oldgerman/ODGIRON/Hardware/Datasheets/Amplifier/3223.INA333.png

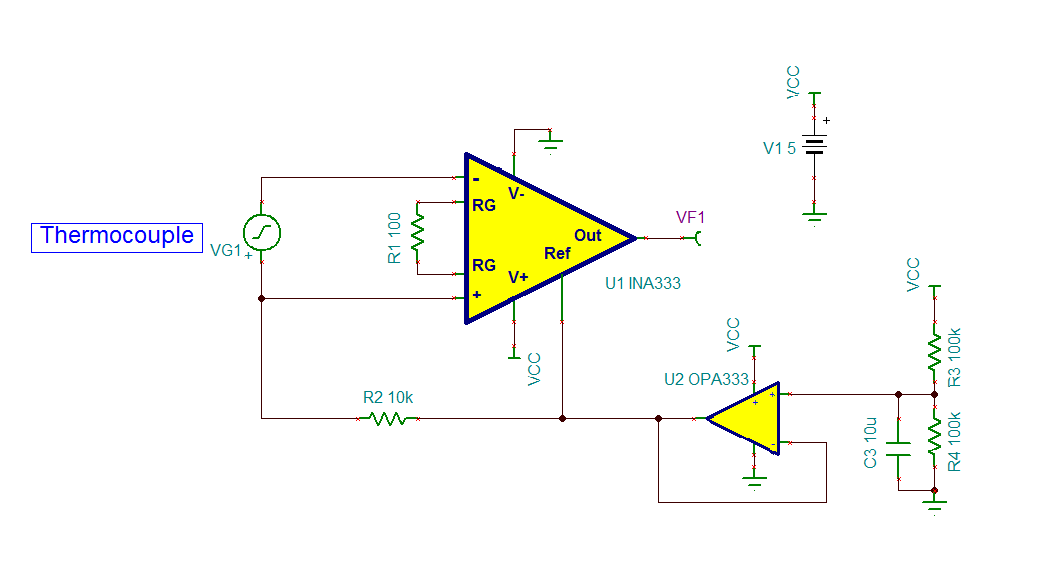
Hardware/Datasheets/Amplifier/3223.INA333.png
