oldgerman/ODGIRON/Hardware/Datasheets/Amplifier/INA333/1882.Untitled.png

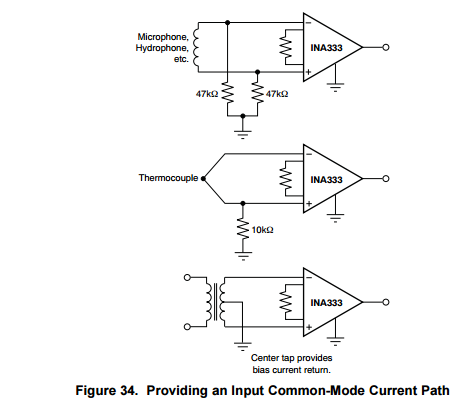
Hardware/Datasheets/Amplifier/INA333/1882.Untitled.png
