oldgerman/ODGIRON/Hardware/Datasheets/DCDC/image/MP2456_EVM_V1.jpg

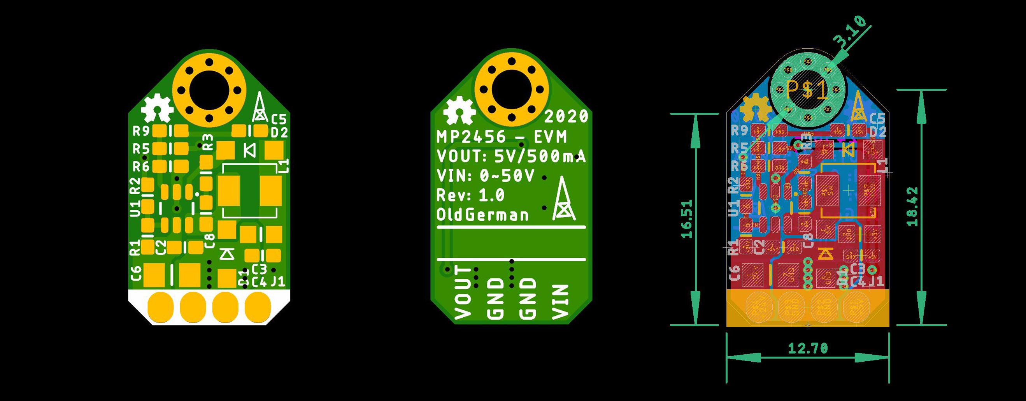
Hardware/Datasheets/DCDC/image/MP2456_EVM_V1.jpg
