oldgerman/ODGIRON/Hardware/Datasheets/DCDC/image/MP2456_EVM_V1_Module.JPG

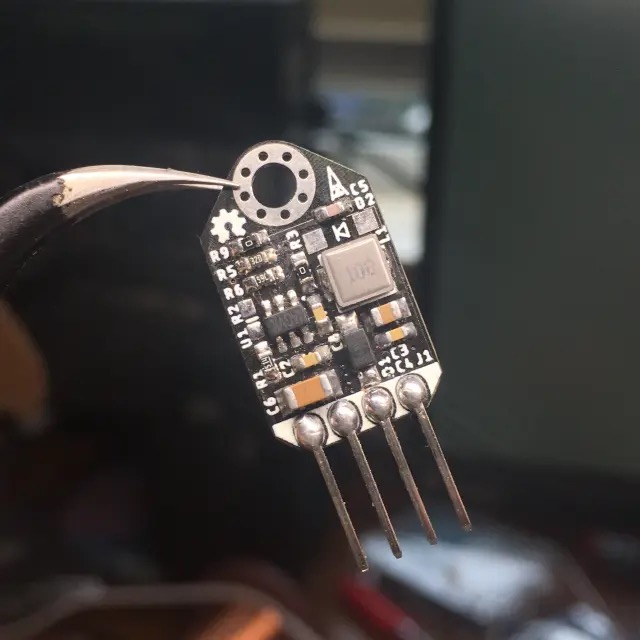
Hardware/Datasheets/DCDC/image/MP2456_EVM_V1_Module.JPG
