oldgerman/ODGIRON/Hardware/Datasheets/FUSB302/FUSB302BGEVB_-_Board/FUSB302BGEVB_-_Board.png

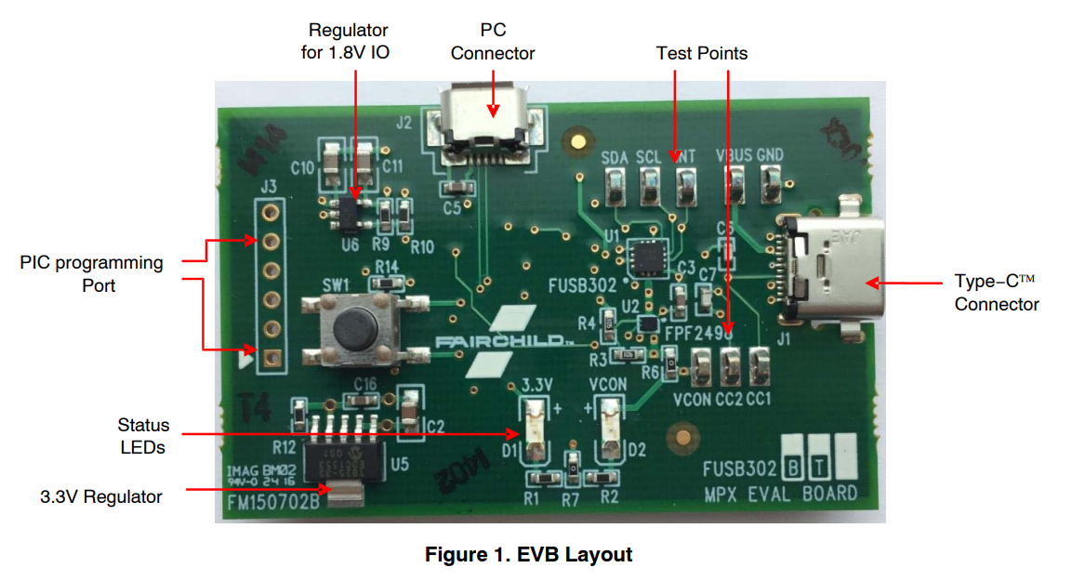
Hardware/Datasheets/FUSB302/FUSB302BGEVB_-_Board/FUSB302BGEVB_-_Board.png
