oldgerman/ODGIRON/Hardware/Datasheets/FUSB302/PD_BUDDY_SINK/pd_buddy_sink.jpg

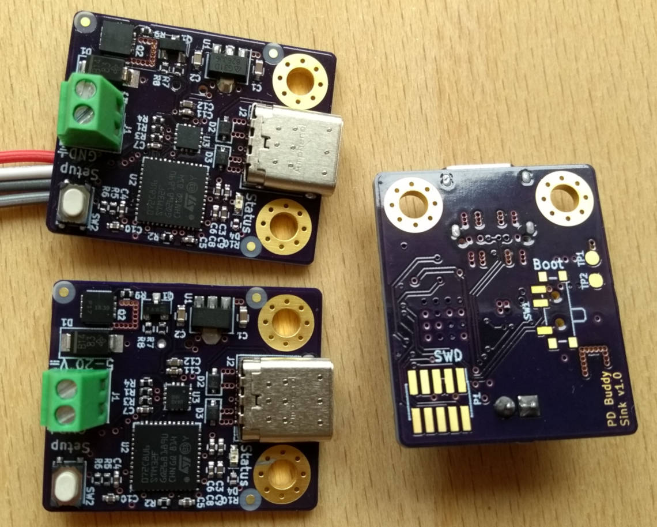
Hardware/Datasheets/FUSB302/PD_BUDDY_SINK/pd_buddy_sink.jpg
