oldgerman/ODGIRON/Hardware/Datasheets/FUSB302/USB-C Explorer/2018-03-14T04_09_01.173Z-Bot_cropped.jpg

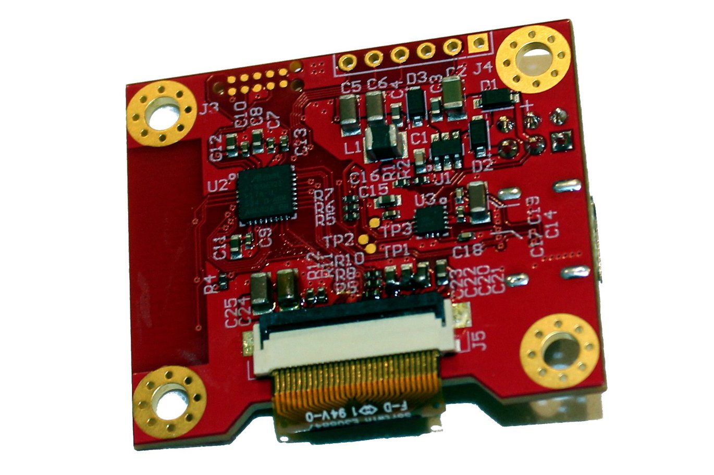
Hardware/Datasheets/FUSB302/USB-C Explorer/2018-03-14T04_09_01.173Z-Bot_cropped.jpg
