oldgerman/ODGIRON/Hardware/Datasheets/FUSB302/USB-PD-Breakout/2019-07-22T05_44_04.861Z-USB-C_PD_Breakout_Bot.jpg

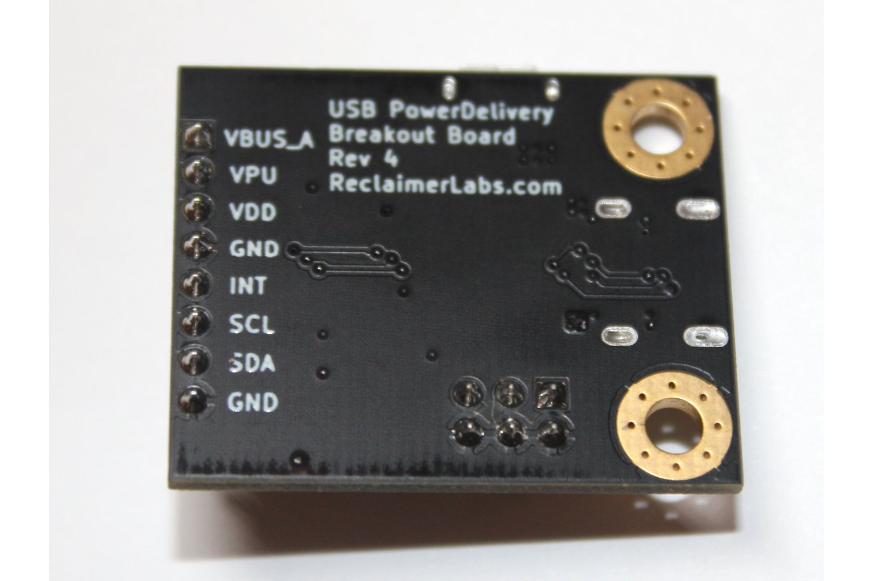
Hardware/Datasheets/FUSB302/USB-PD-Breakout/2019-07-22T05_44_04.861Z-USB-C_PD_Breakout_Bot.jpg
