oldgerman/ODGIRON/Hardware/Datasheets/FUSB302/USB-PD-Breakout/USB PowerDeilivery Breakout.jpg

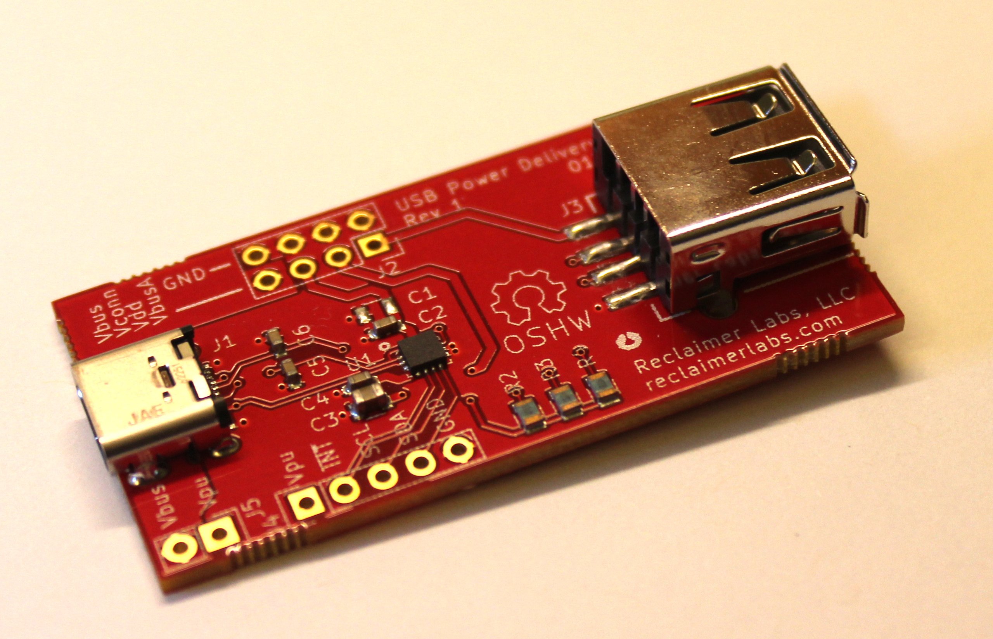
Hardware/Datasheets/FUSB302/USB-PD-Breakout/USB PowerDeilivery Breakout.jpg
