oldgerman/ODGIRON/Hardware/Datasheets/FUSB302/USB-PD-Breakout/USB PowerDeilivery Breakout.png

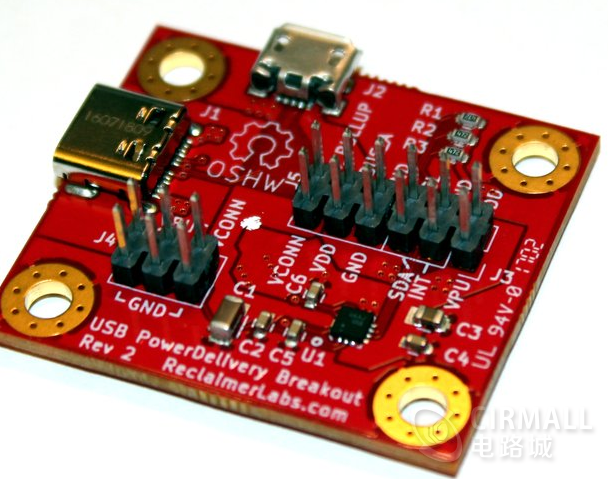
Hardware/Datasheets/FUSB302/USB-PD-Breakout/USB PowerDeilivery Breakout.png
