oldgerman/ODGIRON/Hardware/Datasheets/FUSB302/ZY12PDN/FUSB+STM_Schematic.png

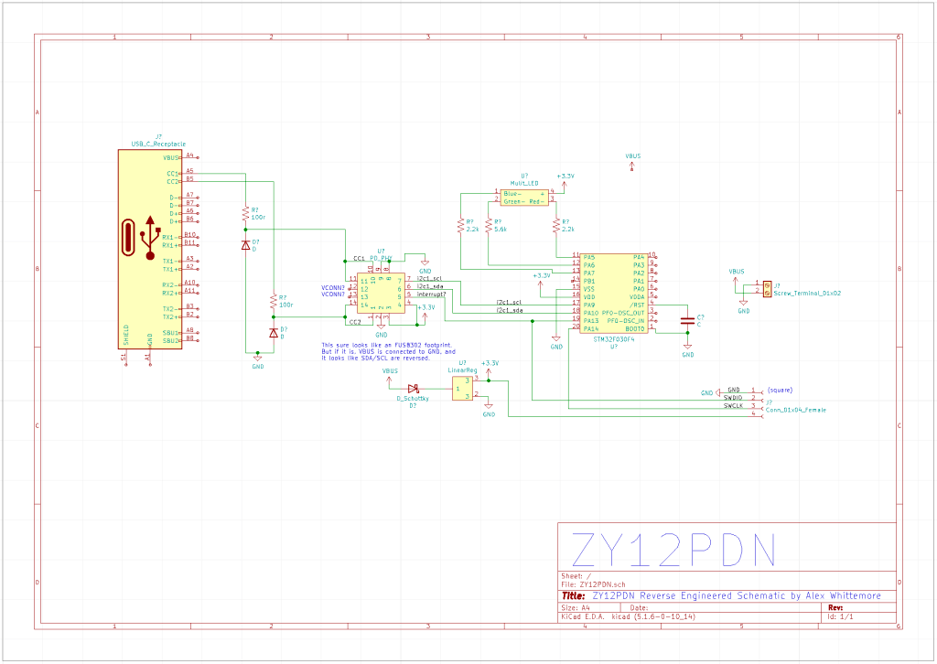
Hardware/Datasheets/FUSB302/ZY12PDN/FUSB+STM_Schematic.png
