oldgerman/ODGIRON/Hardware/Datasheets/FUSB302/产品应用/FUSB302在紫米10号移动电源中进行了应用，详情参考充电头网带来的ZMI 10号USB PD移动电源拆解.png

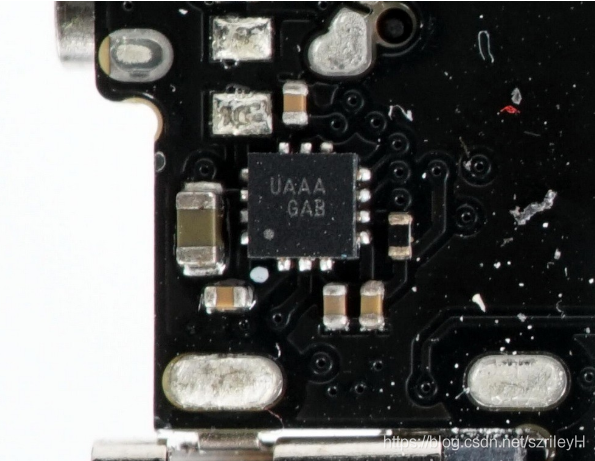
Hardware/Datasheets/FUSB302/产品应用/FUSB302在紫米10号移动电源中进行了应用，详情参考充电头网带来的ZMI 10号USB PD移动电源拆解.png
