oldgerman/ODGIRON/Hardware/Datasheets/MEMS/LIS2DH12/SEN0224-detail-001_564x376.jpg

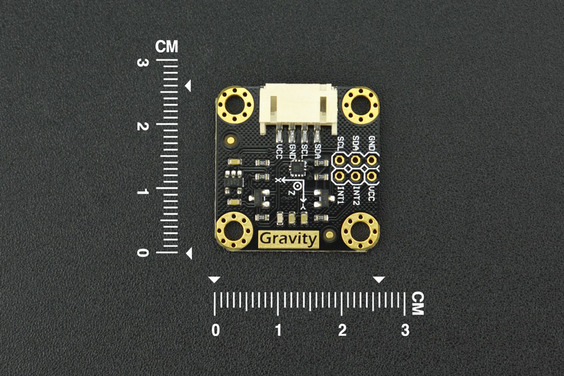
Hardware/Datasheets/MEMS/LIS2DH12/SEN0224-detail-001_564x376.jpg
