oldgerman/ODGIRON/Hardware/Datasheets/MEMS/LIS2DH12/SEN0224.jpg

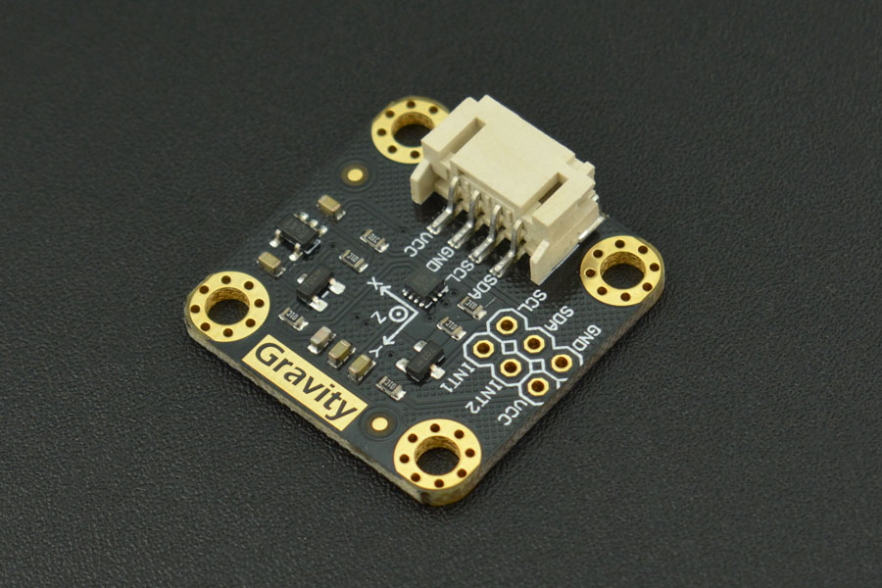
Hardware/Datasheets/MEMS/LIS2DH12/SEN0224.jpg
