oldgerman/ODGIRON/Hardware/Datasheets/MEMS/LIS3DH/Adafruit-LIS3DH-Breakout-PCB-master/3.3V电源从ic下面走没问题.png

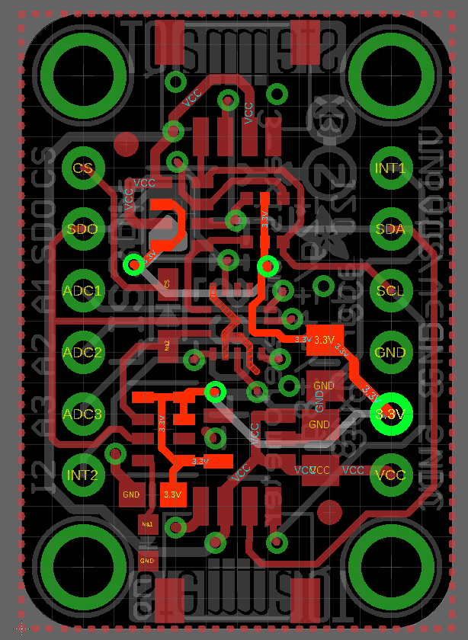
Hardware/Datasheets/MEMS/LIS3DH/Adafruit-LIS3DH-Breakout-PCB-master/3.3V电源从ic下面走没问题.png
