oldgerman/ODGIRON/Hardware/Datasheets/MEMS/LIS3DH/Adafruit-LIS3DH-Breakout-PCB-master/QWIC版本.jpg

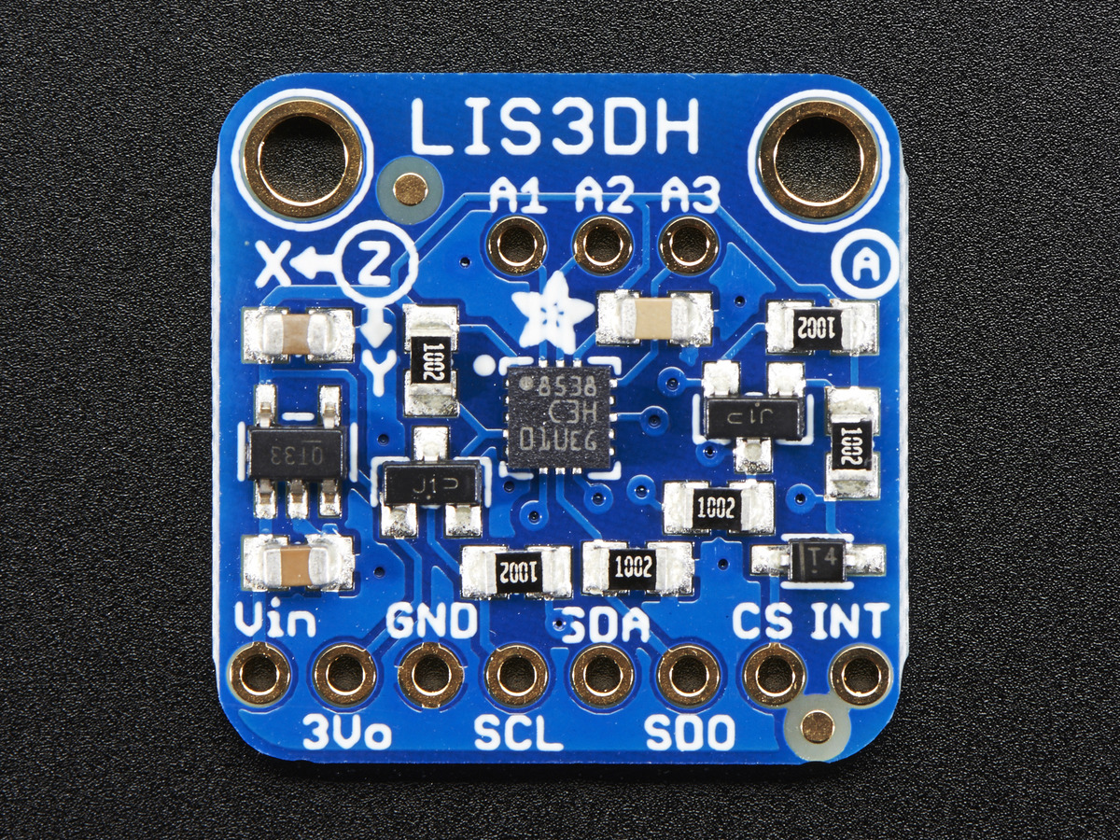
Hardware/Datasheets/MEMS/LIS3DH/Adafruit-LIS3DH-Breakout-PCB-master/QWIC版本.jpg
