oldgerman/ODGIRON/Hardware/Datasheets/MEMS/MPU9250/15335_9DoF_IMU_EagleFiles/20201105164445.png

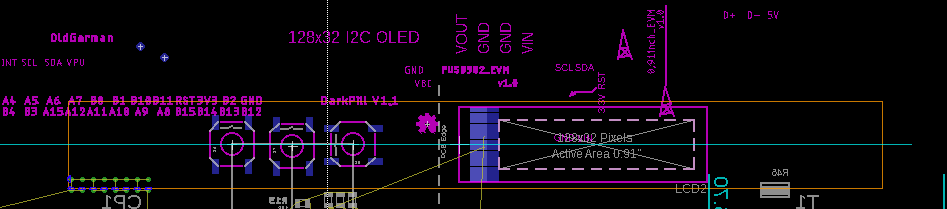
Hardware/Datasheets/MEMS/MPU9250/15335_9DoF_IMU_EagleFiles/20201105164445.png
