oldgerman/ODGIRON/Hardware/Datasheets/MEMS/MPU9250/15335_9DoF_IMU_EagleFiles/20201105170118.png

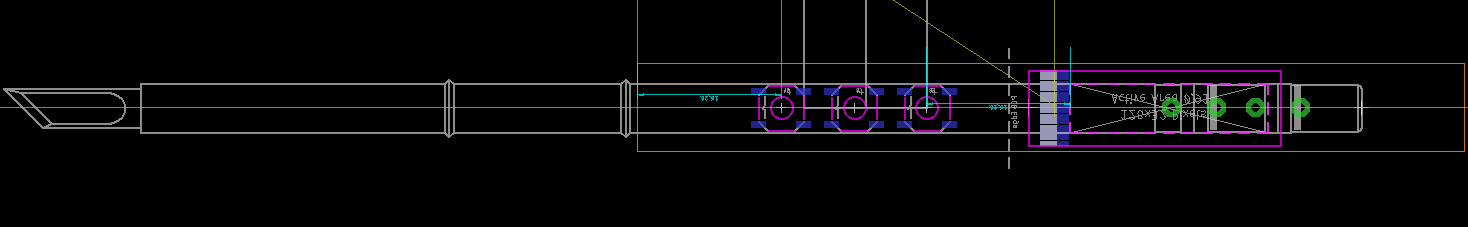
Hardware/Datasheets/MEMS/MPU9250/15335_9DoF_IMU_EagleFiles/20201105170118.png
