oldgerman/ODGIRON/Hardware/Datasheets/MOSFET/MOSFET共漏极、共栅极、共源极接法.jpg

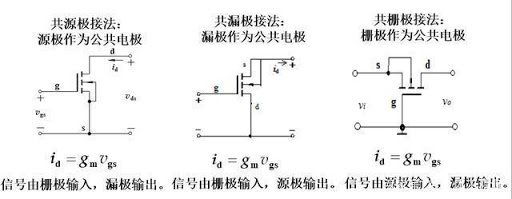
Hardware/Datasheets/MOSFET/MOSFET共漏极、共栅极、共源极接法.jpg
