oldgerman/ODGIRON/Hardware/Datasheets/MOSFET/schematicpwm.png

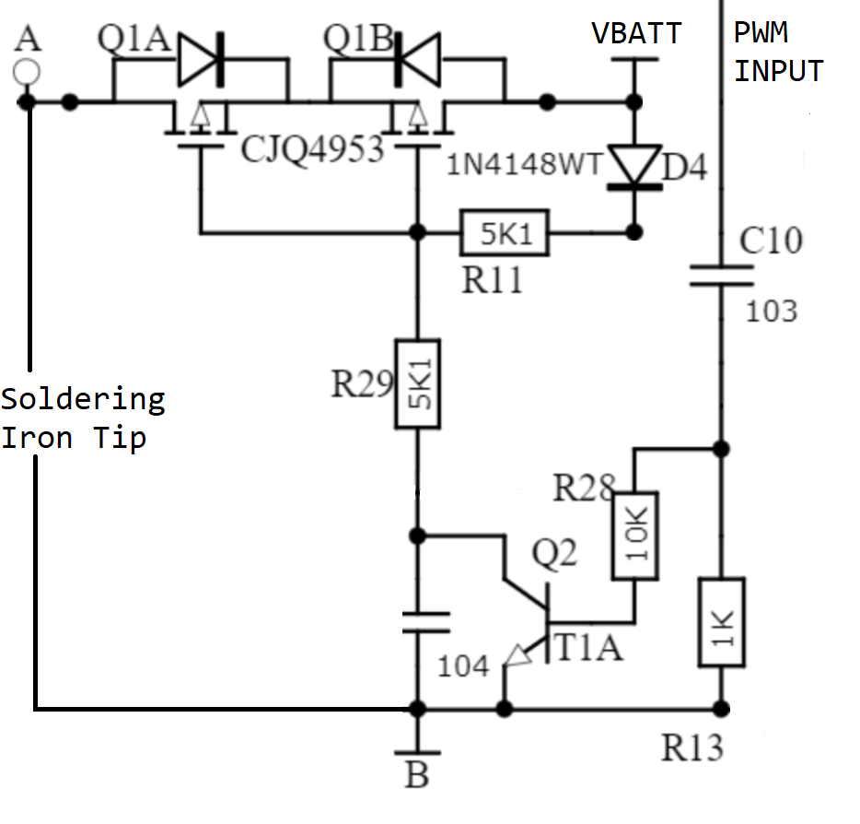
Hardware/Datasheets/MOSFET/schematicpwm.png
