oldgerman/ODGIRON/Hardware/Datasheets/MOSFET/Sic4-4_graf01.gif

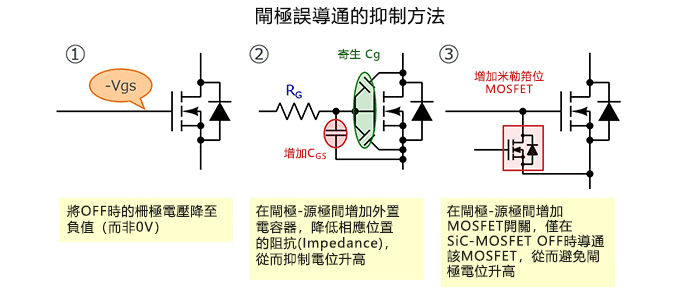
Hardware/Datasheets/MOSFET/Sic4-4_graf01.gif
