oldgerman/ODGIRON/Hardware/Datasheets/STUSB4500/15801-SparkFun_Power_Delivery_Board_-_USB-C__Qwiic_-02.jpg

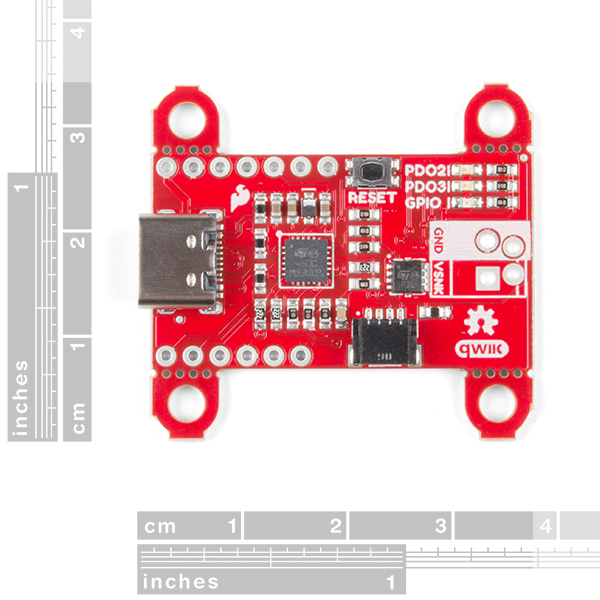
Hardware/Datasheets/STUSB4500/15801-SparkFun_Power_Delivery_Board_-_USB-C__Qwiic_-02.jpg
