oldgerman/ODGIRON/Hardware/Datasheets/STUSB4500/15801-SparkFun_Power_Delivery_Board_-_USB-C__Qwiic_-03.jpg

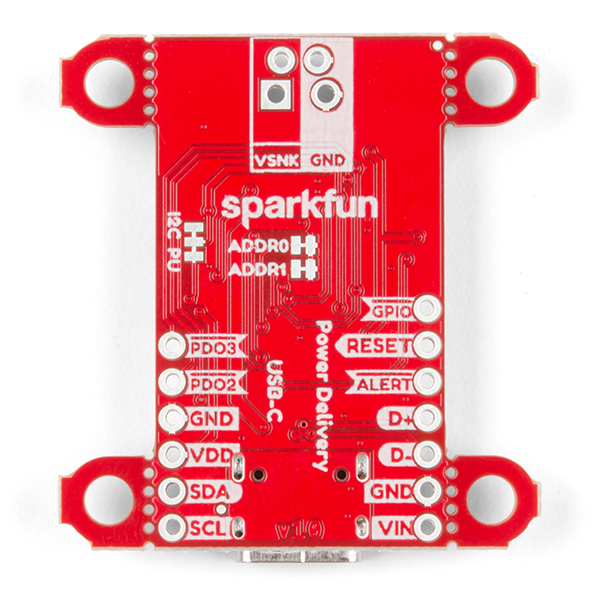
Hardware/Datasheets/STUSB4500/15801-SparkFun_Power_Delivery_Board_-_USB-C__Qwiic_-03.jpg
