oldgerman/ODGIRON/Hardware/Datasheets/T12烙铁头结构/973c747dd97206d3.jpg

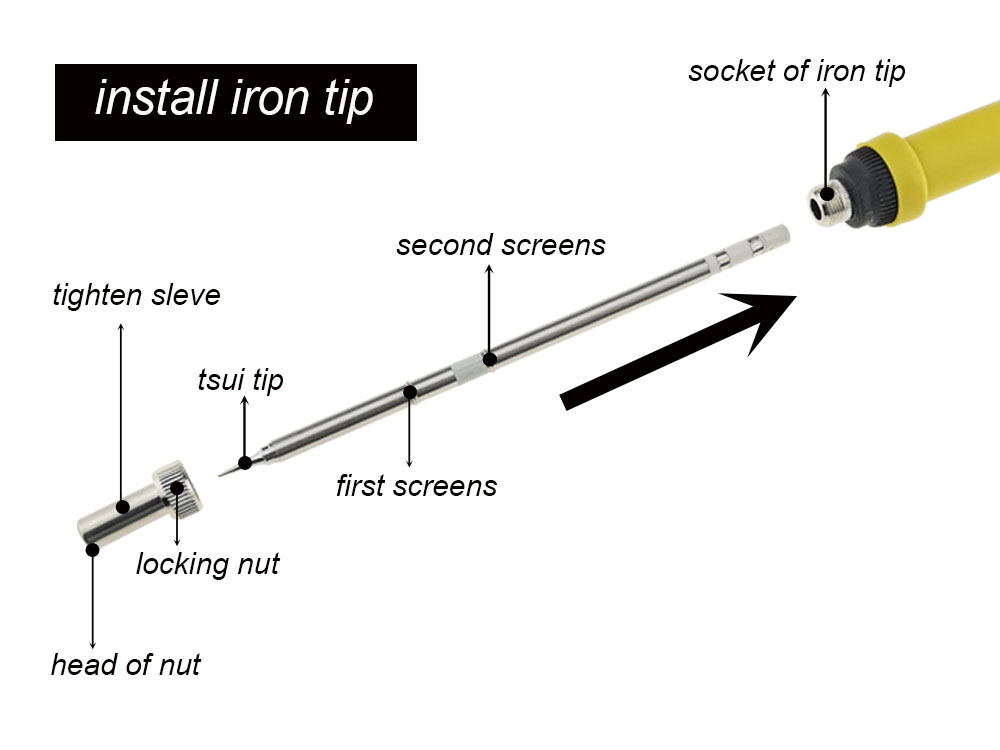
Hardware/Datasheets/T12烙铁头结构/973c747dd97206d3.jpg
