oldgerman/ODGIRON/Hardware/Datasheets/T12烙铁头结构/HTB1_OT5SpXXXXbtXXXXq6xXFXXXs.webp

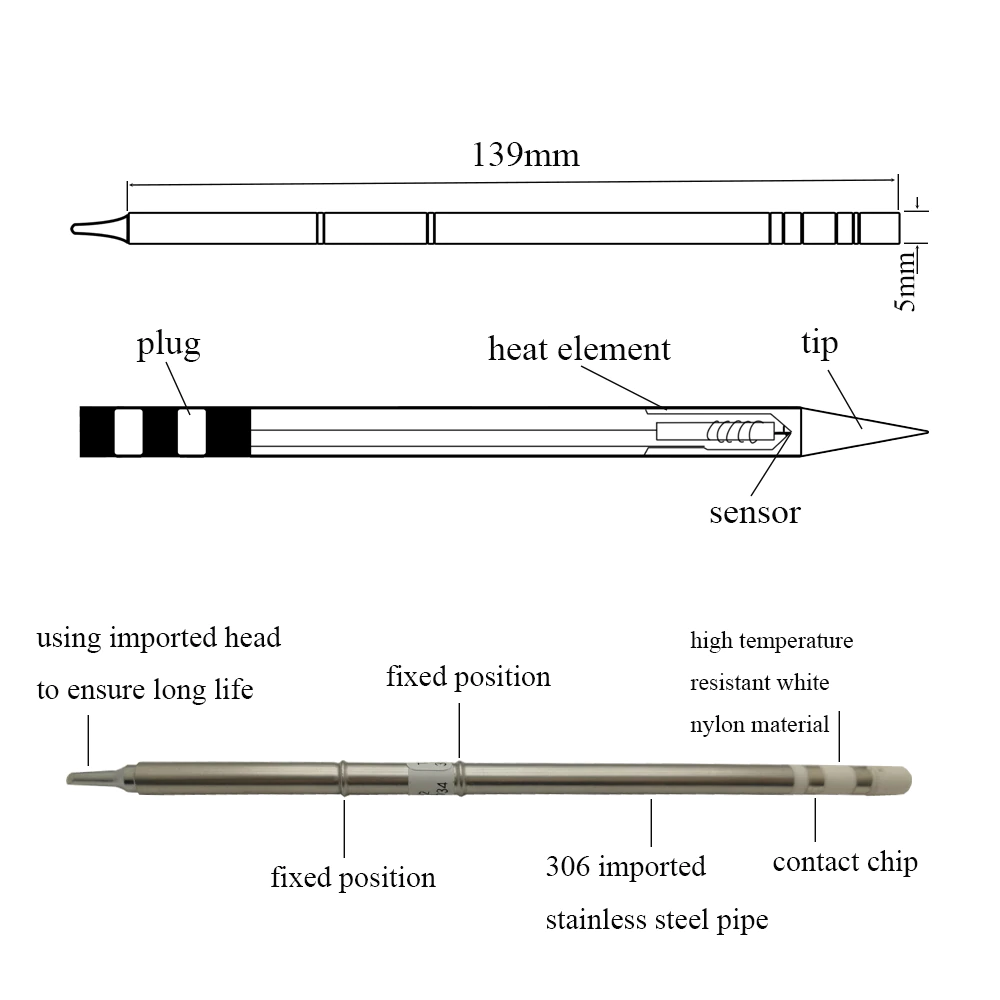
Hardware/Datasheets/T12烙铁头结构/HTB1_OT5SpXXXXbtXXXXq6xXFXXXs.webp
