oldgerman/ODGIRON/Hardware/Datasheets/T12烙铁头结构/HTB1r25GEf5TBuNjSspmq6yDRVXaR.jpg

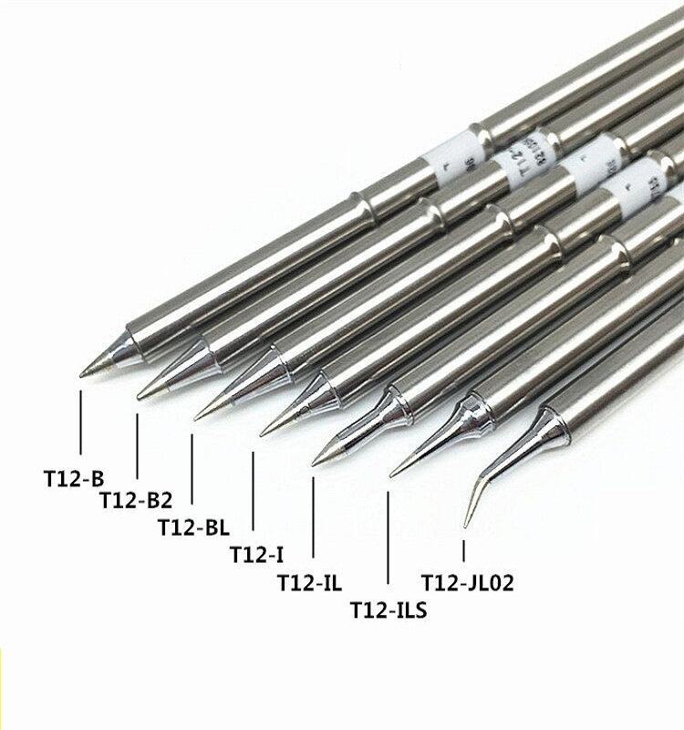
Hardware/Datasheets/T12烙铁头结构/HTB1r25GEf5TBuNjSspmq6yDRVXaR.jpg
