oldgerman/ODGIRON/Hardware/Datasheets/T12烙铁头结构/image-16055.jpg

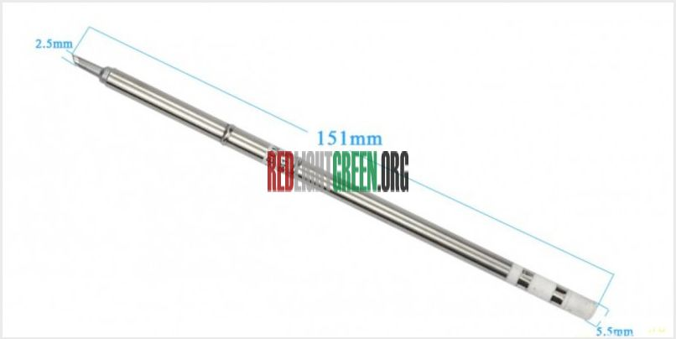
Hardware/Datasheets/T12烙铁头结构/image-16055.jpg
