oldgerman/ODGIRON/Hardware/Datasheets/T12烙铁头结构/s-l1600.jpg

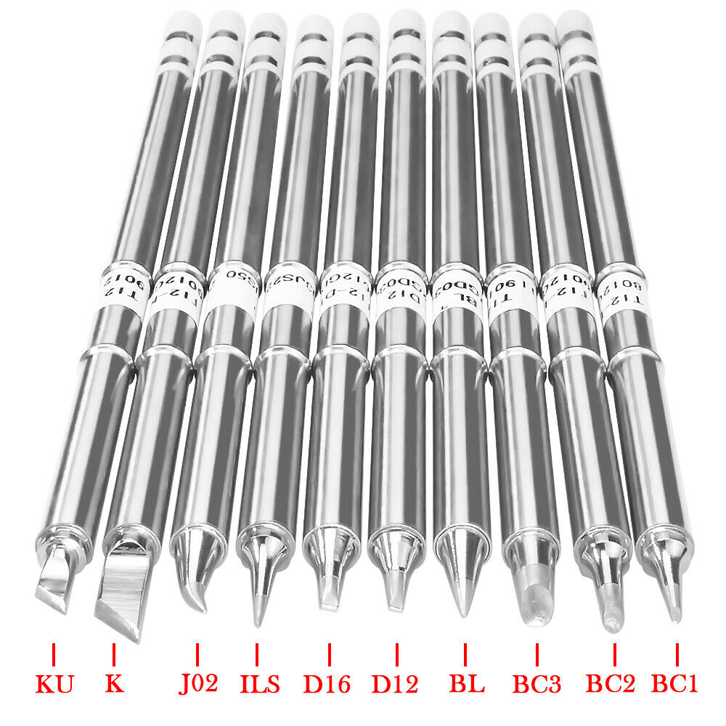
Hardware/Datasheets/T12烙铁头结构/s-l1600.jpg
