oldgerman/ODGIRON/Hardware/Datasheets/T12烙铁头结构/yhst-139912697762728_2641_11230514.jpg

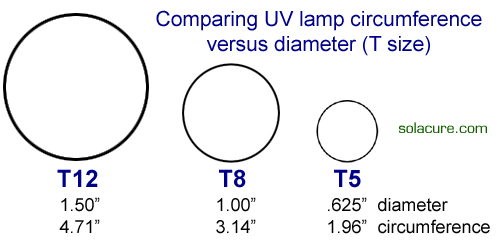
Hardware/Datasheets/T12烙铁头结构/yhst-139912697762728_2641_11230514.jpg
