oldgerman/ODGIRON/Hardware/Datasheets/TPD8S300/tpd8s300evm_tpd8s300evm-board-image-top.jpg

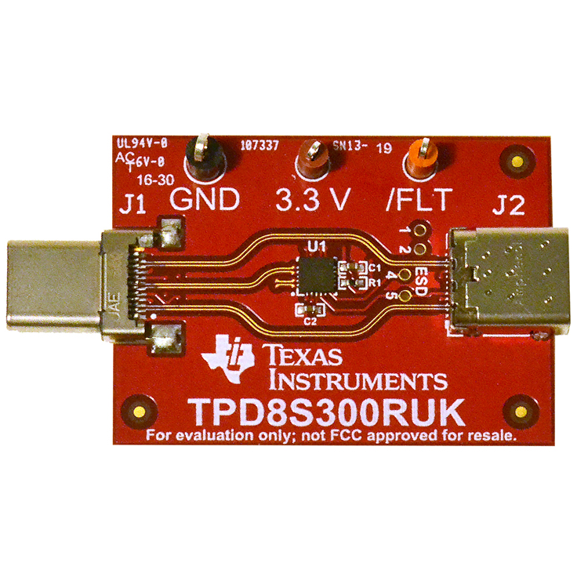
Hardware/Datasheets/TPD8S300/tpd8s300evm_tpd8s300evm-board-image-top.jpg
