oldgerman/ODGIRON/Hardware/Datasheets/TPD8S300/小米Mi Pro 15“ 使用了.jpg

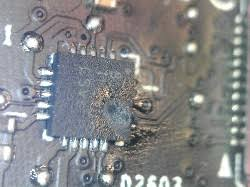
Hardware/Datasheets/TPD8S300/小米Mi Pro 15“ 使用了.jpg
