oldgerman/ODGIRON/Hardware/Datasheets/TPS65981EVM/TIM截图20201128180212.png

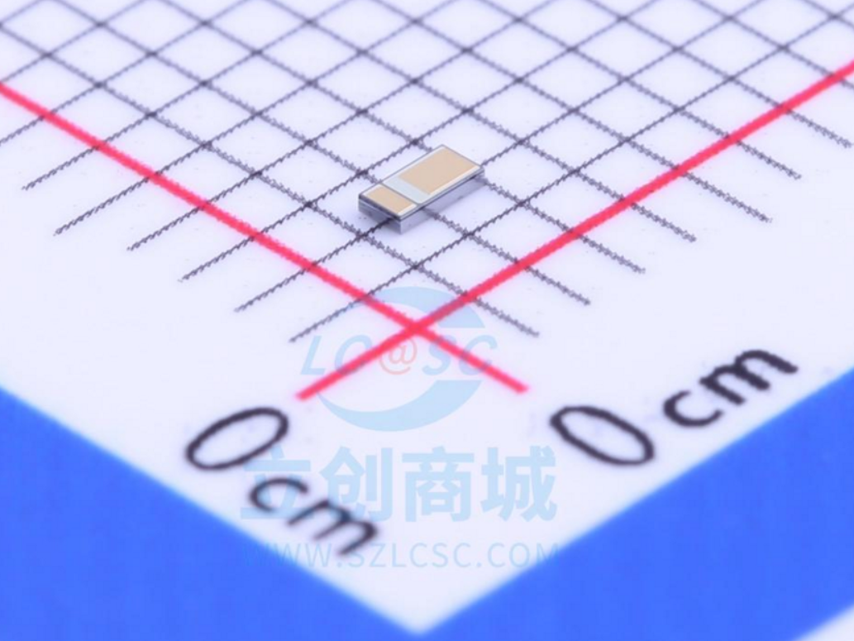
Hardware/Datasheets/TPS65981EVM/TIM截图20201128180212.png
