oldgerman/ODGIRON/Hardware/Datasheets/TVS/ST - ESDA产品线命名规范.png

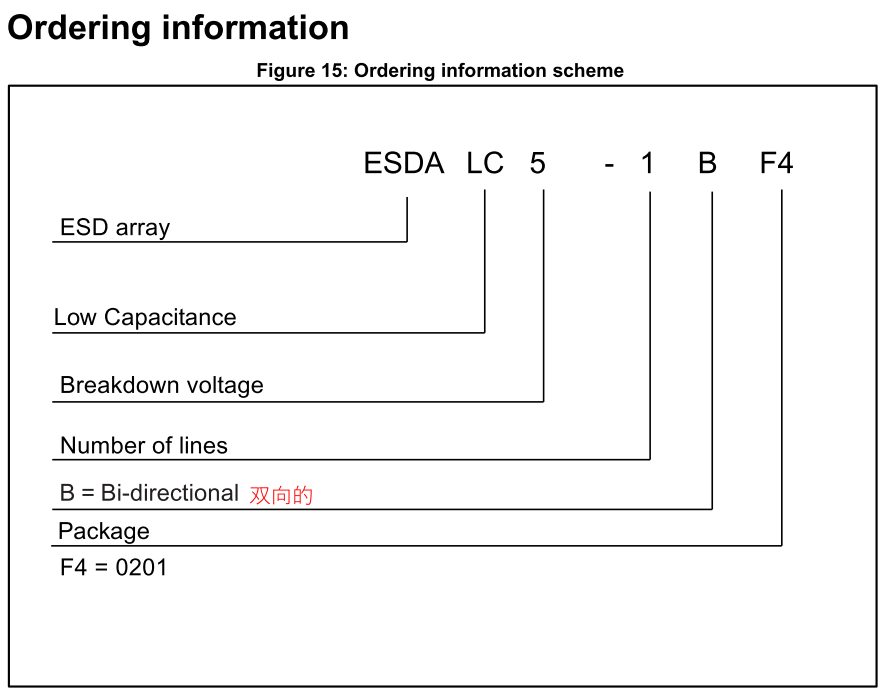
Hardware/Datasheets/TVS/ST - ESDA产品线命名规范.png
