oldgerman/ODGIRON/Hardware/Datasheets/保险丝夹/fuse-clip-dimensions-5x20mm.jpg

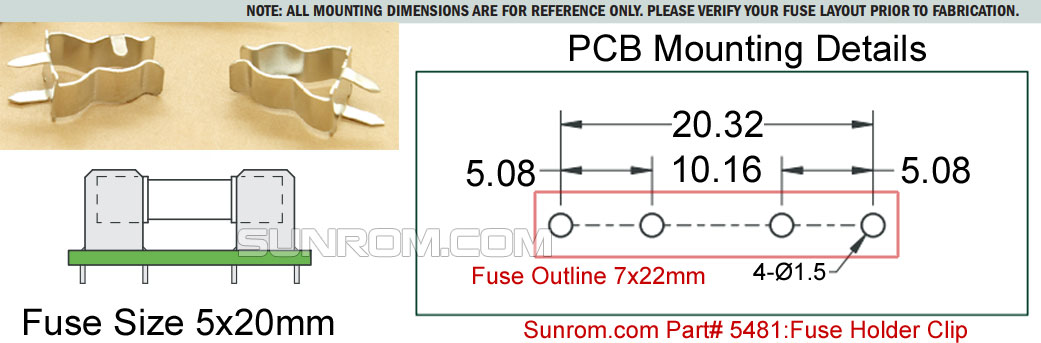
Hardware/Datasheets/保险丝夹/fuse-clip-dimensions-5x20mm.jpg
