oldgerman/ODGIRON/Hardware/Datasheets/电流采样/INA1xx/LC INA18X方案验证版/sch.png

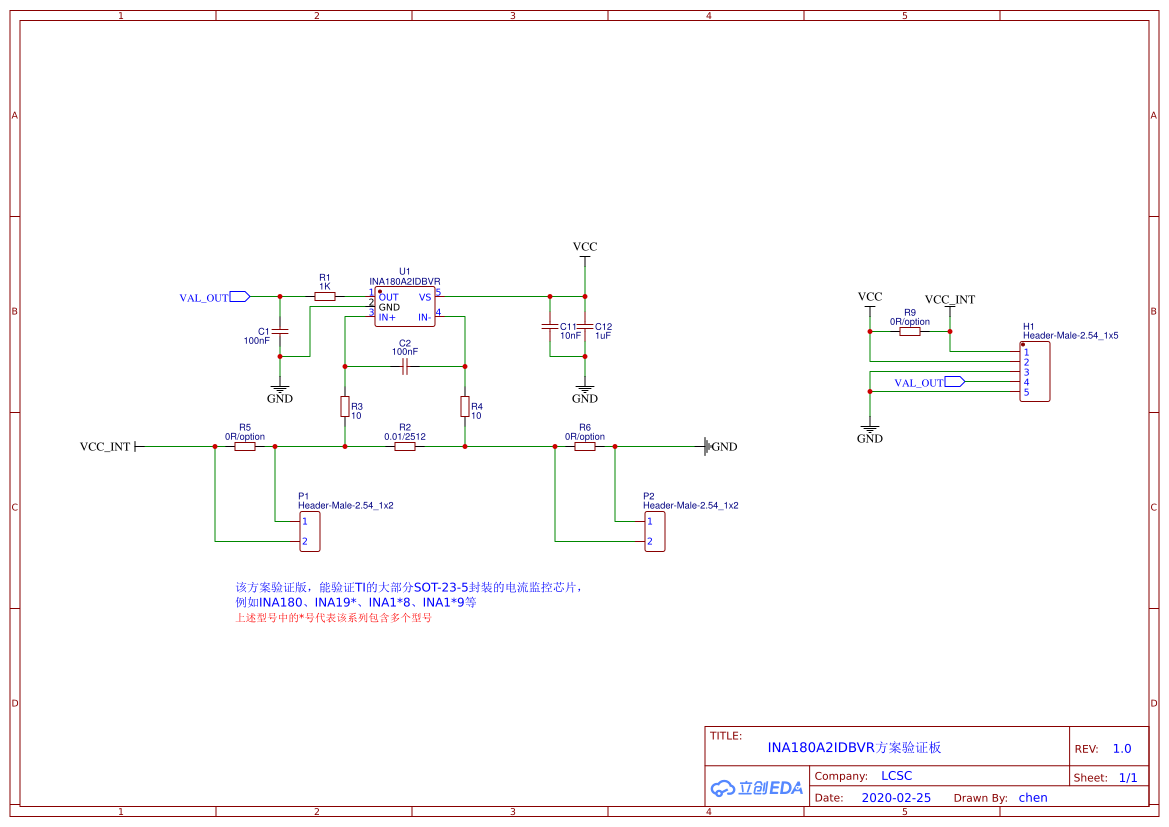
Hardware/Datasheets/电流采样/INA1xx/LC INA18X方案验证版/sch.png
