oldgerman/ODGIRON/Hardware/Datasheets/电流采样/INA2xx/INA219 -GreatScott!/15176-Zio_Current_and_Voltage_Sensor_-_INA219__Qwiic_-04.jpg

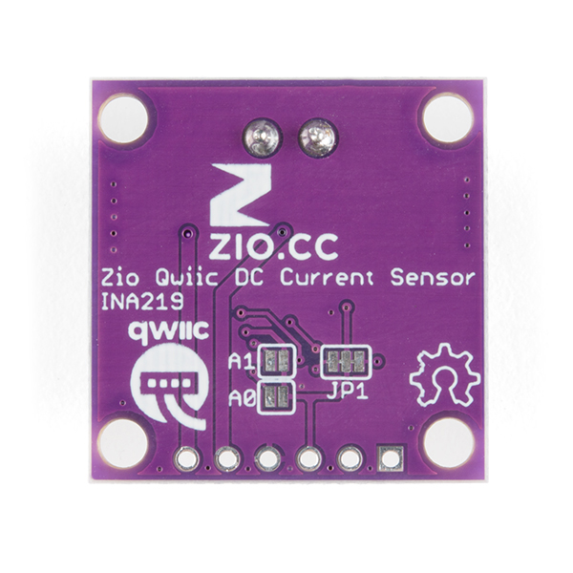
Hardware/Datasheets/电流采样/INA2xx/INA219 -GreatScott!/15176-Zio_Current_and_Voltage_Sensor_-_INA219__Qwiic_-04.jpg
