oldgerman/ODGIRON/Hardware/Datasheets/电流采样/INA2xx/INA219 -GreatScott!/20201031151808.png

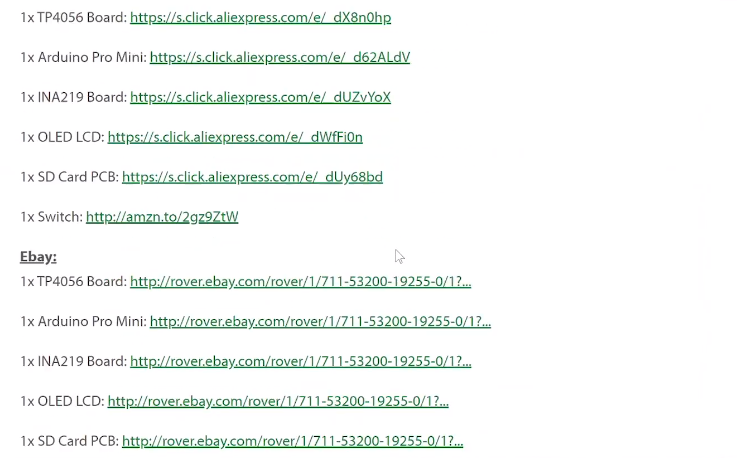
Hardware/Datasheets/电流采样/INA2xx/INA219 -GreatScott!/20201031151808.png
