oldgerman/ODGIRON/Hardware/Datasheets/电流采样/INA2xx/INA226 - I2C/7802.sch.png

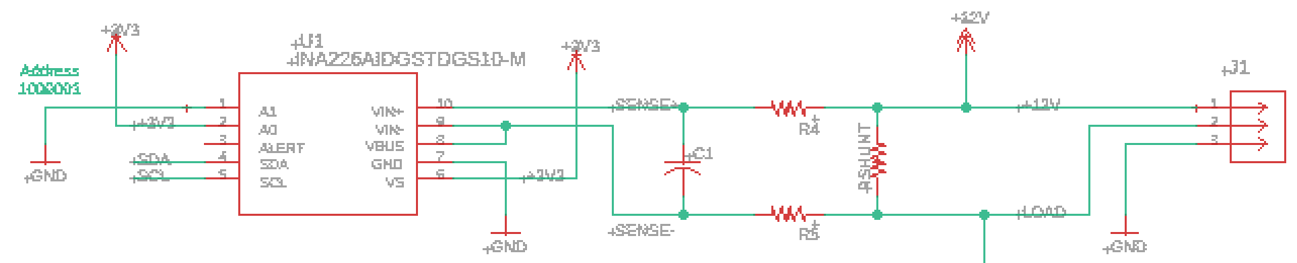
Hardware/Datasheets/电流采样/INA2xx/INA226 - I2C/7802.sch.png
