oldgerman/ODGIRON/Hardware/Datasheets/电流采样/INA2xx/INA226 - I2C/ARDUINO - INA226.jpg

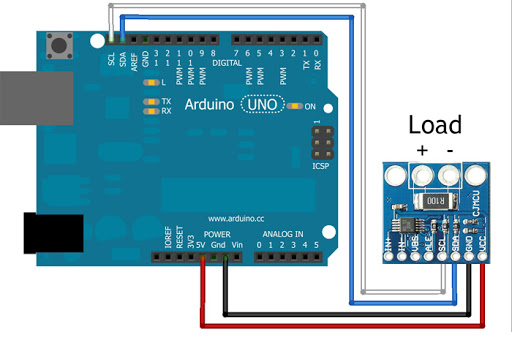
Hardware/Datasheets/电流采样/INA2xx/INA226 - I2C/ARDUINO - INA226.jpg
