oldgerman/ODGIRON/Hardware/Datasheets/电流采样/INA2xx/INA226 - I2C/IAN226A.png-1230x0.png

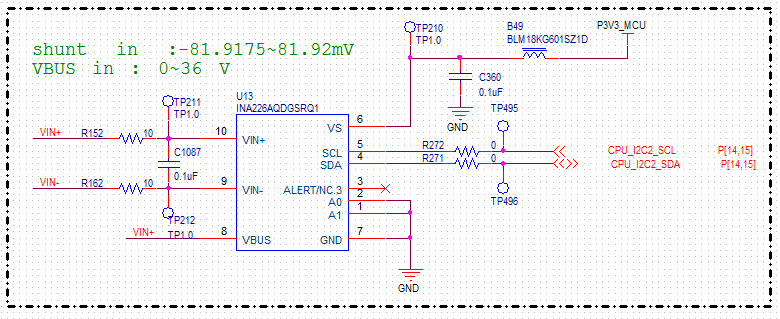
Hardware/Datasheets/电流采样/INA2xx/INA226 - I2C/IAN226A.png-1230x0.png
