oldgerman/ODGIRON/Hardware/Datasheets/电流采样/INA2xx/INA226 - I2C/INA226 - MOLDULE.jpg

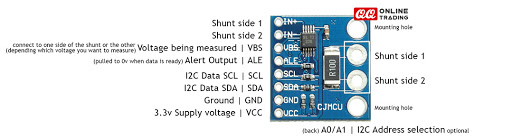
Hardware/Datasheets/电流采样/INA2xx/INA226 - I2C/INA226 - MOLDULE.jpg
