oldgerman/ODGIRON/Hardware/Datasheets/电流采样/INA2xx/INA260/4226_kit_ORIG_2019_04.jpg

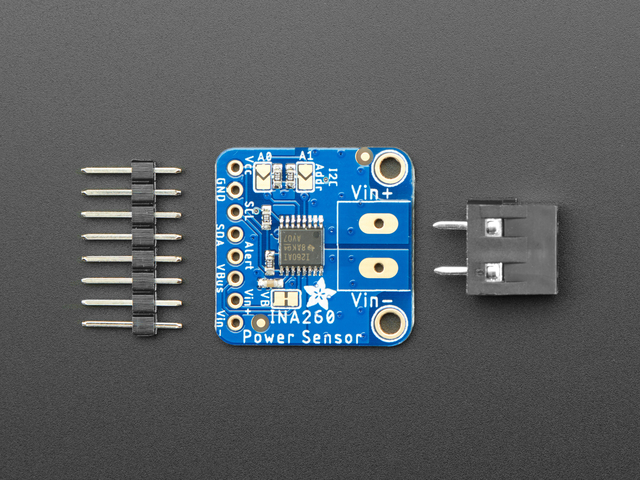
Hardware/Datasheets/电流采样/INA2xx/INA260/4226_kit_ORIG_2019_04.jpg
