oldgerman/ODGIRON/Hardware/Datasheets/电流采样/si8540.png

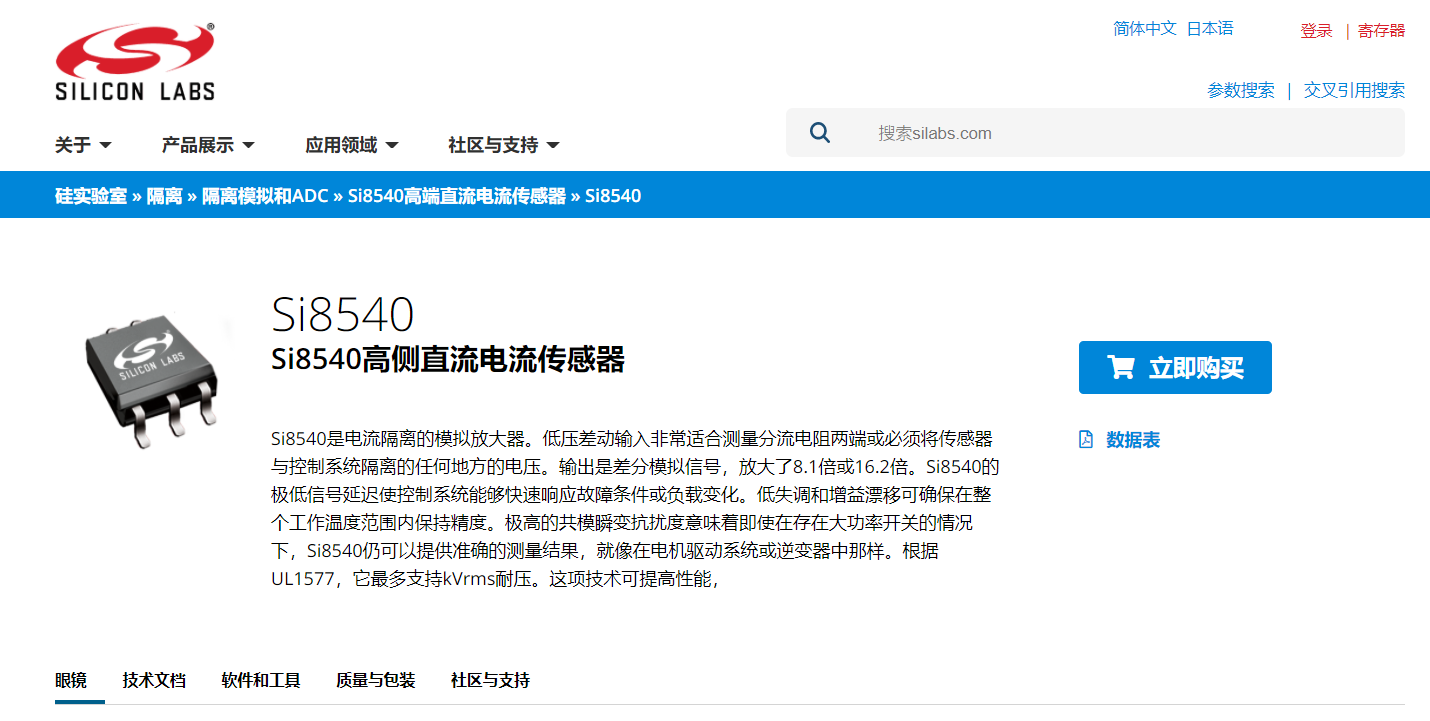
Hardware/Datasheets/电流采样/si8540.png
