oldgerman/ODGIRON/Hardware/Datasheets/霍尔传感器/Si7210/1509443882996060021th.jpg

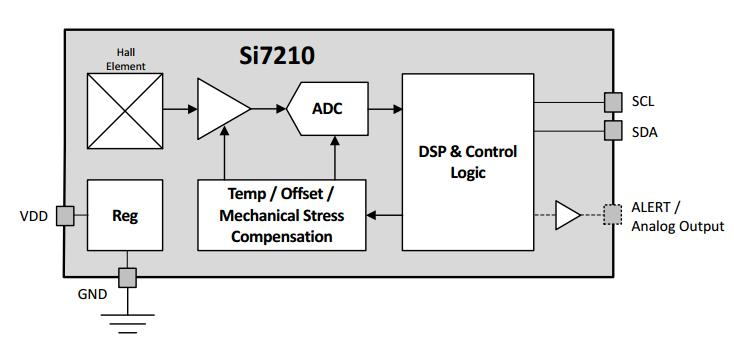
Hardware/Datasheets/霍尔传感器/Si7210/1509443882996060021th.jpg
