oldgerman/ODGIRON/Hardware/Datasheets/霍尔传感器/Si7210/maxresdefault.jpg

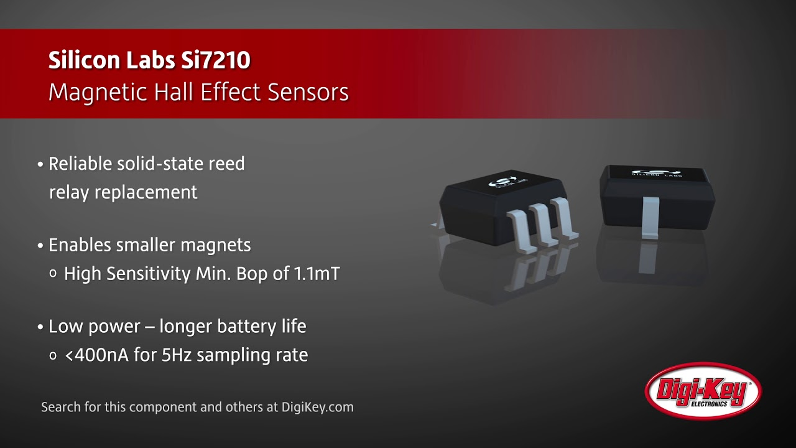
Hardware/Datasheets/霍尔传感器/Si7210/maxresdefault.jpg
