oldgerman/ODGIRON/Hardware/PCB_Project/HAKKO_191-212/fg101_p-1000x1000.jpg

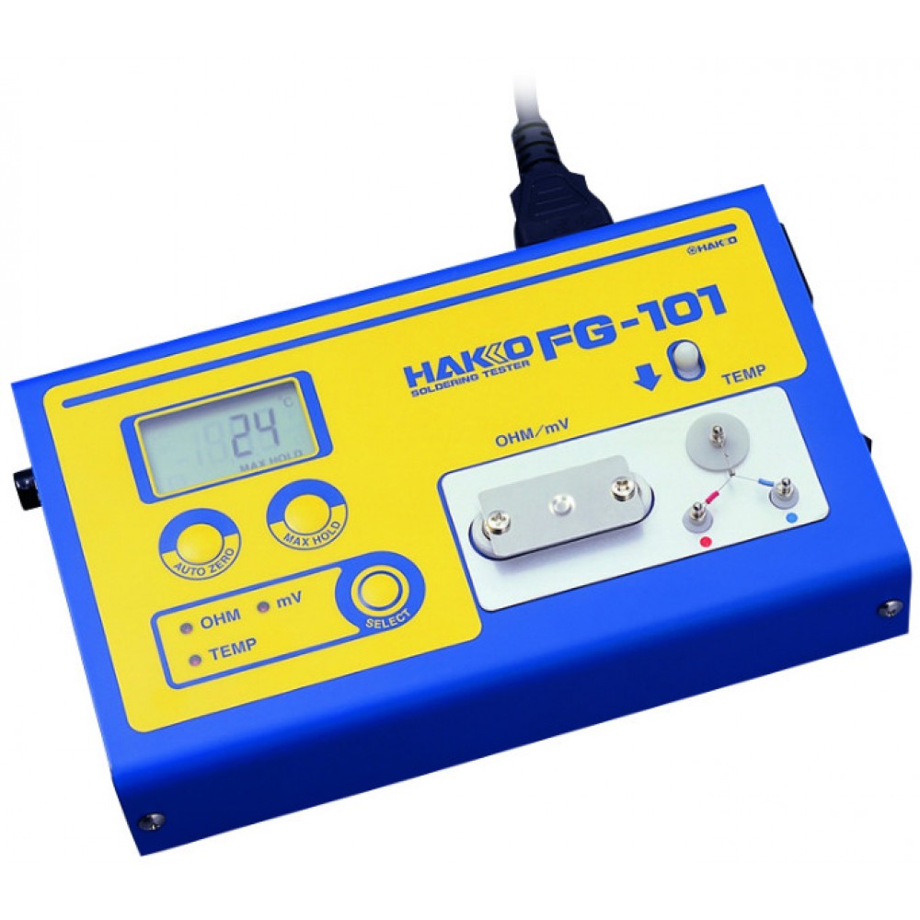
Hardware/PCB_Project/HAKKO_191-212/fg101_p-1000x1000.jpg
