oldgerman/ODGIRON/Hardware/PCB_Project/HAKKO_191-212/image-1436169323486.jpg

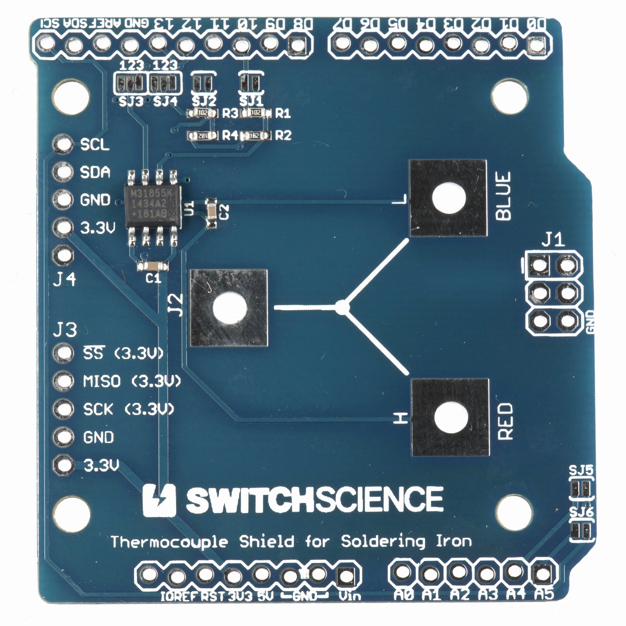
Hardware/PCB_Project/HAKKO_191-212/image-1436169323486.jpg
