oldgerman/ODGIRON/Hardware/PCB_Project/HAKKO_191-212/image-1436169334115.jpg

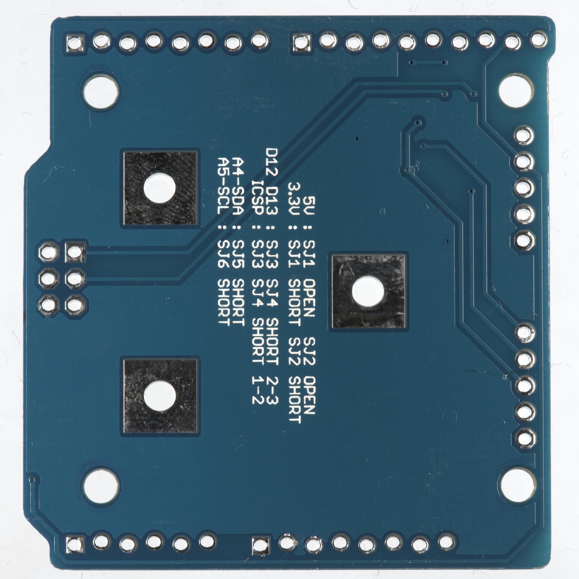
Hardware/PCB_Project/HAKKO_191-212/image-1436169334115.jpg
