oldgerman/ODGIRON/Hardware/PCB_Project/HAKKO_191-212/image-1436170054130.jpg

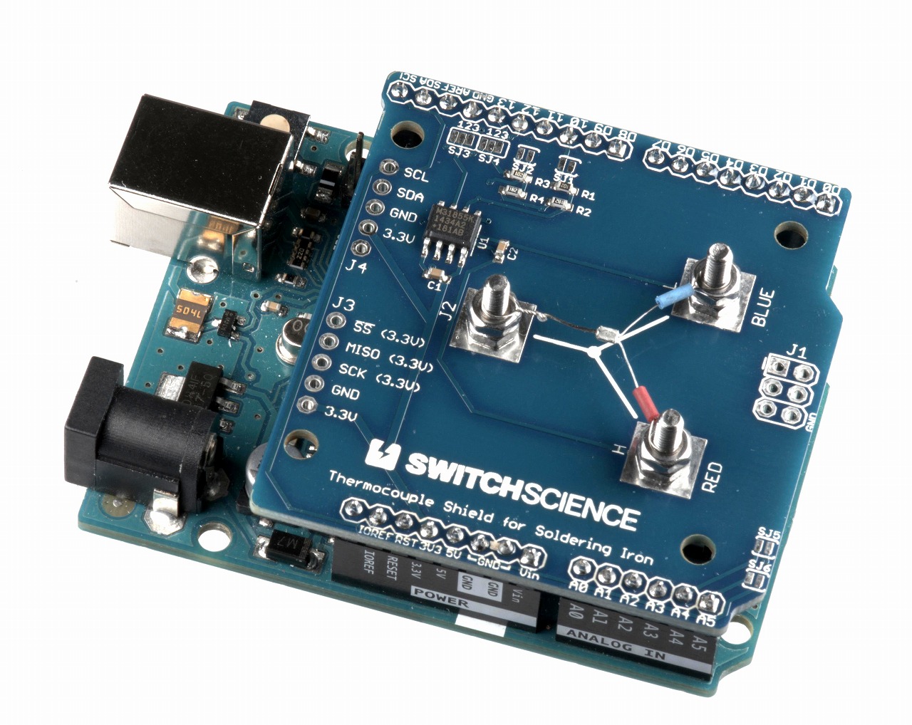
Hardware/PCB_Project/HAKKO_191-212/image-1436170054130.jpg
