oldgerman/ODGIRON/Hardware/PCB_Project/HAKKO_191-212/Thermocouple_shield4.jpg

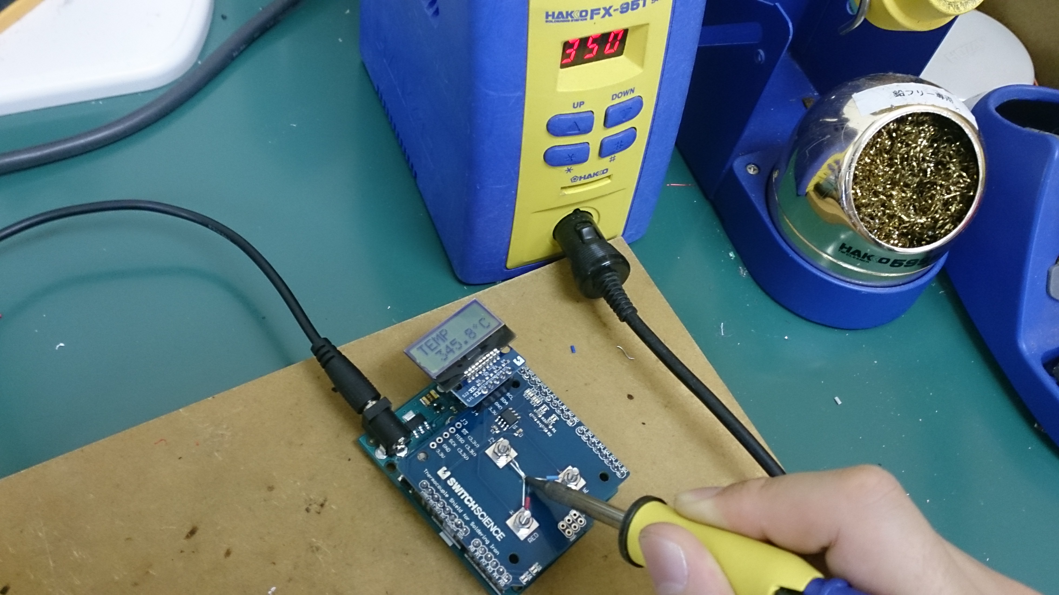
Hardware/PCB_Project/HAKKO_191-212/Thermocouple_shield4.jpg
