oldgerman/ODGIRON/Hardware/PCB_Project/ODGIRON-v1.0-F4x1-0412/Images/brd_F4x1 - 副本.png

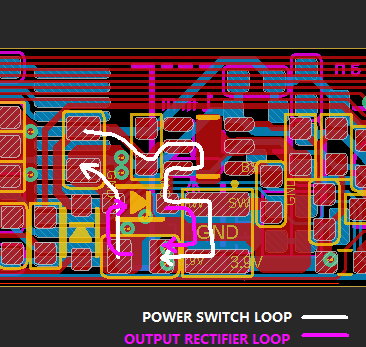
Hardware/PCB_Project/ODGIRON-v1.0-F4x1-0412/Images/brd_F4x1 - 副本.png
