oldgerman/ODGIRON/Hardware/PCB_Project/ODGIRON-v1.0-F4x1-0412/Images/jlcXN4Y78J1ODUDtop-4480x3200.png

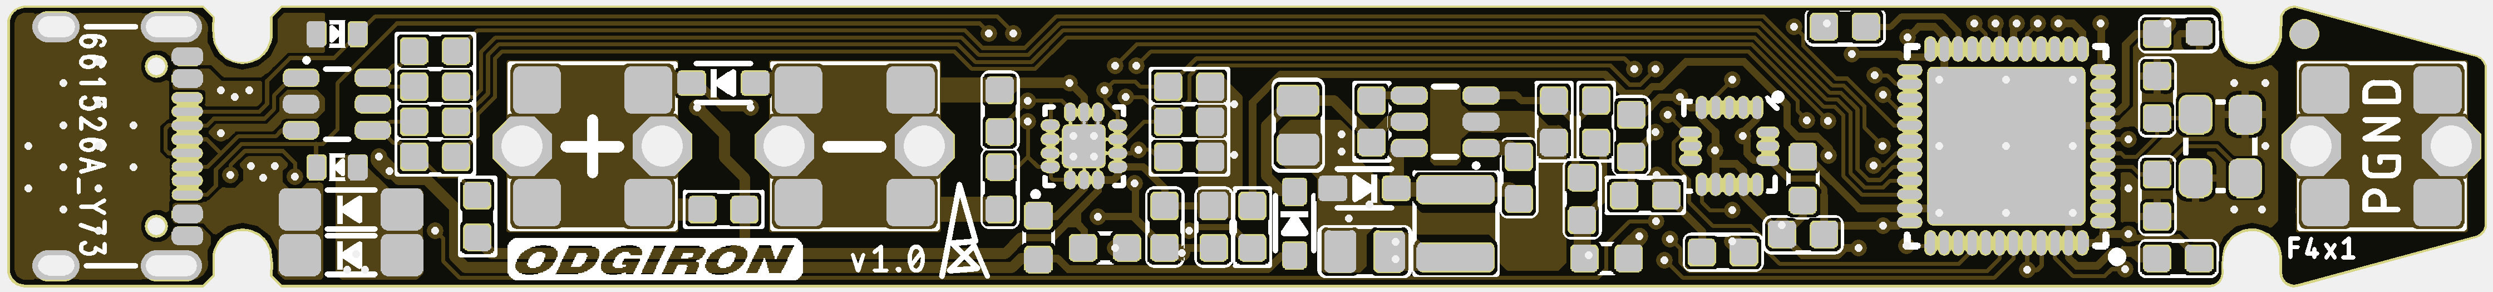
Hardware/PCB_Project/ODGIRON-v1.0-F4x1-0412/Images/jlcXN4Y78J1ODUDtop-4480x3200.png
