oldgerman/ODGIRON/Hardware/PCB_Project/ODGIRON-v1.0-F4x1-0412/Images/ODGIRON_F4x1_v1.0_Kicad_3D-view.png

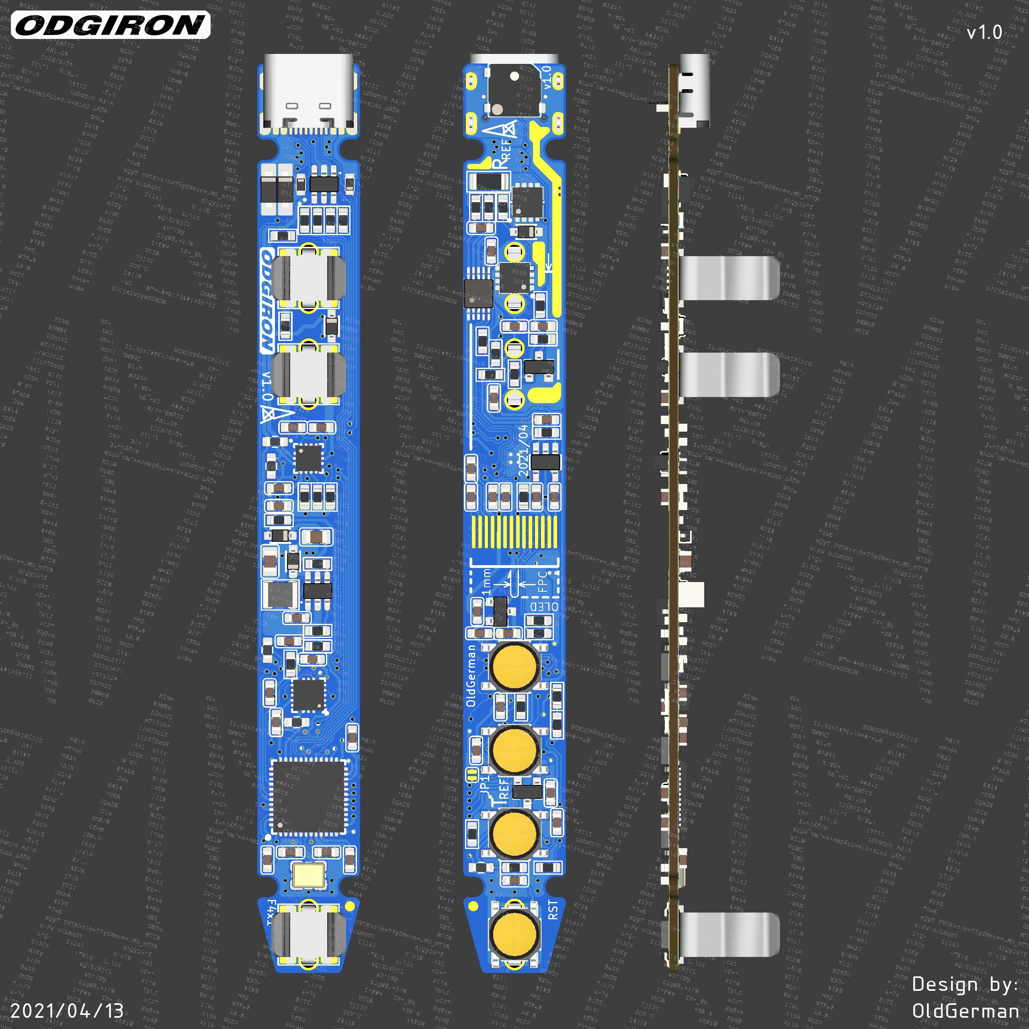
Hardware/PCB_Project/ODGIRON-v1.0-F4x1-0412/Images/ODGIRON_F4x1_v1.0_Kicad_3D-view.png
