oldgerman/ODGIRON/Hardware/SW_Project/20210327_IMG/sw外壳设计(0).png

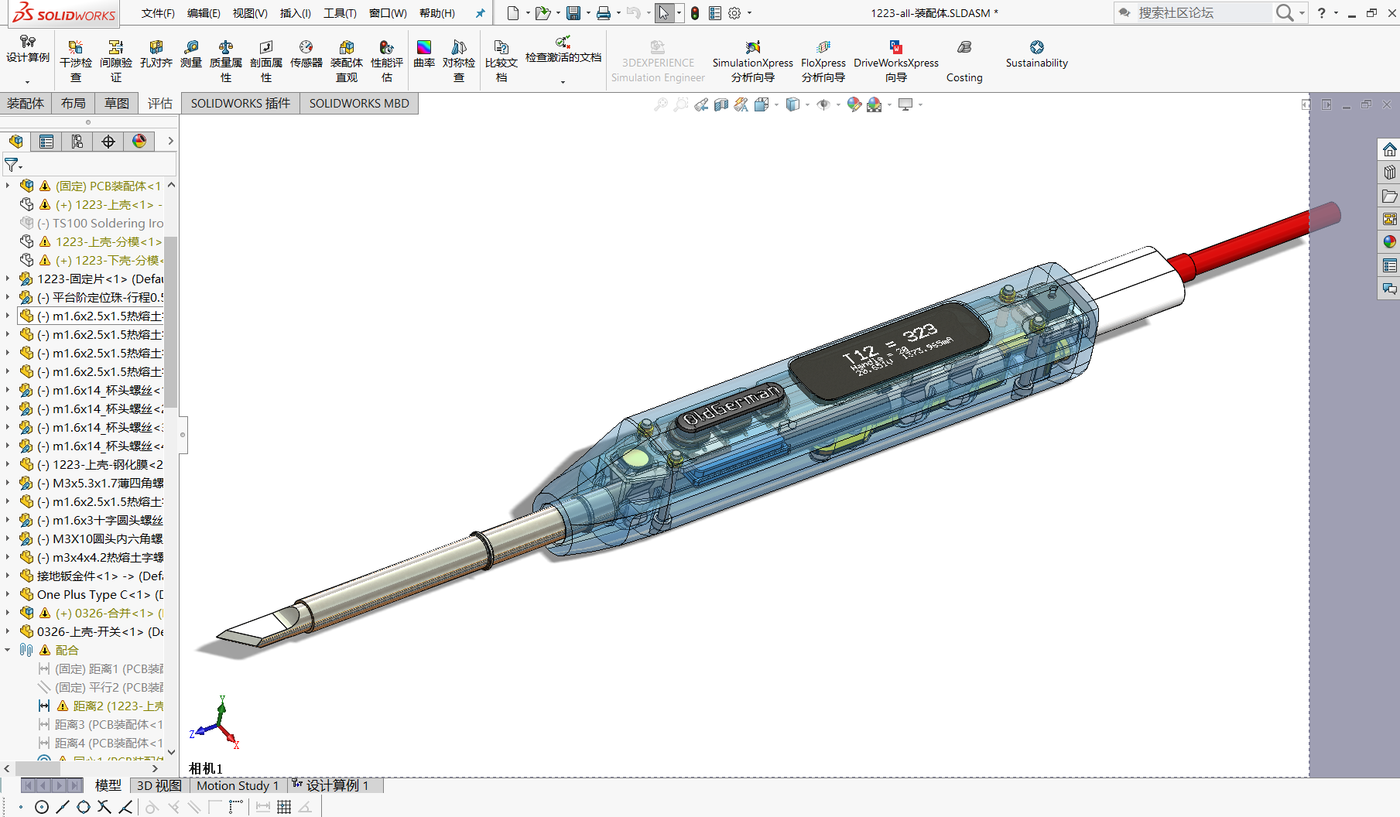
Hardware/SW_Project/20210327_IMG/sw外壳设计(0).png
