oldgerman/ODGIRON/Hardware/SW_Project/20210327_IMG/sw外壳设计(1).png

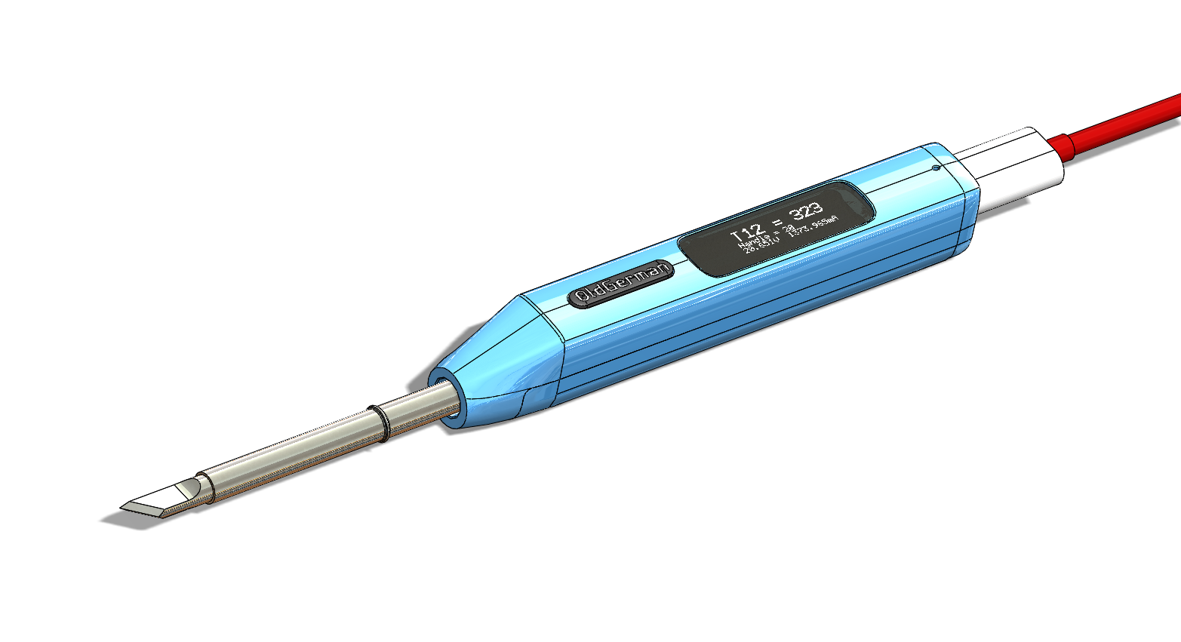
Hardware/SW_Project/20210327_IMG/sw外壳设计(1).png
