oldgerman/ODGIRON/Hardware/SW_Project/20210327_IMG/外壳打印件.png

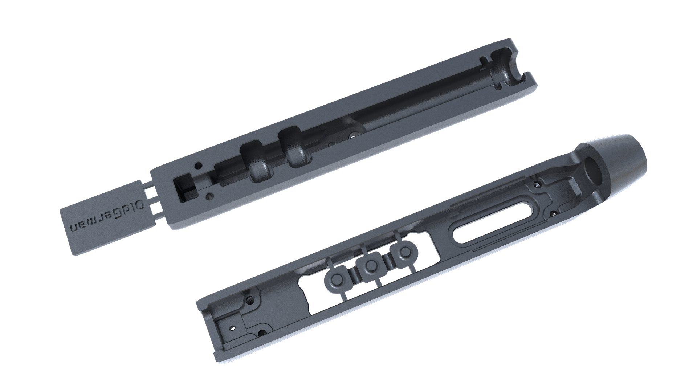
Hardware/SW_Project/20210327_IMG/外壳打印件.png
