oldgerman/ODGIRON/Hardware/SW_Project/20210510_IMG/20210510173526.png

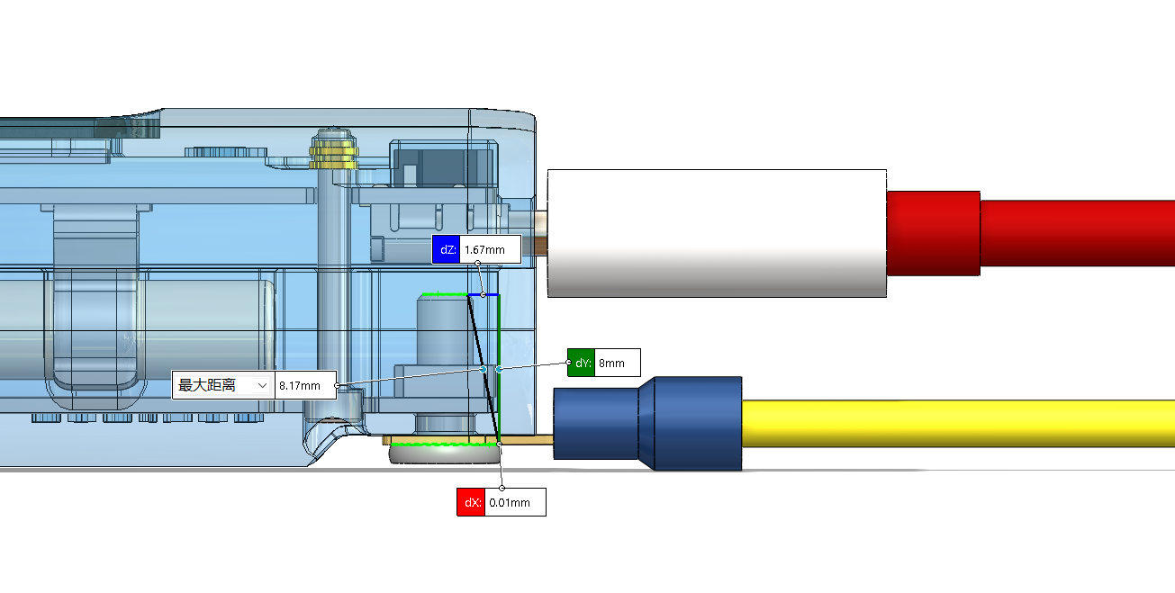
Hardware/SW_Project/20210510_IMG/20210510173526.png
