oldgerman/ODGIRON/Hardware/SW_Project/20210510_SW/3.2mm开口冷压端子.PNG

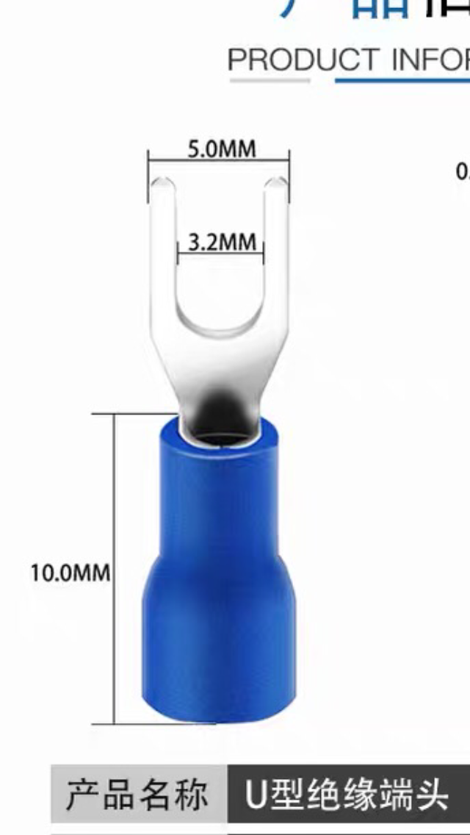
Hardware/SW_Project/20210510_SW/3.2mm开口冷压端子.PNG
