oldgerman/ODGIRON/Hardware/SW_Project/20210510_SW/F4-top.png

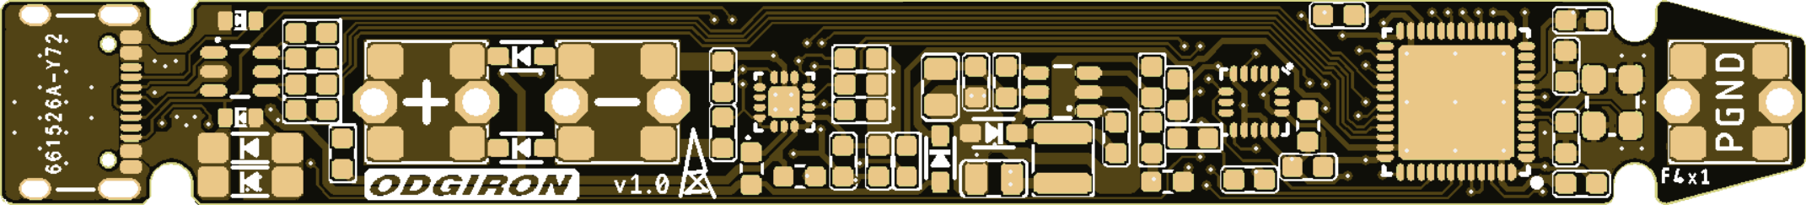
Hardware/SW_Project/20210510_SW/F4-top.png
