oldgerman/ODGIRON/Hardware/SW_Project/20210510_SW/IMG_5926(20210208-232111).JPG

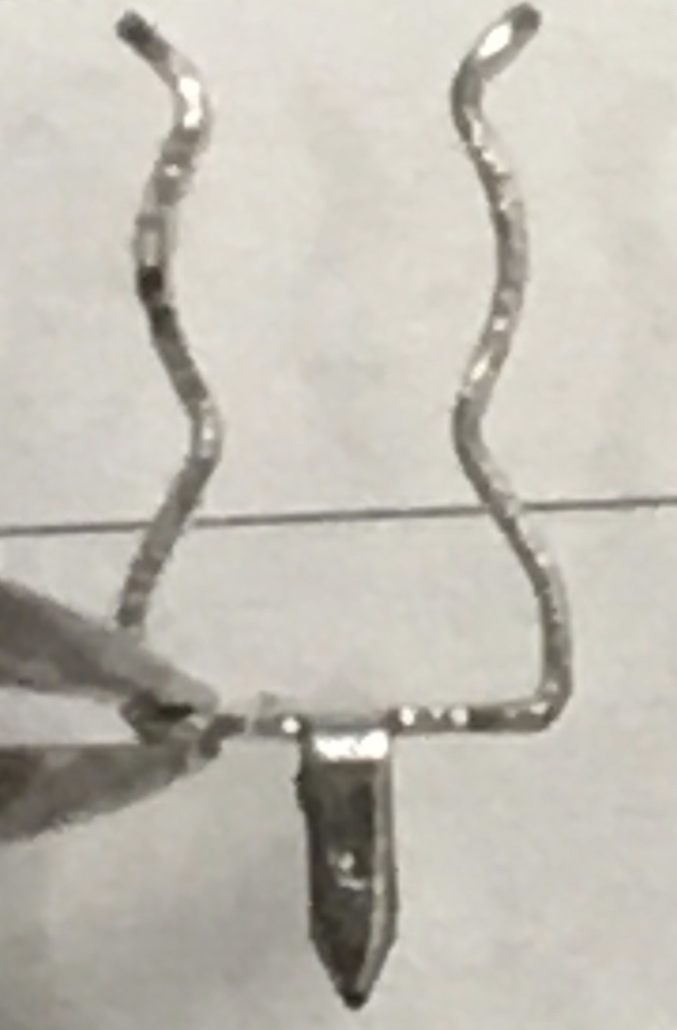
Hardware/SW_Project/20210510_SW/IMG_5926(20210208-232111).JPG
