oldgerman/ODGIRON/Hardware/SW_Project/20210510_SW/L$TA{2FFNK~[YP3U5{AH(GR.png

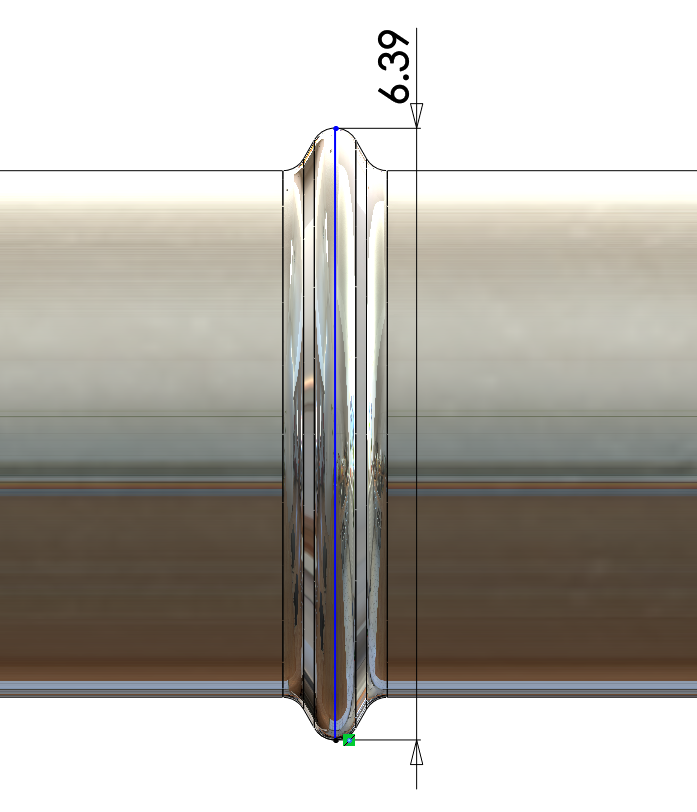
Hardware/SW_Project/20210510_SW/L$TA{2FFNK~[YP3U5{AH(GR.png
