oldgerman/ODGIRON/Hardware/SW_Project/20210510_SW/sot23-package-1.snapshot.6/SOT23.jpg

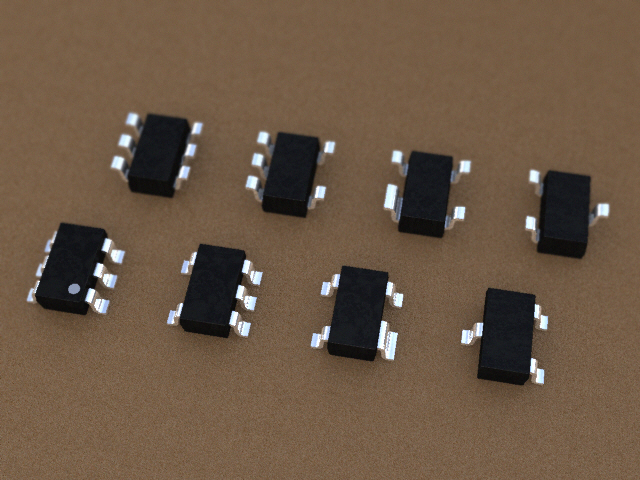
Hardware/SW_Project/20210510_SW/sot23-package-1.snapshot.6/SOT23.jpg
