oldgerman/ODGIRON/Hardware/SW_Project/20210510_SW/t12-connector/t12-connector.png

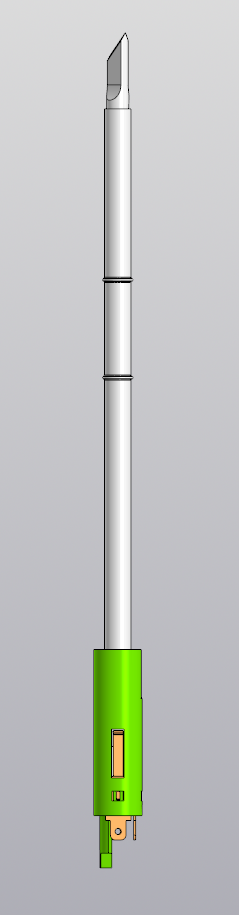
Hardware/SW_Project/20210510_SW/t12-connector/t12-connector.png
