oldgerman/ODGIRON/Hardware/SW_Project/20210510_SW/T12手柄/metcal_render.JPG

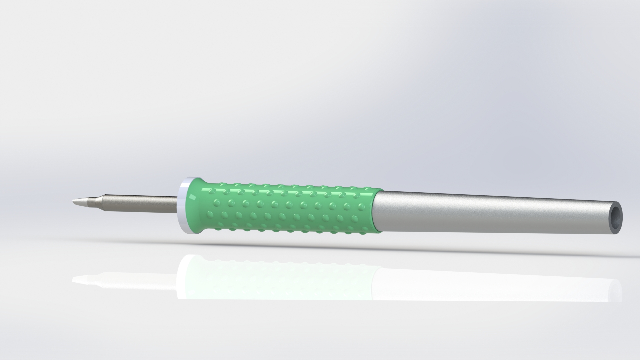
Hardware/SW_Project/20210510_SW/T12手柄/metcal_render.JPG
