oldgerman/ODGIRON/Hardware/SW_Project/20210510_SW/TS100 In Stand.jpg

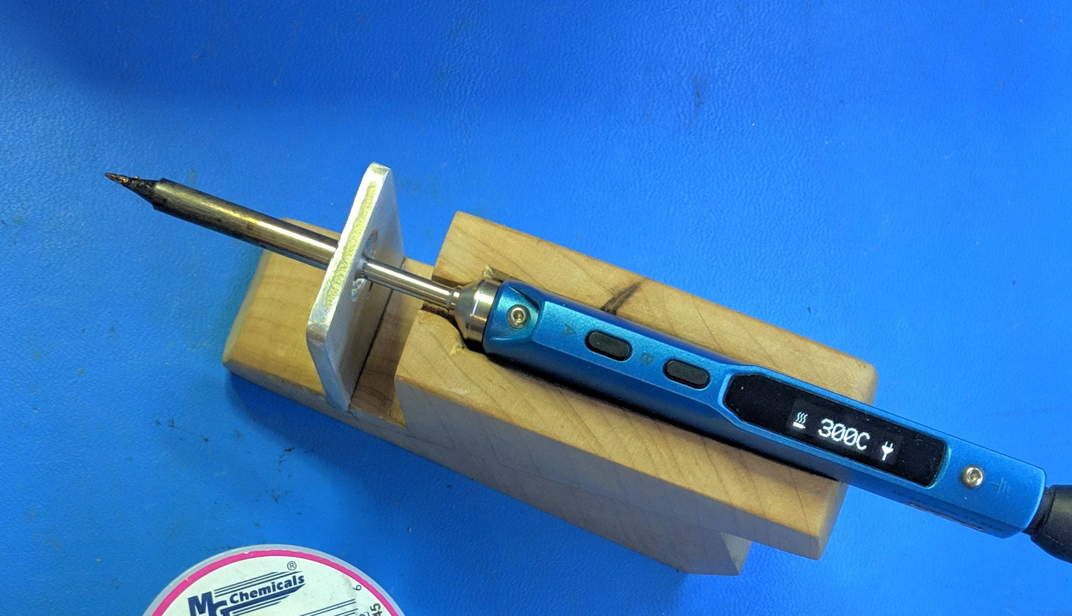
Hardware/SW_Project/20210510_SW/TS100 In Stand.jpg
