oldgerman/ODGIRON/Hardware/SW_Project/20210510_SW/小爱音响top.jpg

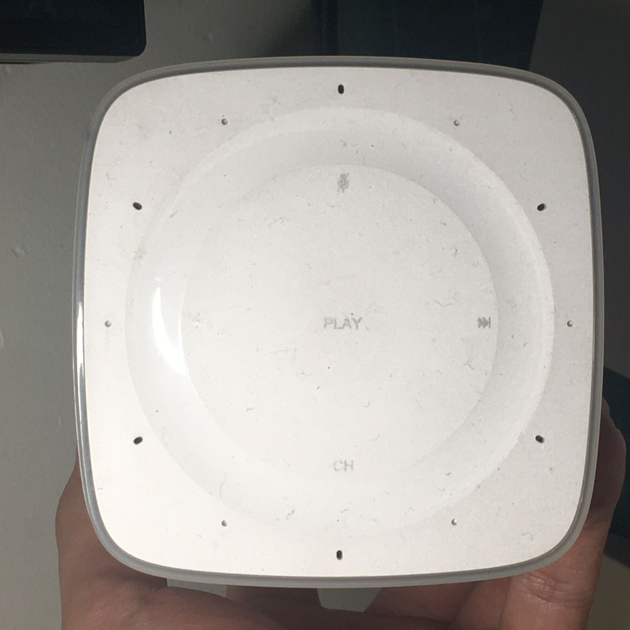
Hardware/SW_Project/20210510_SW/小爱音响top.jpg
