oldgerman/ODGIRON/Hardware/SW_Project/20210510_SW/接地钣金件/接地钣金件.PNG

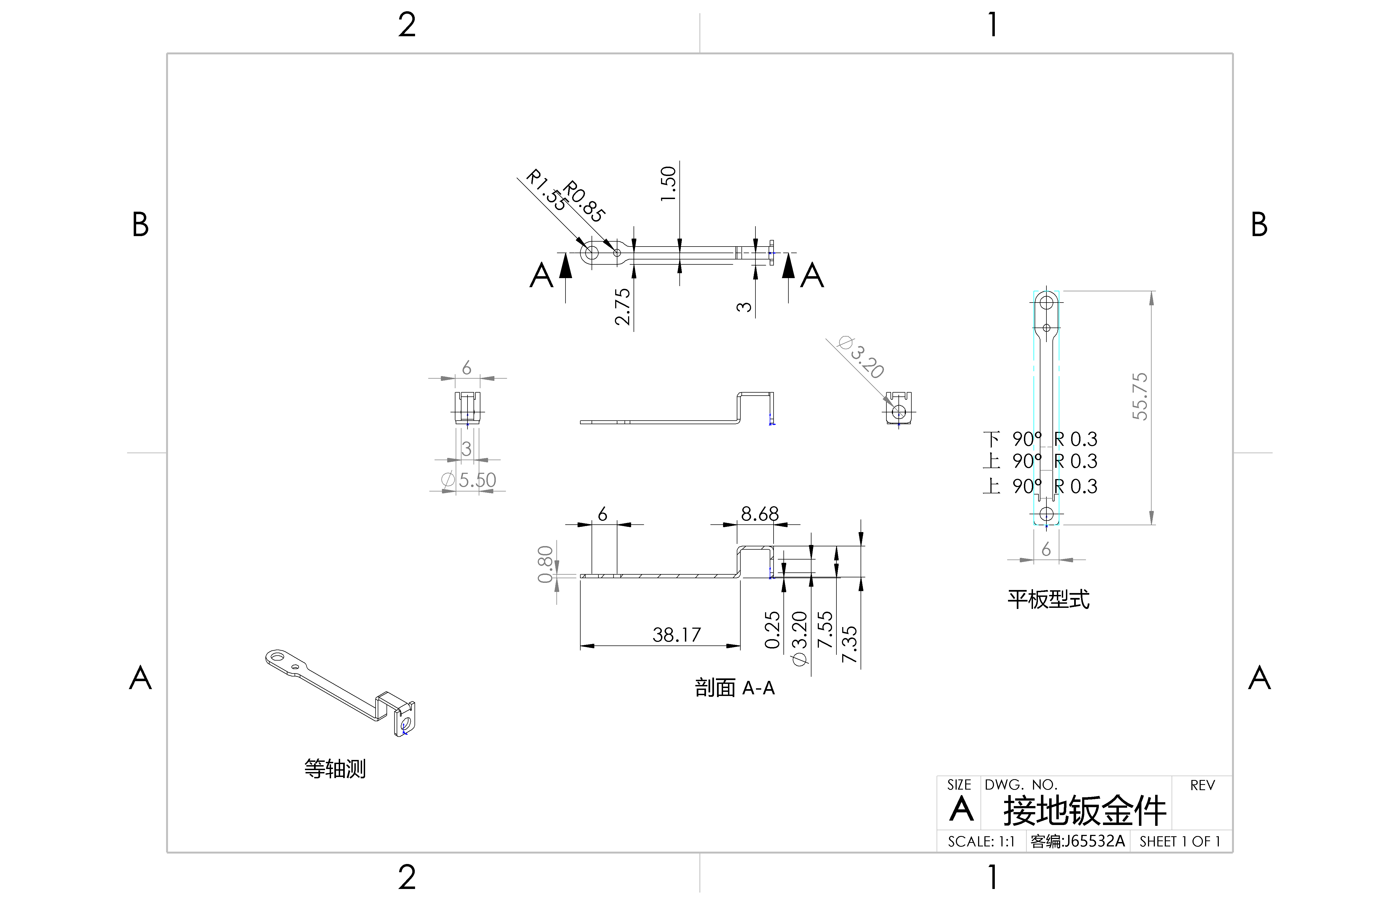
Hardware/SW_Project/20210510_SW/接地钣金件/接地钣金件.PNG
