oldgerman/ODGIRON/Hardware/SW_Project/20210603_oled面板打印/0326-OLED面板.PNG

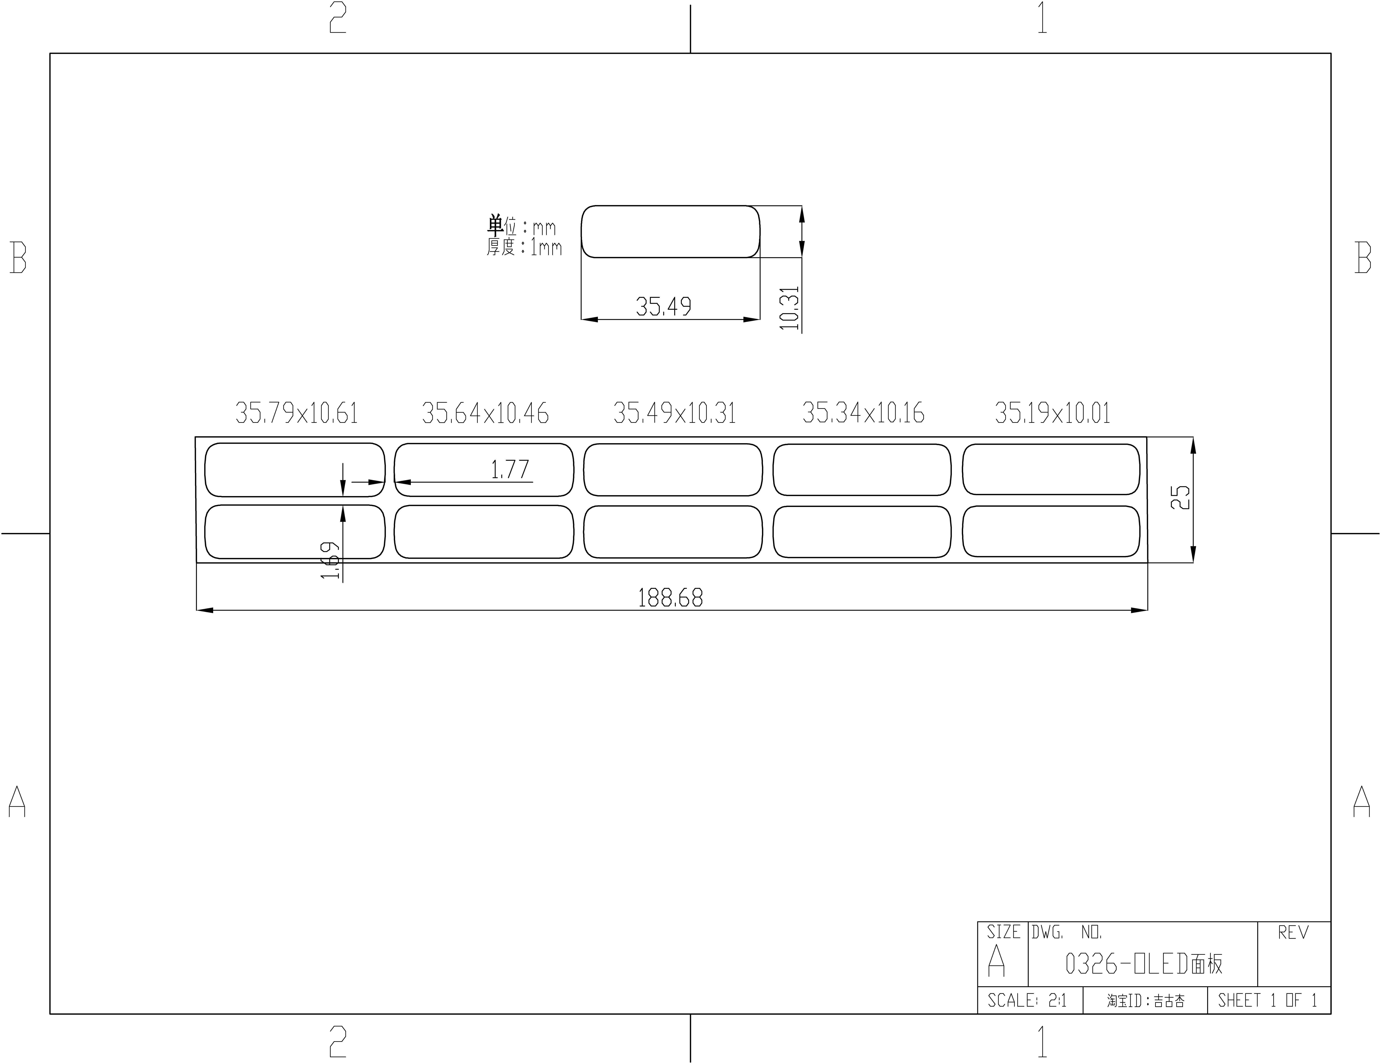
Hardware/SW_Project/20210603_oled面板打印/0326-OLED面板.PNG
