oldgerman/ODGIRON/Hardware/SW_Project/20210603_oled面板打印/20210521113149.png

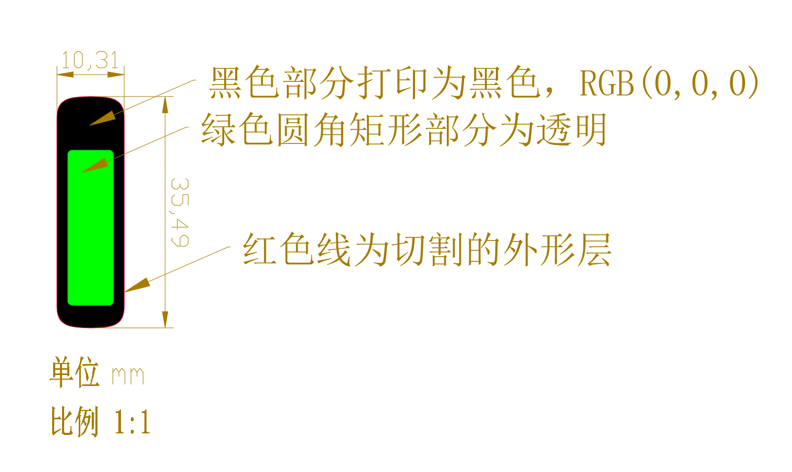
Hardware/SW_Project/20210603_oled面板打印/20210521113149.png
