oldgerman/ODGIRON/Hardware/SW_Project/20210603_oled面板打印/【预览图】0.87寸oled亚克力面板2021-0603_格式CAD2004.png

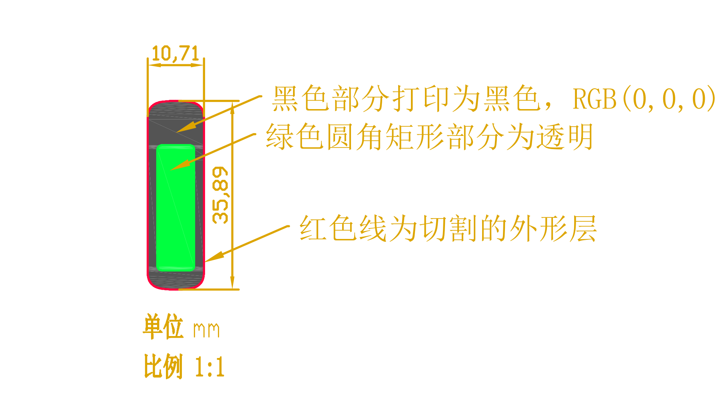
Hardware/SW_Project/20210603_oled面板打印/【预览图】0.87寸oled亚克力面板2021-0603_格式CAD2004.png
