oldgerman/ODGIRON/Hardware/SW_Project/JLC面板打印样品/0CF67CB2B0880813CF196EE4810138E0_439.png

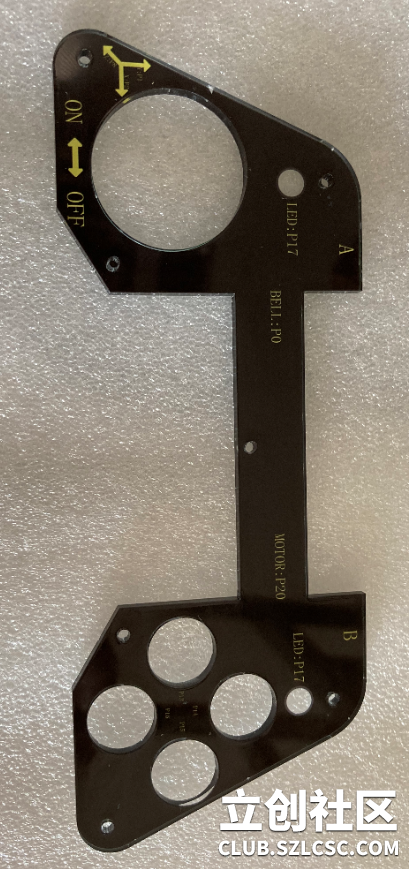
Hardware/SW_Project/JLC面板打印样品/0CF67CB2B0880813CF196EE4810138E0_439.png
