oldgerman/ODGIRON/Hardware/SW_Project/JLC面板打印样品/3F98FA868D77F6DFA7CE6694525DE23E_55.png

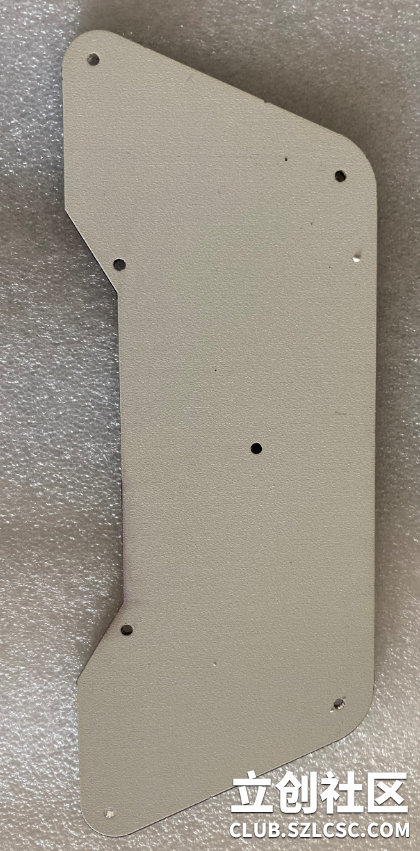
Hardware/SW_Project/JLC面板打印样品/3F98FA868D77F6DFA7CE6694525DE23E_55.png
