oldgerman/ODGIRON/Hardware/SW_Project/JLC面板打印样品/168FD855894216F193541699CF3ECB9F_777.jpg

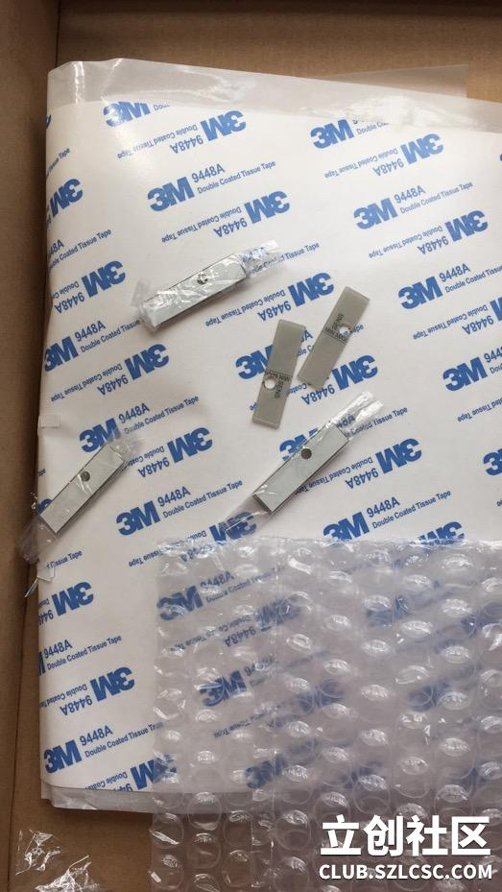
Hardware/SW_Project/JLC面板打印样品/168FD855894216F193541699CF3ECB9F_777.jpg
