oldgerman/ODGIRON/Hardware/SW_Project/JLC面板打印样品/235A65F7C46AE1030DCF818AE15A242C_990.png

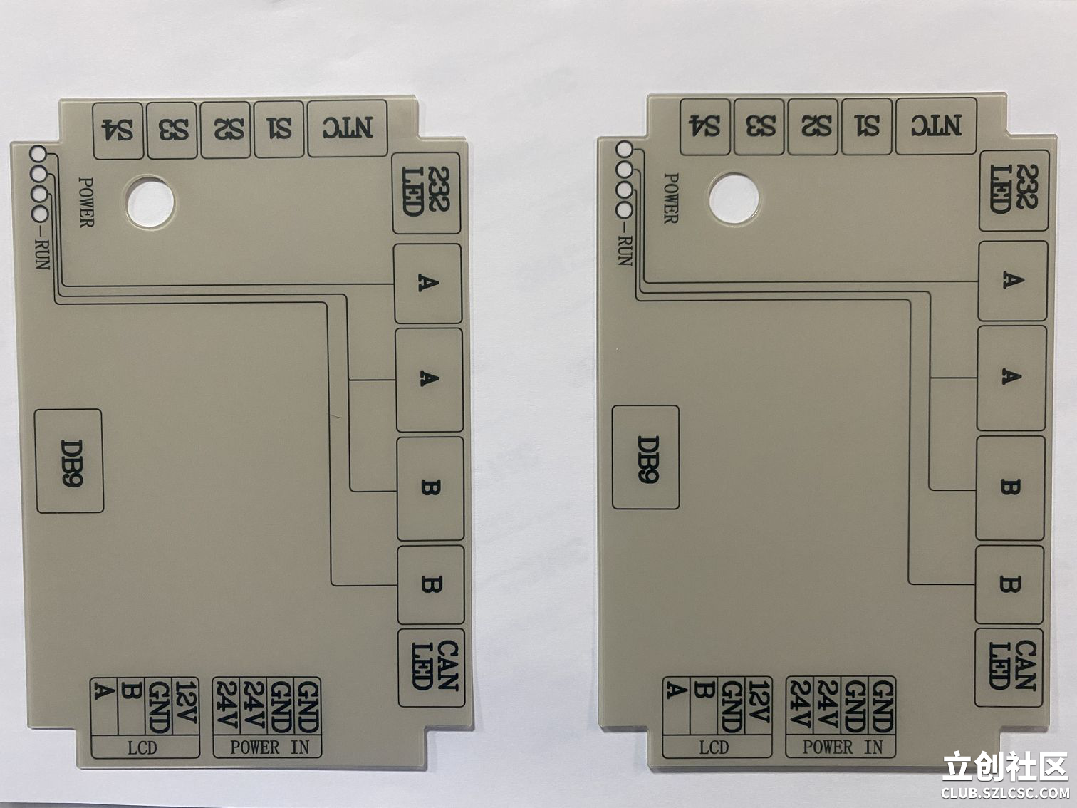
Hardware/SW_Project/JLC面板打印样品/235A65F7C46AE1030DCF818AE15A242C_990.png
