oldgerman/ODGIRON/Hardware/SW_Project/JLC面板打印样品/247D484E4DA9F03EC45206B24424A909_0.jpg

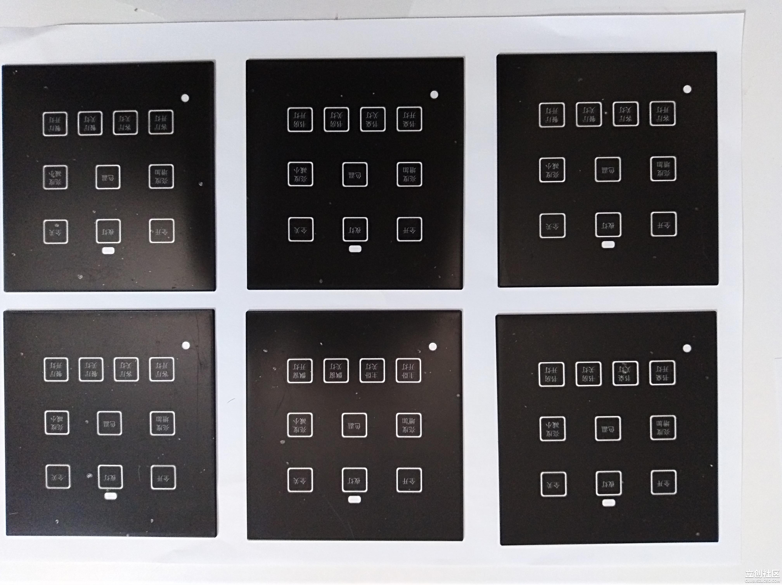
Hardware/SW_Project/JLC面板打印样品/247D484E4DA9F03EC45206B24424A909_0.jpg
