oldgerman/ODGIRON/Hardware/SW_Project/JLC面板打印样品/9695D6186E49CB986F8A8DDC42FB5708_333.png

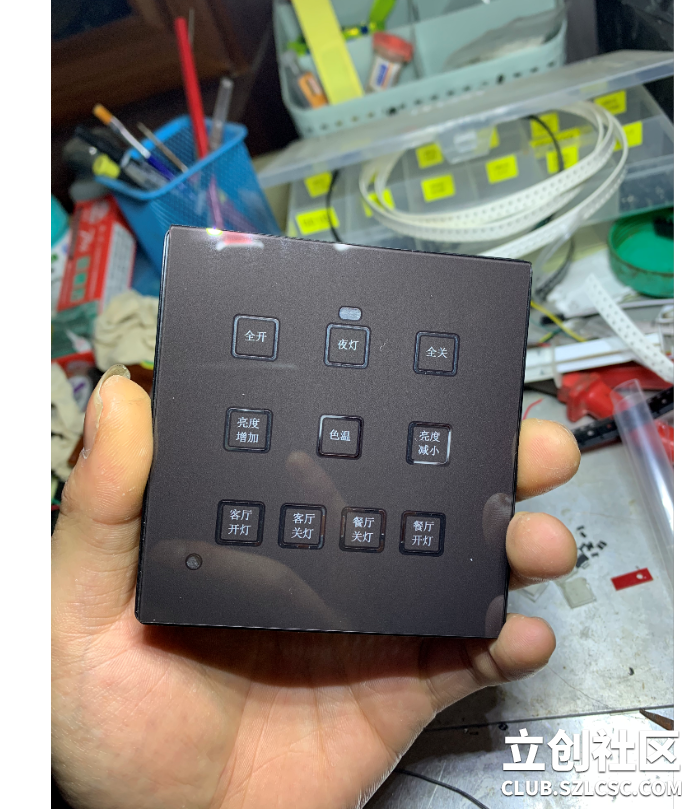
Hardware/SW_Project/JLC面板打印样品/9695D6186E49CB986F8A8DDC42FB5708_333.png
