oldgerman/ODGIRON/Hardware/SW_Project/JLC面板打印样品/A3BD4BA9C899F3394FC9232F50FECFB0_225.png

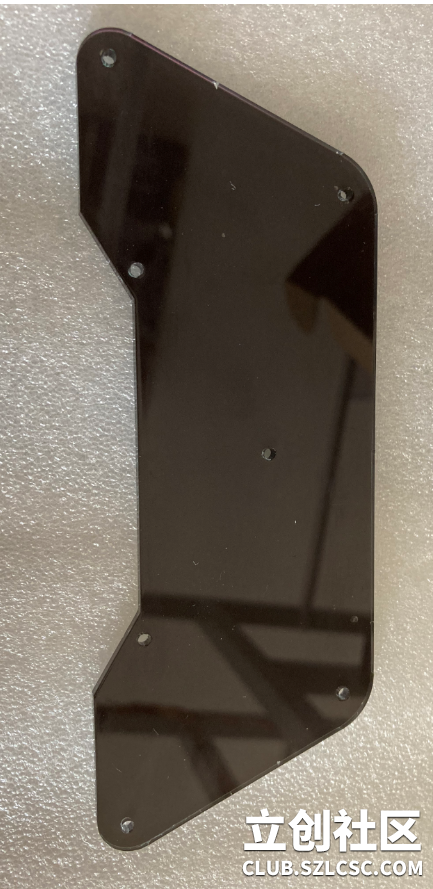
Hardware/SW_Project/JLC面板打印样品/A3BD4BA9C899F3394FC9232F50FECFB0_225.png
