oldgerman/ODGIRON/Hardware/SW_Project/JLC面板打印样品/A5B3642EE6DEADA2561679C9FECCD40E_594.jpg

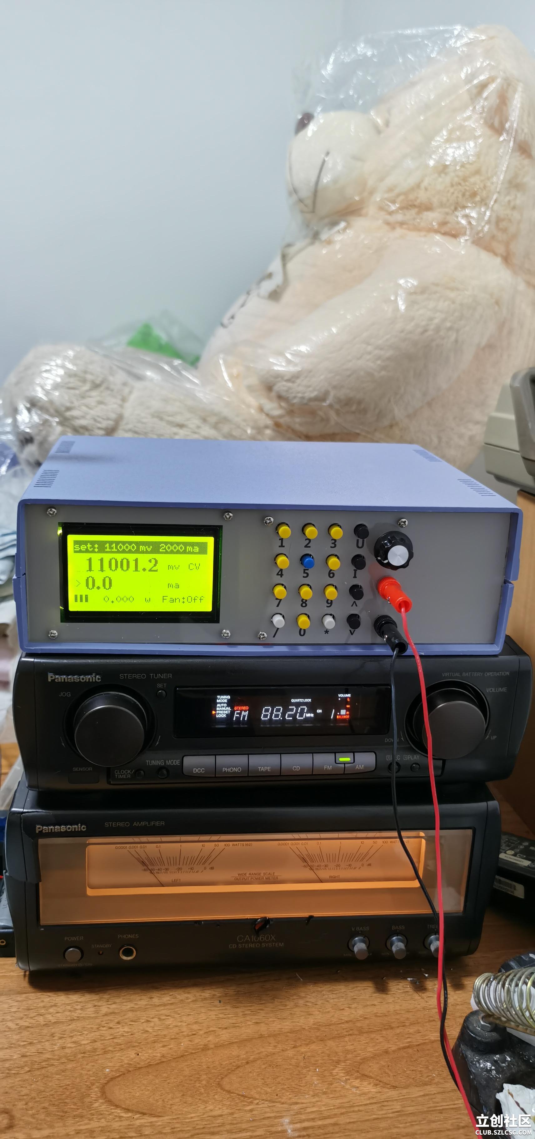
Hardware/SW_Project/JLC面板打印样品/A5B3642EE6DEADA2561679C9FECCD40E_594.jpg
