oldgerman/ODGIRON/Hardware/SW_Project/JLC面板打印样品/C7DE3F59FCAE0368EEB47A3F05C171BD_916.png

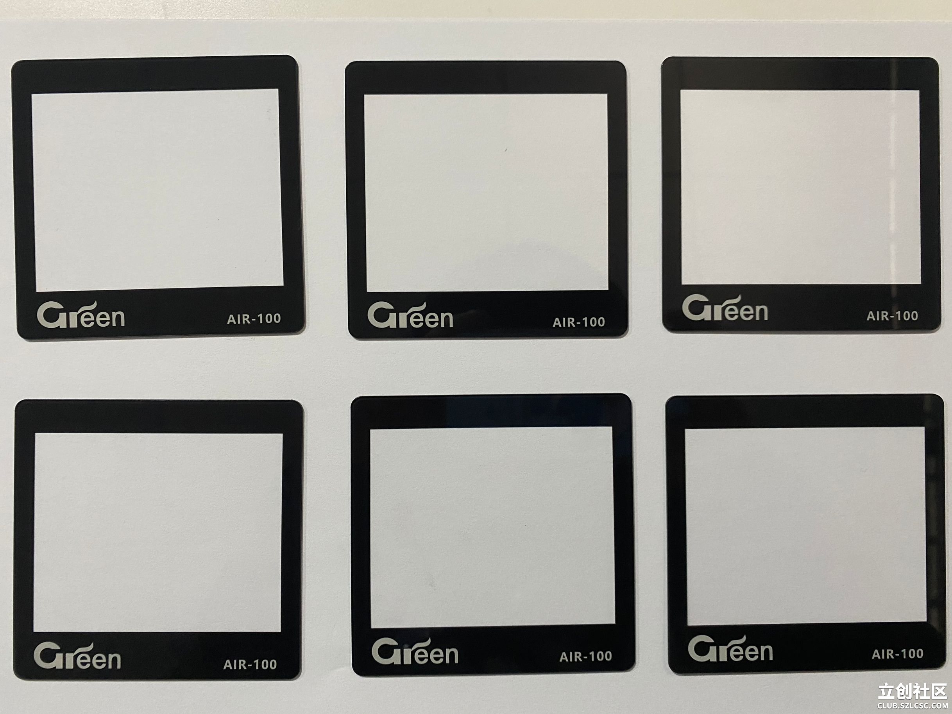
Hardware/SW_Project/JLC面板打印样品/C7DE3F59FCAE0368EEB47A3F05C171BD_916.png
