oldgerman/ODGIRON/Hardware/SW_Project/JLC面板打印样品/D07A963E9A68BCEAD238D7175B28AD41_499.png

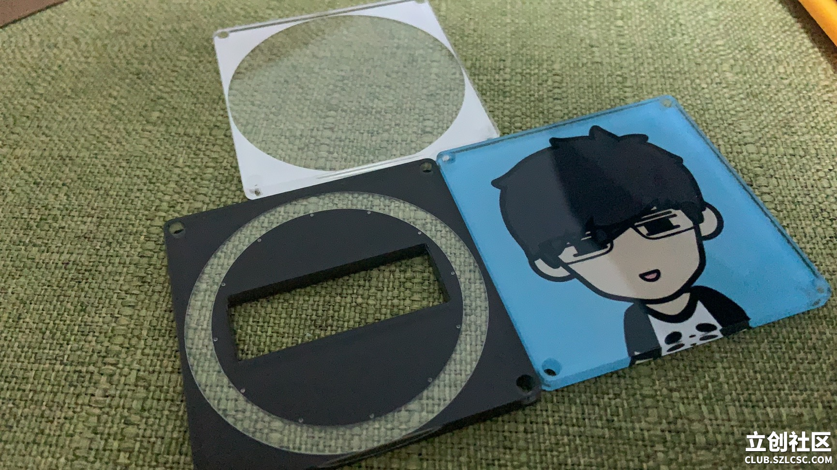
Hardware/SW_Project/JLC面板打印样品/D07A963E9A68BCEAD238D7175B28AD41_499.png
