oldgerman/ODGIRON/Hardware/SW_Project/JLC面板打印样品/E719BC51D8C3DA71B5D32801E339F150_613.png

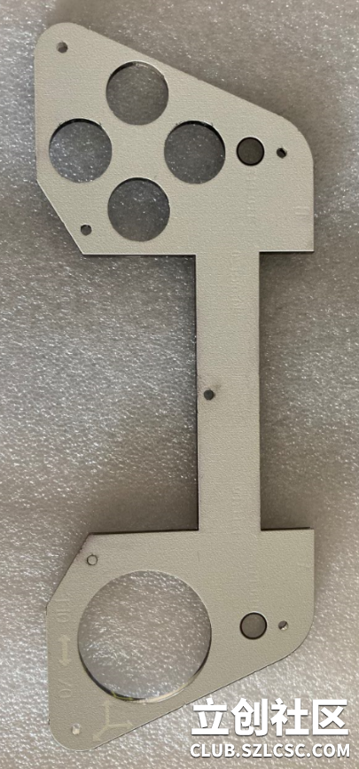
Hardware/SW_Project/JLC面板打印样品/E719BC51D8C3DA71B5D32801E339F150_613.png
