oldgerman/ODGIRON/Hardware/SW_Project/JLC面板打印样品/F439C5AFD0F09663F26402EC76357660_935.jpg

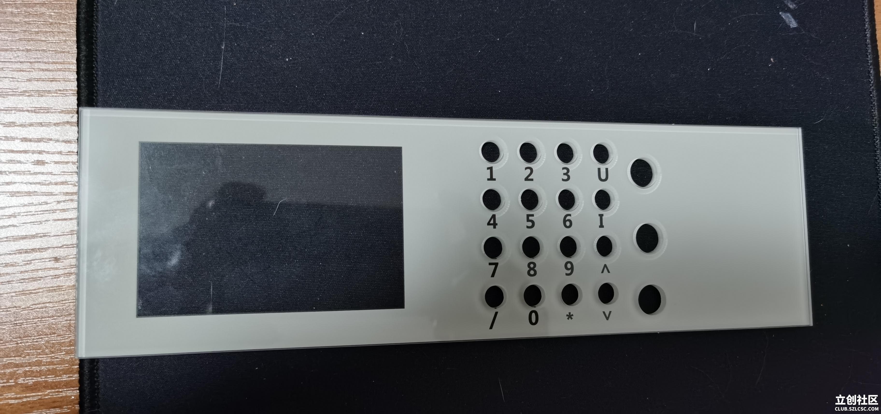
Hardware/SW_Project/JLC面板打印样品/F439C5AFD0F09663F26402EC76357660_935.jpg
