oldgerman/ODGIRON/Images/ODGIRON（2）.jpg

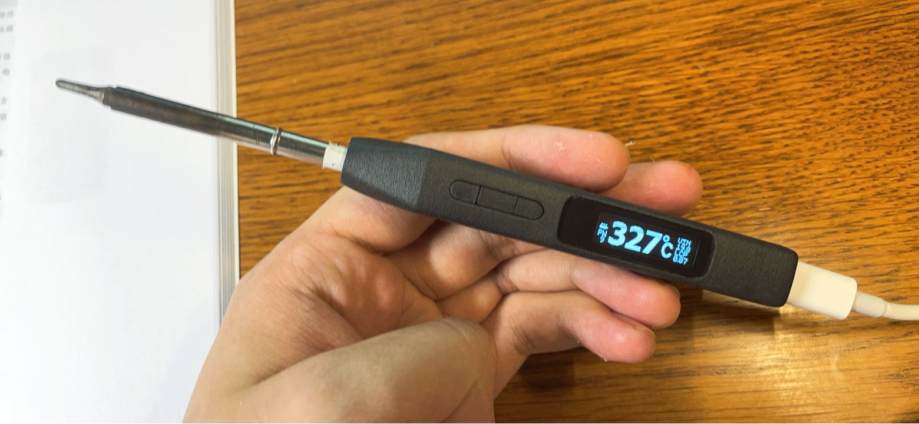
Images/ODGIRON（2）.jpg
