oldgerman/ODGIRON/UID/20210323033143.jpg

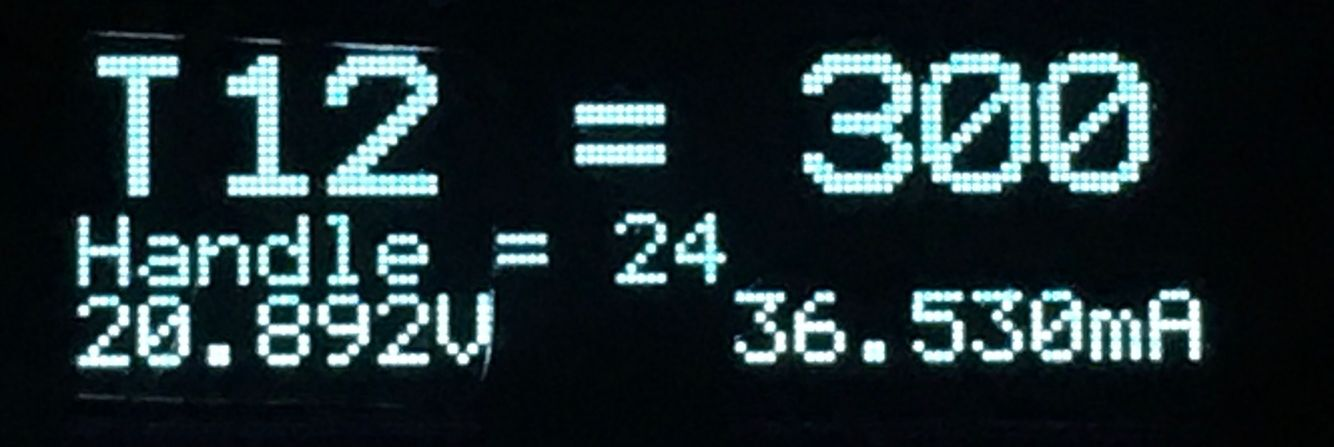
UID/20210323033143.jpg
