oldgerman/ODGIRON/UID/20210323033954.jpg

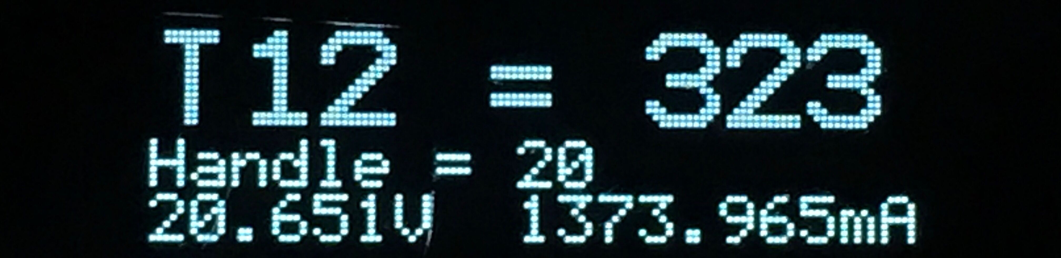
UID/20210323033954.jpg
