oldgerman/ODGIRON/UID/mini-Symbols-bmp/摄氏度符号16x32像素取模.png

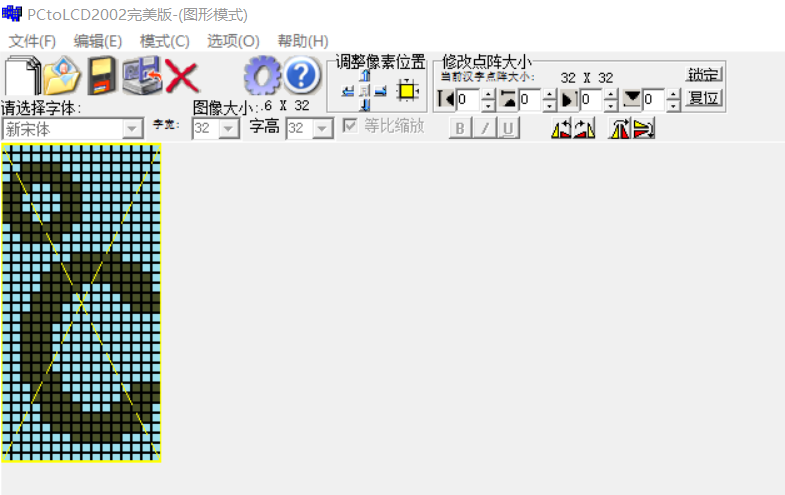
UID/mini-Symbols-bmp/摄氏度符号16x32像素取模.png
