oldgerman/ODGIRON/UID/reference/fan/62616722.jpg

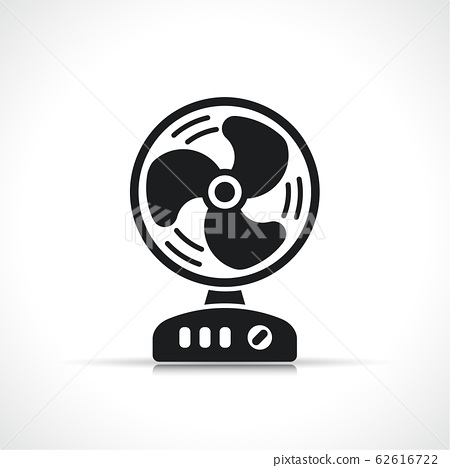
UID/reference/fan/62616722.jpg
