oldgerman/ODGIRON/UID/reference/fan/下载.png

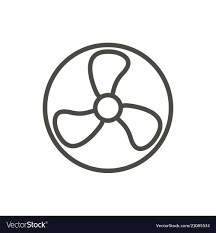
UID/reference/fan/下载.png
