oldgerman/ODGIRON/UID/reference/Gyro/1cc96fd63349962d7443296de82d2286.jpg

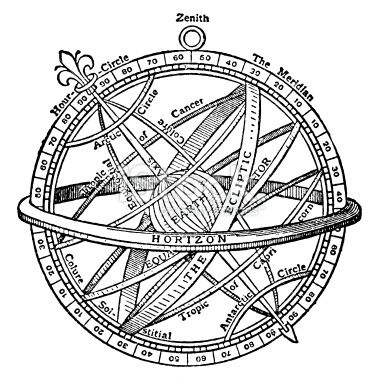
UID/reference/Gyro/1cc96fd63349962d7443296de82d2286.jpg
