oldgerman/ODGIRON/UID/reference/Gyro/aami15-85-512.webp

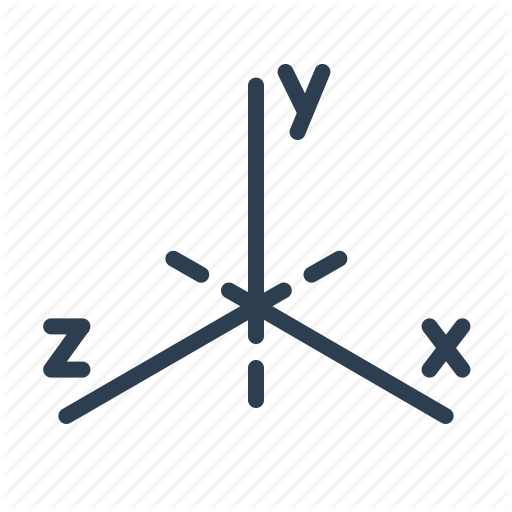
UID/reference/Gyro/aami15-85-512.webp
