oldgerman/ODGIRON/UID/reference/Gyro/accelerometer-gyroscope-compass-gps-light-260nw-710776951.webp

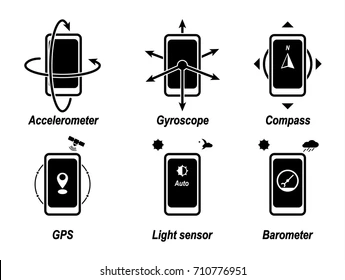
UID/reference/Gyro/accelerometer-gyroscope-compass-gps-light-260nw-710776951.webp
