oldgerman/ODGIRON/UID/reference/Gyro/Accelerometer.jpg

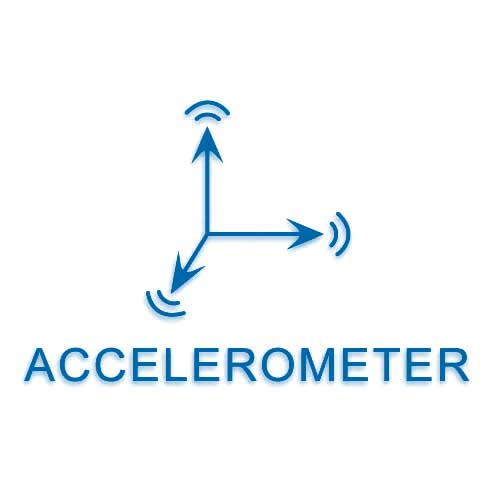
UID/reference/Gyro/Accelerometer.jpg
