oldgerman/ODGIRON/UID/reference/Gyro/directions-512.png

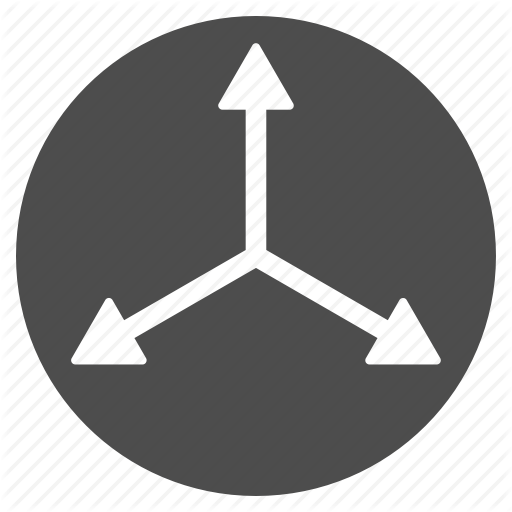
UID/reference/Gyro/directions-512.png
