oldgerman/ODGIRON/UID/reference/Gyro/emberify_sensors_in_phone.jpg

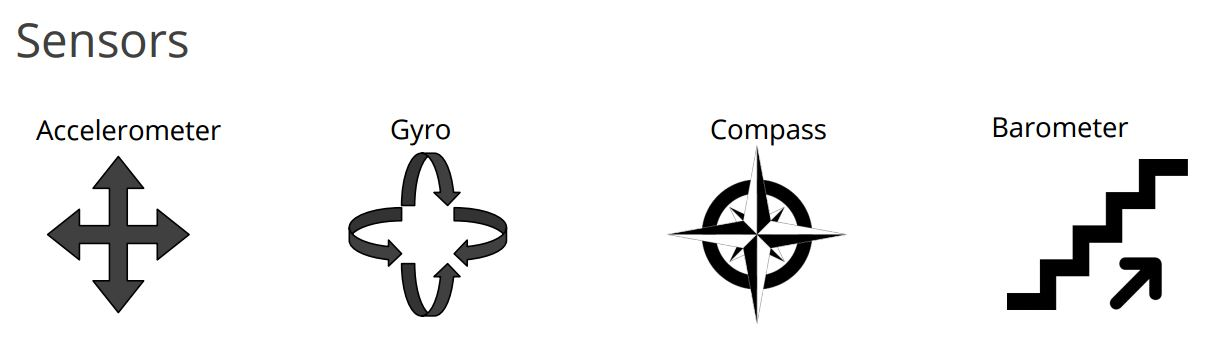
UID/reference/Gyro/emberify_sensors_in_phone.jpg
