oldgerman/ODGIRON/UID/reference/Gyro/images.png

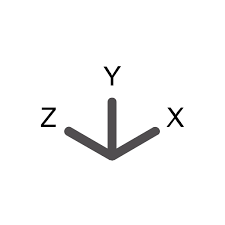
UID/reference/Gyro/images.png
