oldgerman/ODGIRON/UID/reference/Gyro/istockphoto-1158366183-1024x1024.jpg

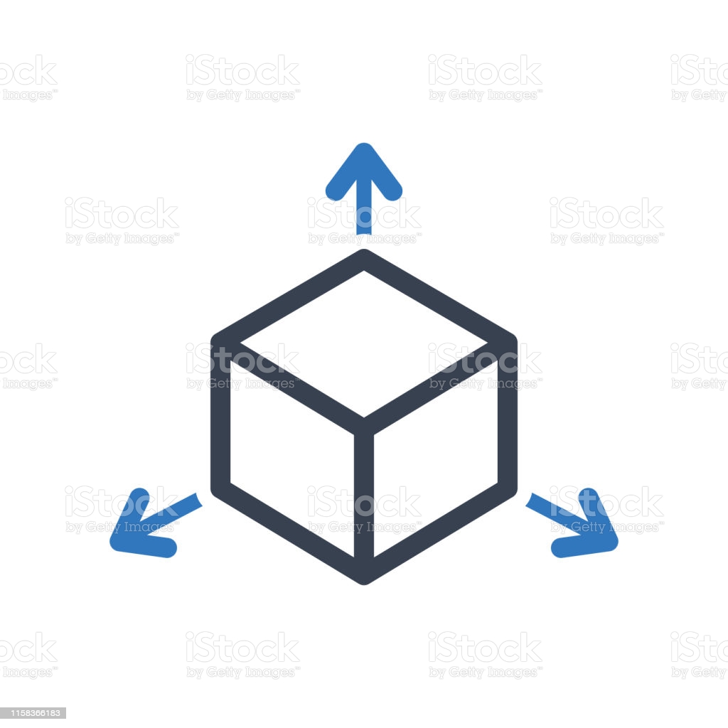
UID/reference/Gyro/istockphoto-1158366183-1024x1024.jpg
