oldgerman/ODGIRON/UID/reference/Gyro/istockphoto-1278627327-612x612.jpg

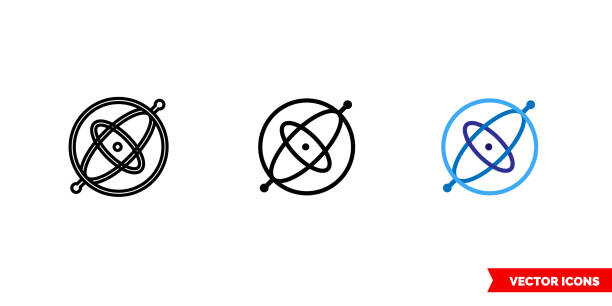
UID/reference/Gyro/istockphoto-1278627327-612x612.jpg
