oldgerman/ODGIRON/UID/reference/Gyro/istockphoto-1285678412-612x612.jpg

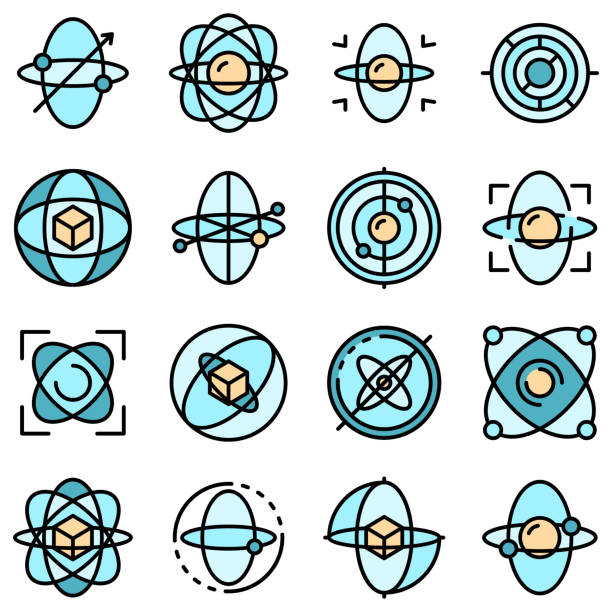
UID/reference/Gyro/istockphoto-1285678412-612x612.jpg
