oldgerman/ODGIRON/UID/主界面.png

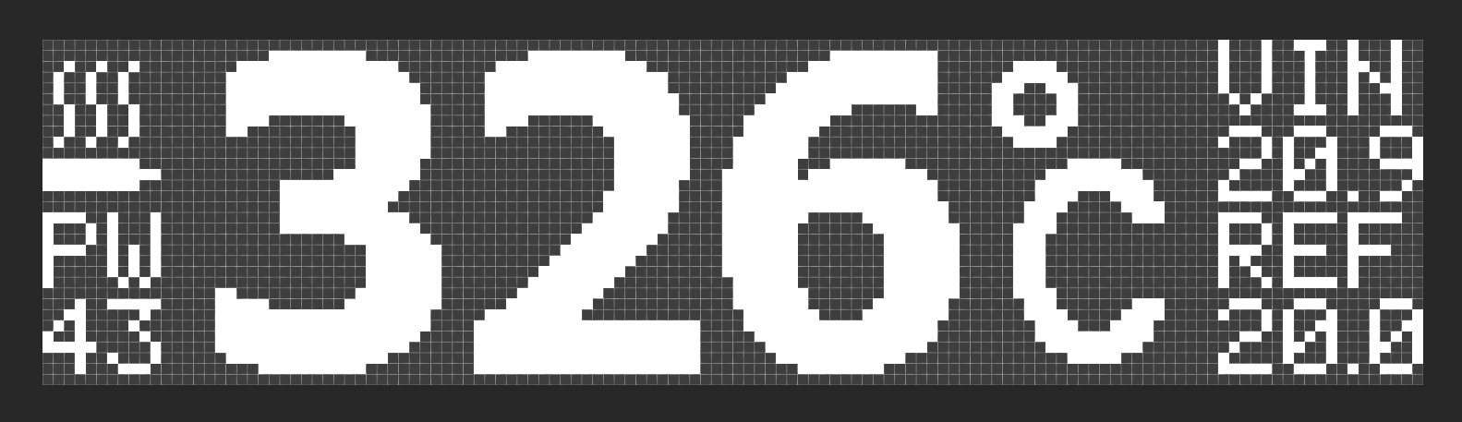
UID/主界面.png
