oldgerman/ODGIRON/UID/曲线界面.png

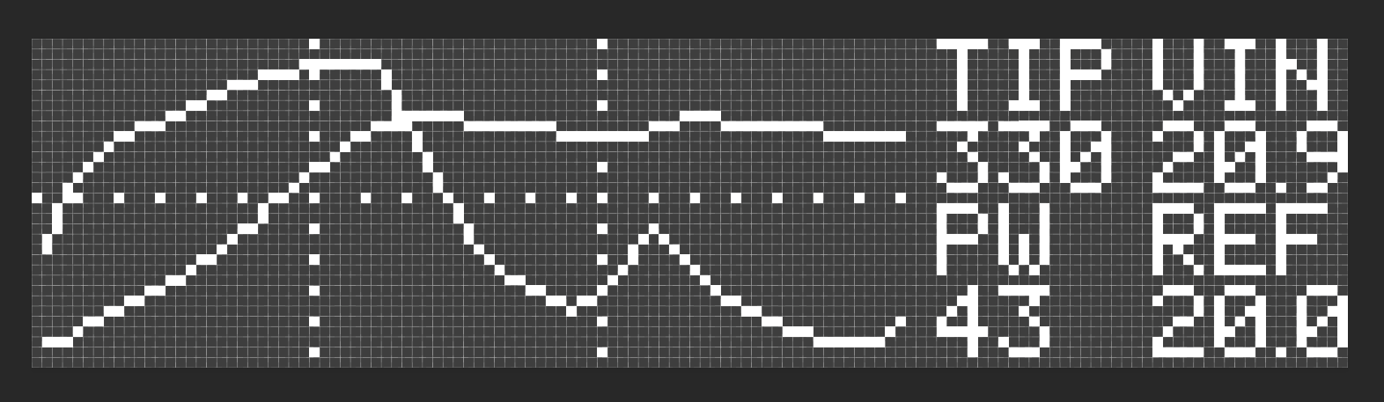
UID/曲线界面.png
