oldgerman/ODGIRON/Hardware/PCB_Project/HAKKO_191-212/孔位估算.SLDPRT

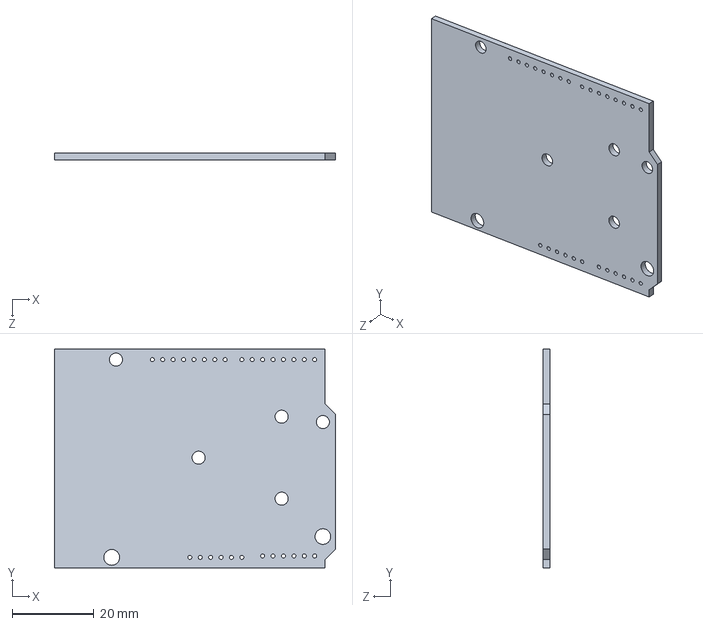
[picture p147: CAD file, 2022-12-01]
Hardware/PCB_Project/HAKKO_191-212/孔位估算.SLDPRT
68.6 x 53.3 x 1.60 mm
