oldgerman/ODGIRON/Hardware/SW_Project/20210510_3D打印件/0510-下壳_1446.STL

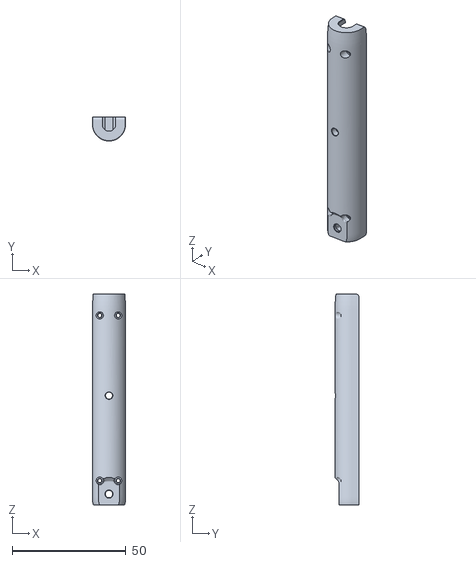
[picture p148: CAD file, 2021-08-09]
Hardware/SW_Project/20210510_3D打印件/0510-下壳_1446.STL
14.6 x 10.6 x 92.9
