oldgerman/ODGIRON/Hardware/SW_Project/20210510_SW/t12-connector/t12-connector.stp

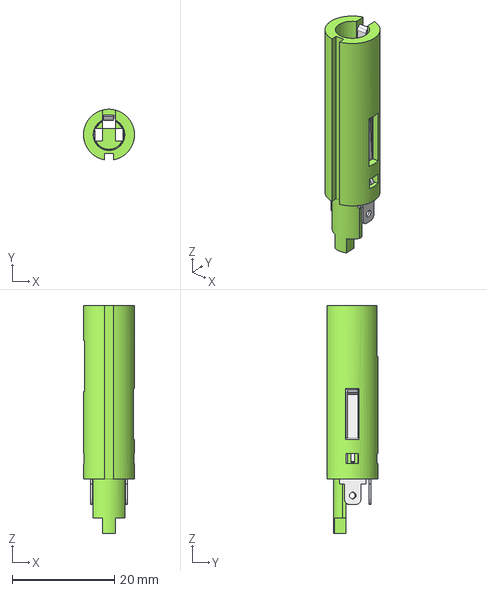
[picture p150: CAD file, 2022-12-01]
Hardware/SW_Project/20210510_SW/t12-connector/t12-connector.stp
10.00 x 9.92 x 44.7 mm
