oldgerman/ODGIRON/Hardware/SW_Project/20210510_SW/接地PCB件/接地PCB件.SLDPRT

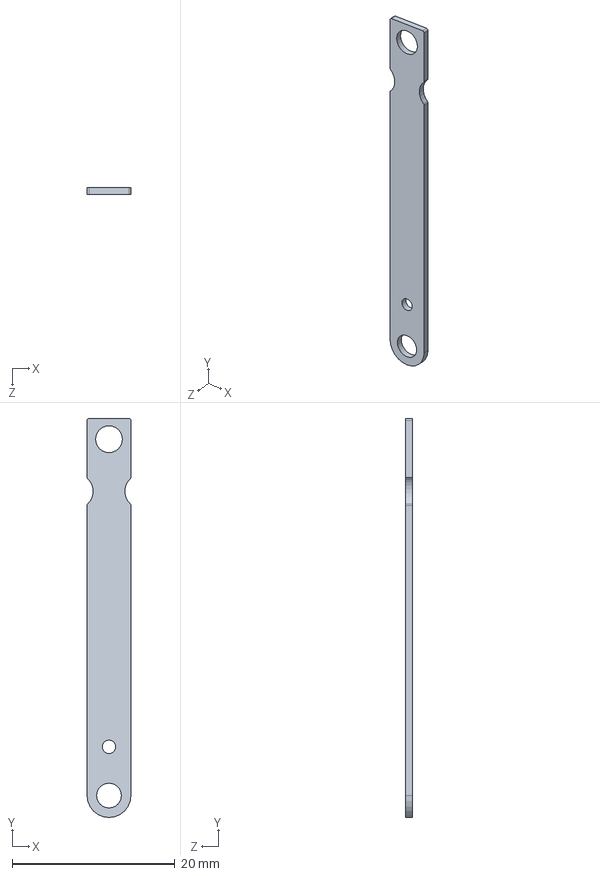
[picture p151: CAD file, 2022-12-01]
Hardware/SW_Project/20210510_SW/接地PCB件/接地PCB件.SLDPRT
5.40 x 49.1 x 0.8 mm
