oldgerman/ODGIRON/Hardware/SW_Project/20210510_SW/接地钣金件/接地钣金件魔改.SLDPRT

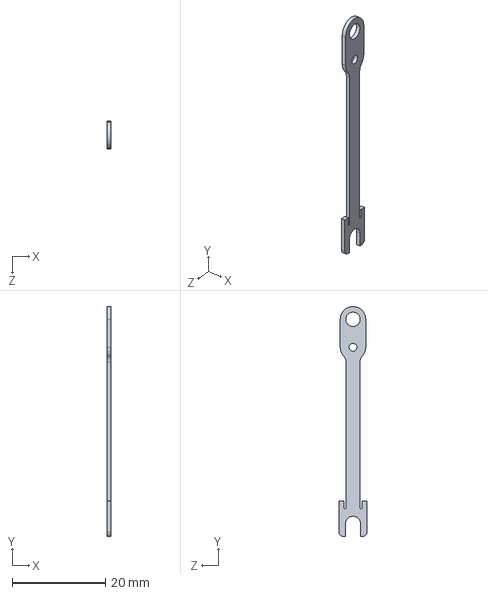
[picture p152: CAD file, 2022-12-01]
Hardware/SW_Project/20210510_SW/接地钣金件/接地钣金件魔改.SLDPRT
0.8 x 49.3 x 6.00 mm
