oldgerman/ODGIRON/Hardware/SW_Project/20210526_3D打印件/0526-固定片_QFPN48.STL

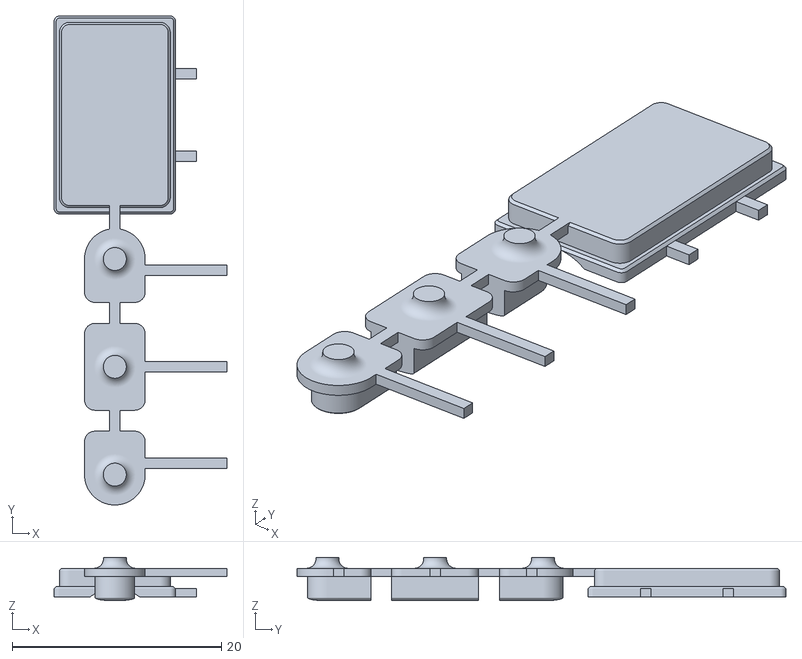
[picture p153: CAD file, 2022-12-01]
Hardware/SW_Project/20210526_3D打印件/0526-固定片_QFPN48.STL
16.5 x 46.7 x 4.15
