oldgerman/ODGIRON/Hardware/SW_Project/20210208_SW/1223-上壳-分模.STL

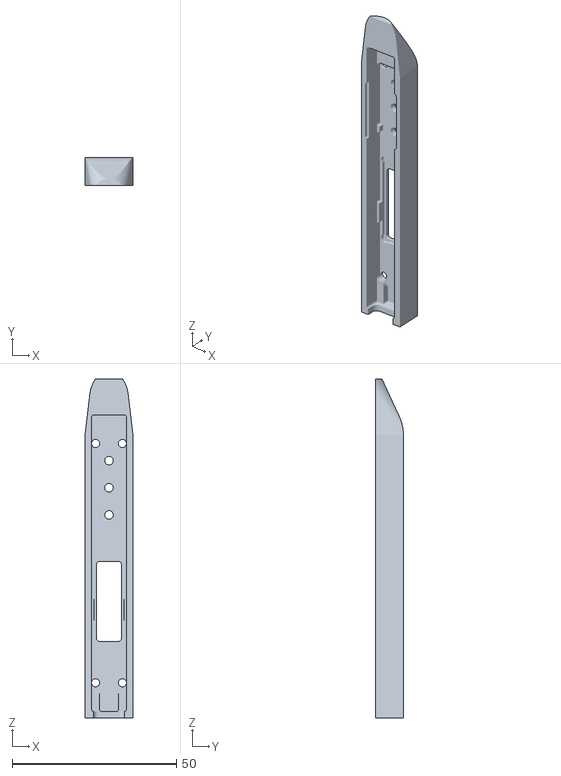
[picture p154: CAD file, 2022-12-01]
Hardware/SW_Project/20210208_SW/1223-上壳-分模.STL
14.6 x 8.53 x 103.1
