oldgerman/ODGIRON/Hardware/SW_Project/20210510_3D打印件/0510-上壳_1353.STL

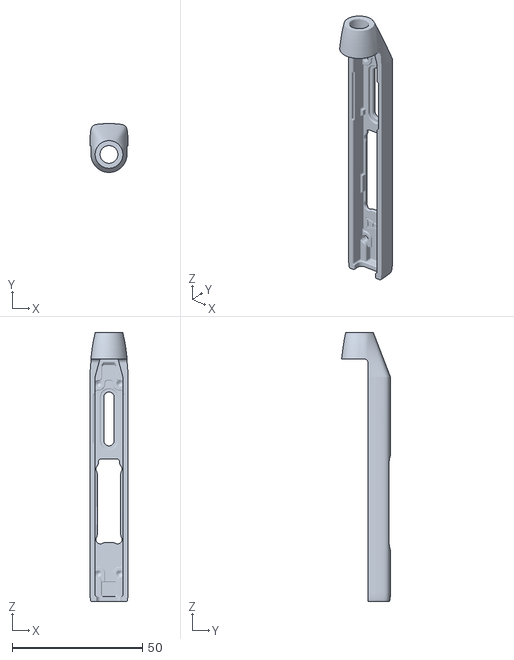
[picture p155: CAD file, 2021-08-09]
Hardware/SW_Project/20210510_3D打印件/0510-上壳_1353.STL
14.6 x 18.7 x 103.1
