oldgerman/ODGIRON/Hardware/SW_Project/20210510_SW/T12手柄/rubber_grip_bumps.SLDPRT

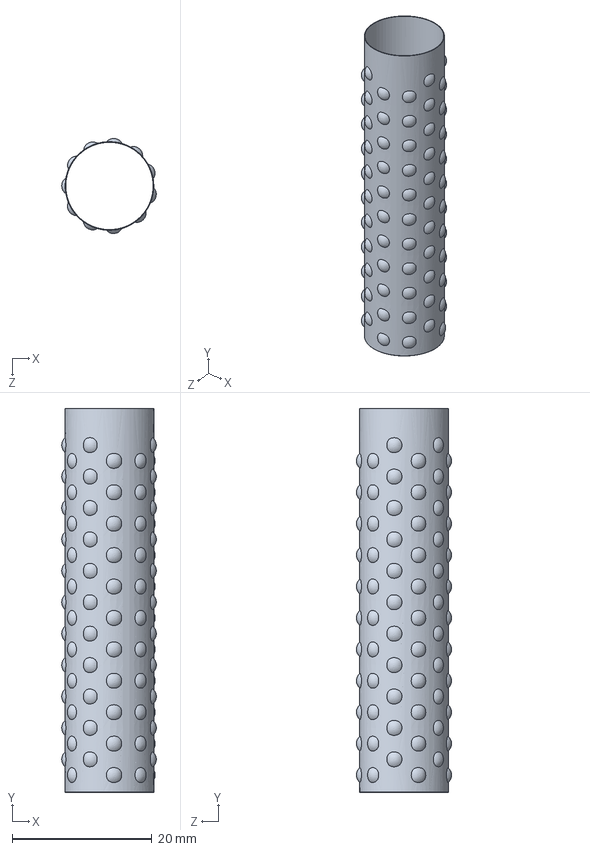
[picture p157: CAD file, 2022-12-01]
Hardware/SW_Project/20210510_SW/T12手柄/rubber_grip_bumps.SLDPRT
13.6 x 55.0 x 13.6 mm
