oldgerman/ODGIRON/Hardware/SW_Project/20210510_SW/接地PCB件/接地PCB件_0407.SLDPRT

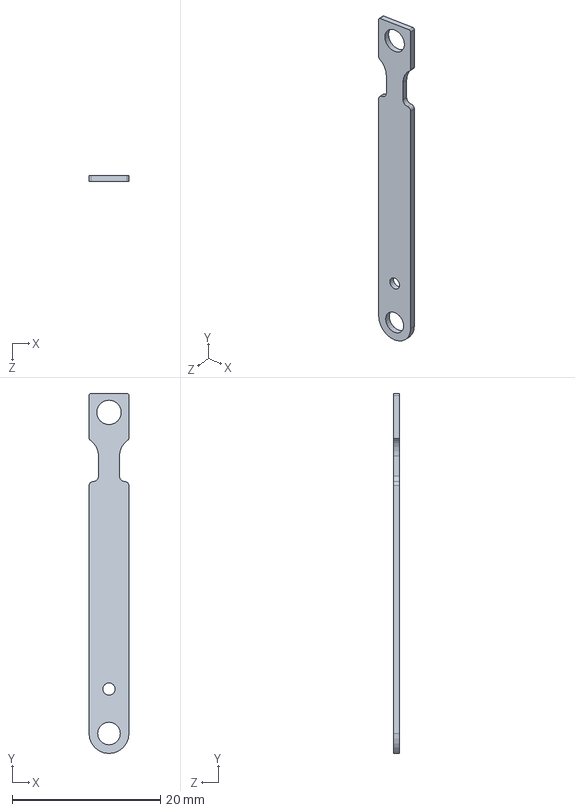
[picture p158: CAD file, 2022-12-01]
Hardware/SW_Project/20210510_SW/接地PCB件/接地PCB件_0407.SLDPRT
5.40 x 48.6 x 0.8 mm
