oldgerman/ODGIRON/Hardware/SW_Project/20210510_SW/接地钣金件/接地钣金件.STEP

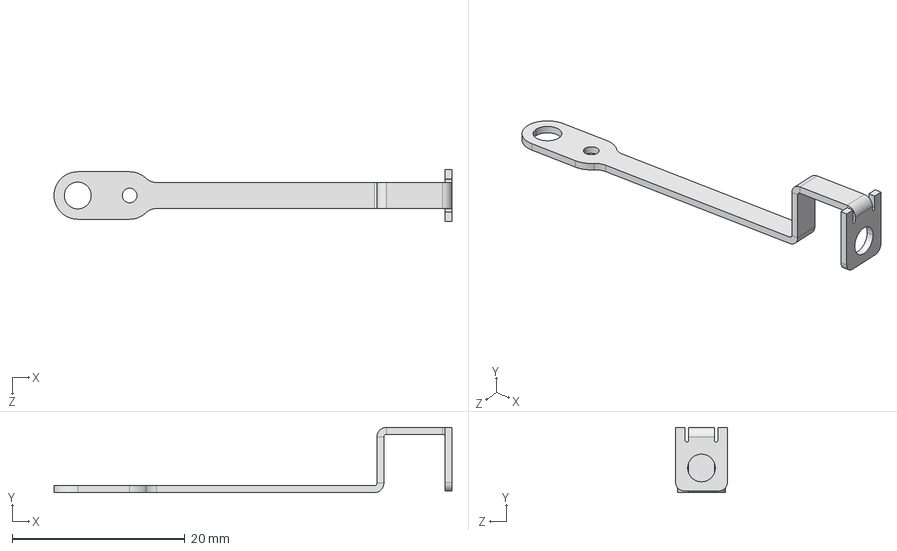
[picture p159: CAD file, 2022-12-01]
Hardware/SW_Project/20210510_SW/接地钣金件/接地钣金件.STEP
46.1 x 7.55 x 6.00 mm
