oldgerman/ODGIRON/Hardware/PCB_Project/HAKKO_191-212/LQFP-48_7x7mm_P0.5mm.SLDPRT

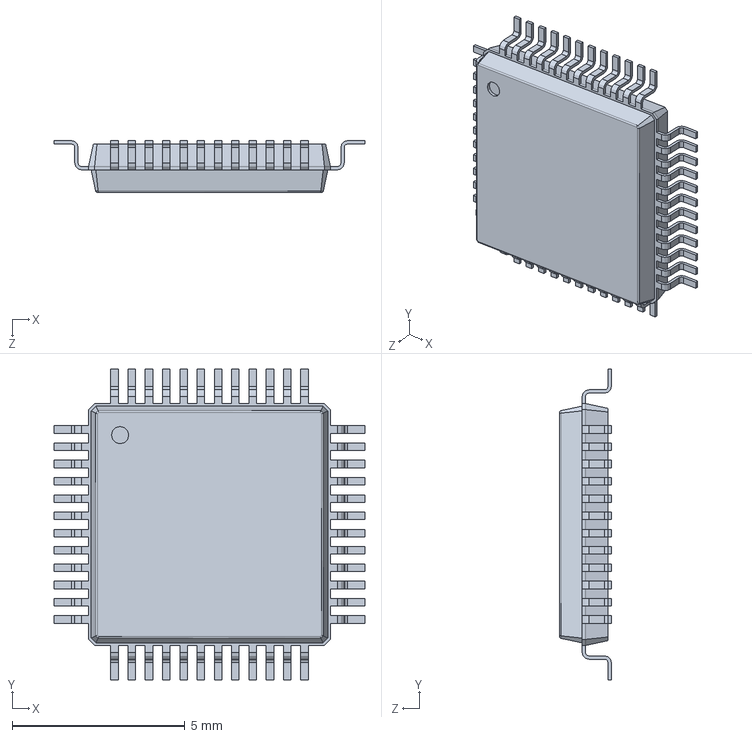
[picture p160: CAD file, 2022-12-01]
Hardware/PCB_Project/HAKKO_191-212/LQFP-48_7x7mm_P0.5mm.SLDPRT
9.00 x 9.00 x 1.50 mm
