oldgerman/ODGIRON/Hardware/SW_Project/20210208_SW/GKO.dxf

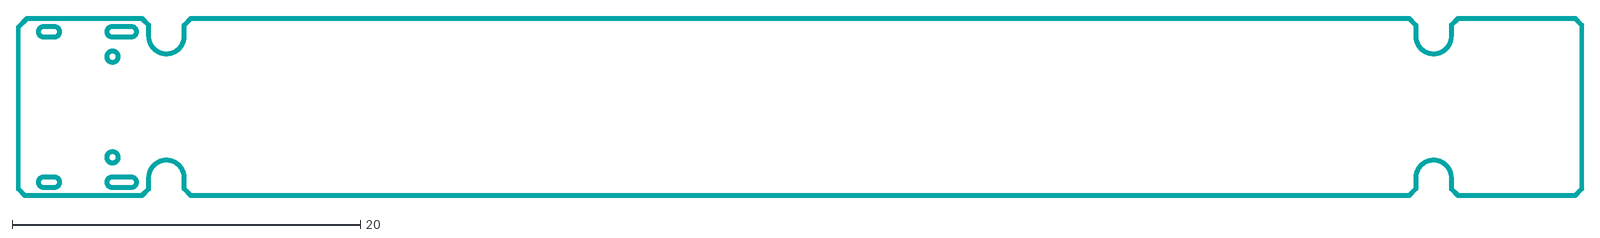
[picture p161: CAD file, 2022-12-01]
Hardware/SW_Project/20210208_SW/GKO.dxf
90.0 x 10.4
