oldgerman/ODGIRON/Hardware/SW_Project/20210510_SW/1223-上壳.SLDPRT

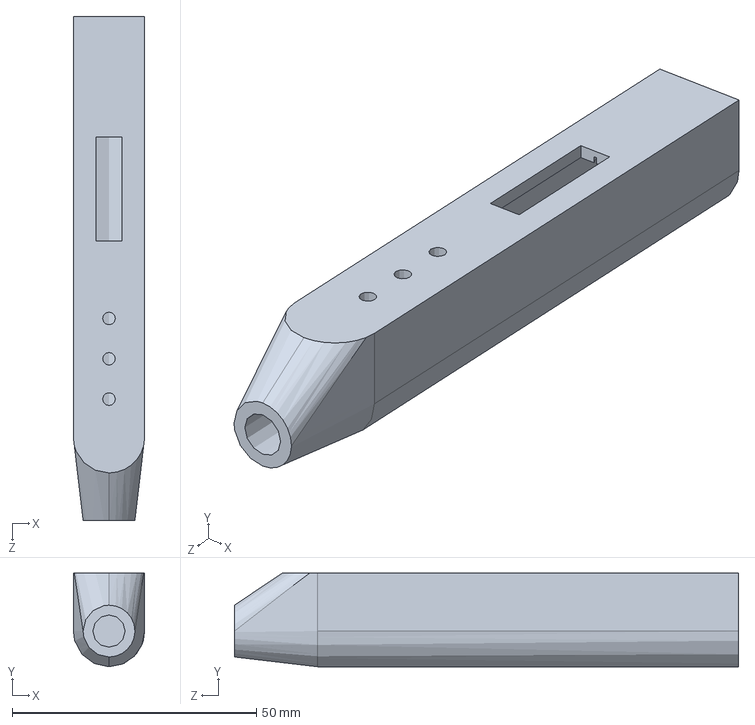
[picture p162: CAD file, 2022-12-01]
Hardware/SW_Project/20210510_SW/1223-上壳.SLDPRT
14.6 x 19.1 x 103.1 mm
