oldgerman/ODGIRON/Hardware/SW_Project/20210510_SW/sot23-package-1.snapshot.6/SOT23-3.stp

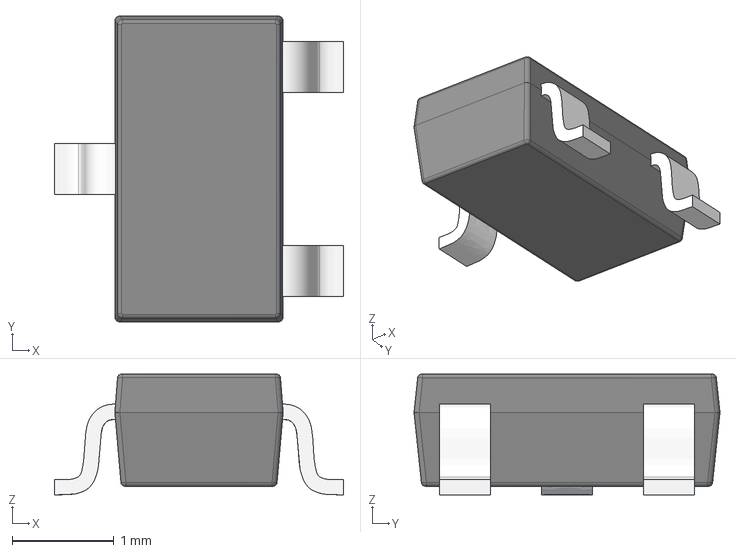
[picture p163: CAD file, 2022-12-01]
Hardware/SW_Project/20210510_SW/sot23-package-1.snapshot.6/SOT23-3.stp
2.84 x 3.00 x 1.18 mm
