oldgerman/ODGIRON/Hardware/SW_Project/20210510_SW/T12手柄/handle_bottom.SLDPRT

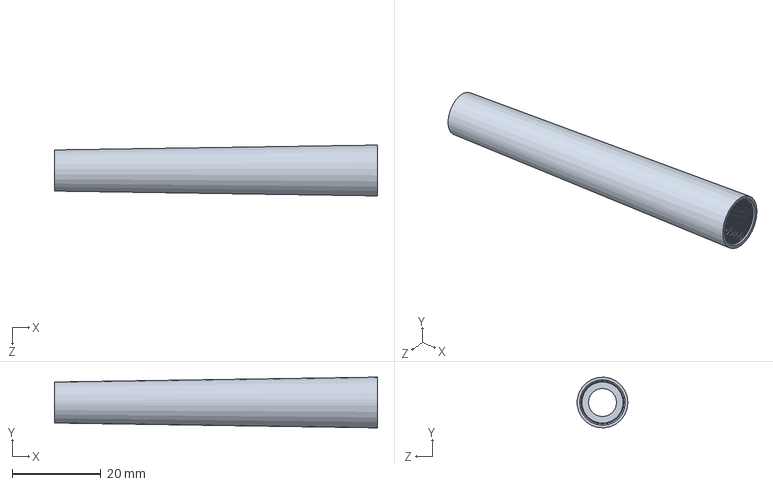
[picture p164: CAD file, 2022-12-01]
Hardware/SW_Project/20210510_SW/T12手柄/handle_bottom.SLDPRT
73.0 x 11.5 x 11.5 mm
