oldgerman/ODGIRON/Hardware/SW_Project/20210510_SW/接地钣金件/接地件.dxf

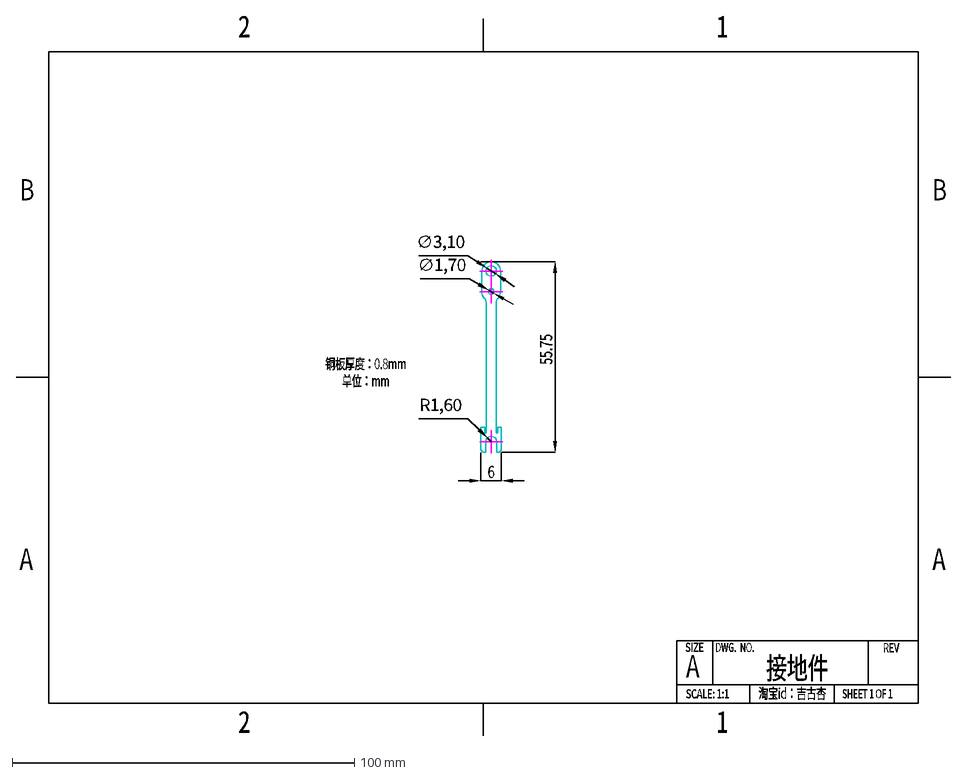
[picture p165: CAD file, 2022-12-01]
Hardware/SW_Project/20210510_SW/接地钣金件/接地件.dxf
SIZE
DWG. NO.
A
REV
SCALE: 1:1
淘宝id：吉古杏
SHEET 1 OF 1
2
1
B
接地件
55.75
6
∅3,10
∅1,70
R1,60
铜板厚度：0.8mm 单位：mm
