oldgerman/ODGIRON/Hardware/PCB_Project/HAKKO_191-212/造型1.SLDPRT

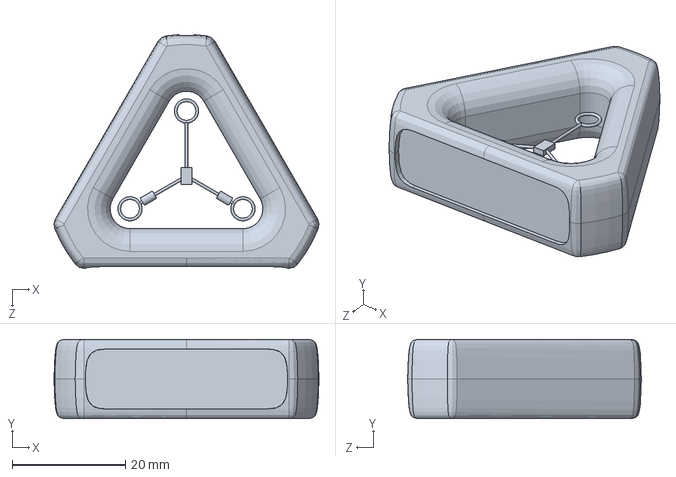
[picture p166: CAD file, 2022-12-01]
Hardware/PCB_Project/HAKKO_191-212/造型1.SLDPRT
46.7 x 14.0 x 41.2 mm
