oldgerman/ODGIRON/Hardware/SW_Project/20210510_SW/T12手柄/rubber_grip.SLDPRT

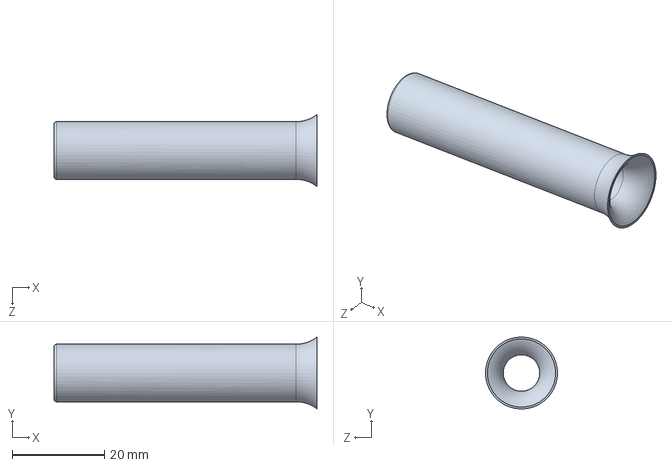
[picture p167: CAD file, 2022-12-01]
Hardware/SW_Project/20210510_SW/T12手柄/rubber_grip.SLDPRT
57.0 x 15.6 x 15.6 mm
