oldgerman/ODGIRON/Hardware/SW_Project/20210510_SW/方孔这么开.SLDPRT

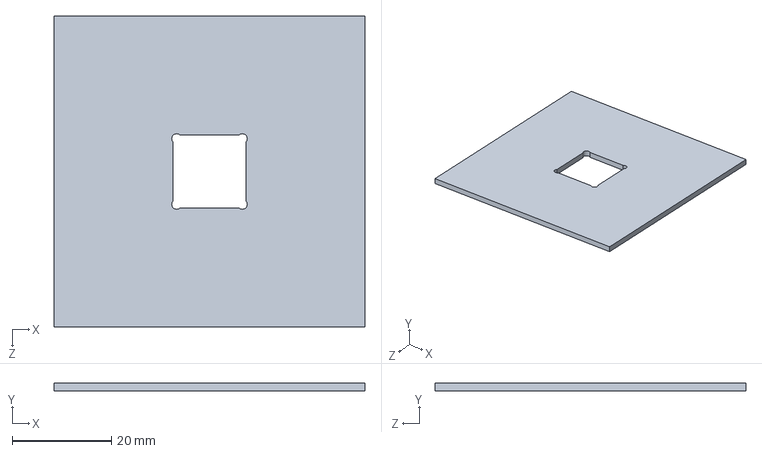
[picture p168: CAD file, 2022-12-01]
Hardware/SW_Project/20210510_SW/方孔这么开.SLDPRT
62.6 x 1.60 x 62.6 mm
