oldgerman/ODGIRON/Hardware/SW_Project/20210208_SW/GBS.dxf

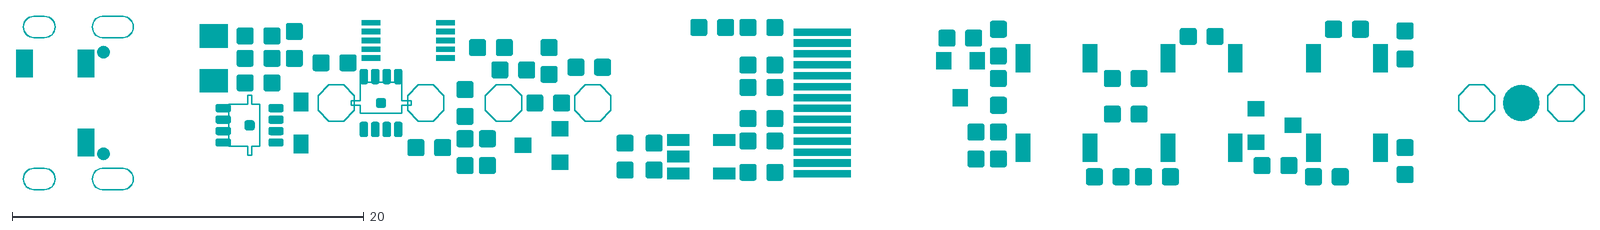
[picture p169: CAD file, 2022-12-01]
Hardware/SW_Project/20210208_SW/GBS.dxf
89.1 x 9.85
