oldgerman/ODGIRON/Hardware/SW_Project/20210510_SW/T12手柄/sttc_037_tip.SLDPRT

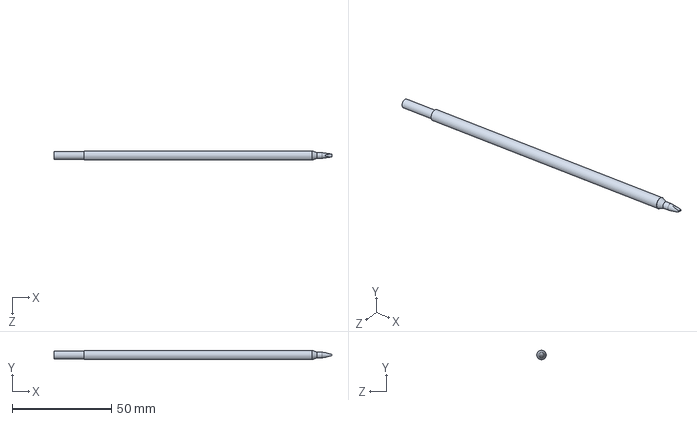
[picture p170: CAD file, 2022-12-01]
Hardware/SW_Project/20210510_SW/T12手柄/sttc_037_tip.SLDPRT
140.0 x 4.83 x 4.83 mm
