oldgerman/ODGIRON/Hardware/SW_Project/20210208_SW/1223-固定片.STL

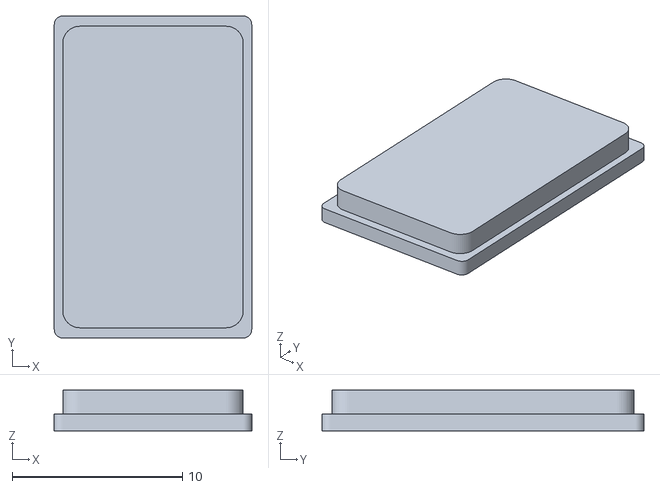
[picture p171: CAD file, 2022-12-01]
Hardware/SW_Project/20210208_SW/1223-固定片.STL
11.6 x 18.9 x 2.40
