oldgerman/ODGIRON/Hardware/SW_Project/20210510_SW/T12手柄/handle_top.SLDPRT

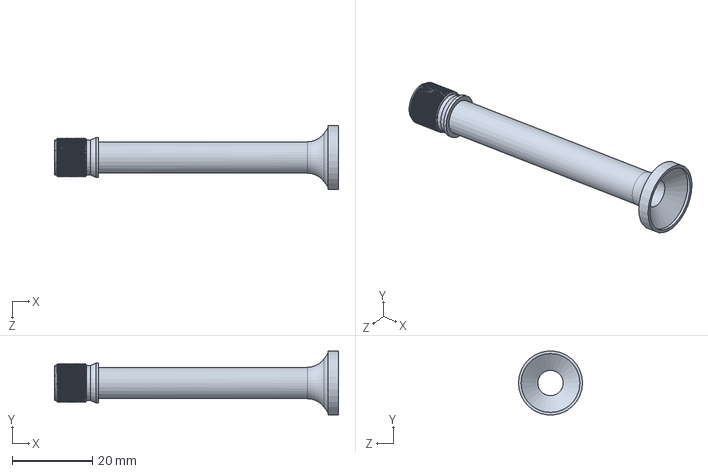
[picture p172: CAD file, 2022-12-01]
Hardware/SW_Project/20210510_SW/T12手柄/handle_top.SLDPRT
70.8 x 15.9 x 16.0 mm
