oldgerman/ODGIRON/Hardware/SW_Project/20210510_SW/TactileButton(5mm)_SMD.stp

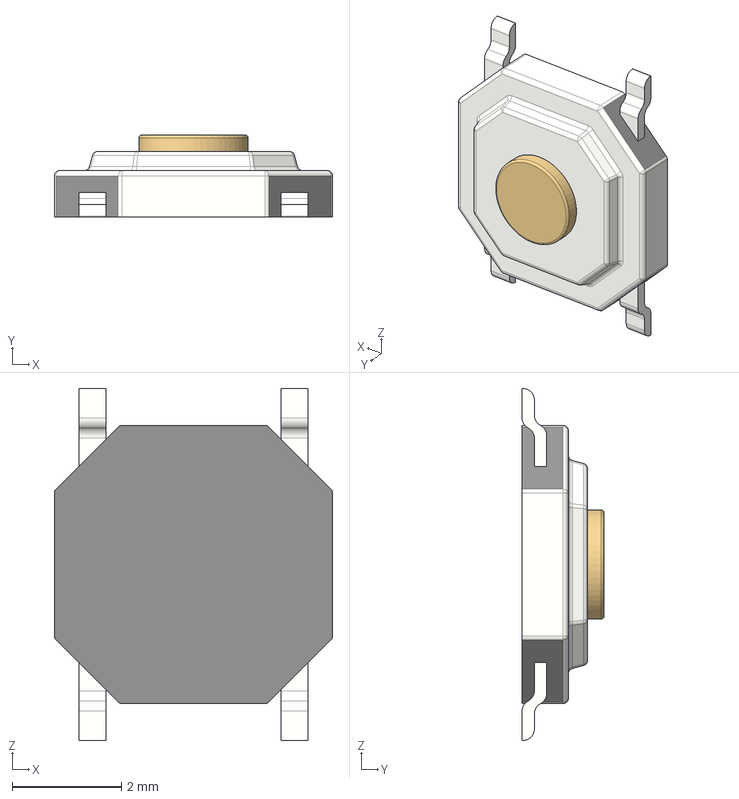
[picture p173: CAD file, 2022-12-01]
Hardware/SW_Project/20210510_SW/TactileButton(5mm)_SMD.stp
5.10 x 1.50 x 6.45 mm
