oldgerman/ODGIRON/Hardware/SW_Project/20210510_SW/m1.6x2.3x2热熔土字螺母.SLDPRT

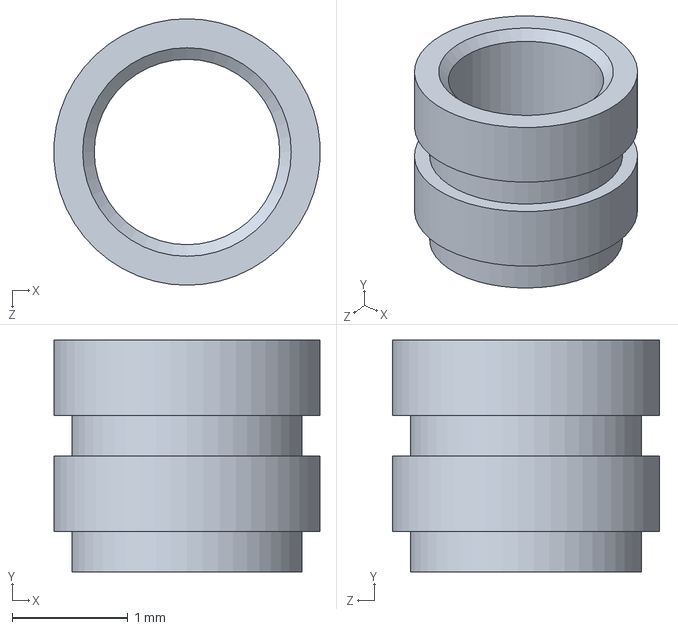
[picture p175: CAD file, 2022-12-01]
Hardware/SW_Project/20210510_SW/m1.6x2.3x2热熔土字螺母.SLDPRT
2.30 x 2.00 x 2.30 mm
