oldgerman/ODGIRON/Hardware/SW_Project/20210208_SW/1223-下壳-分模+0.3.STL

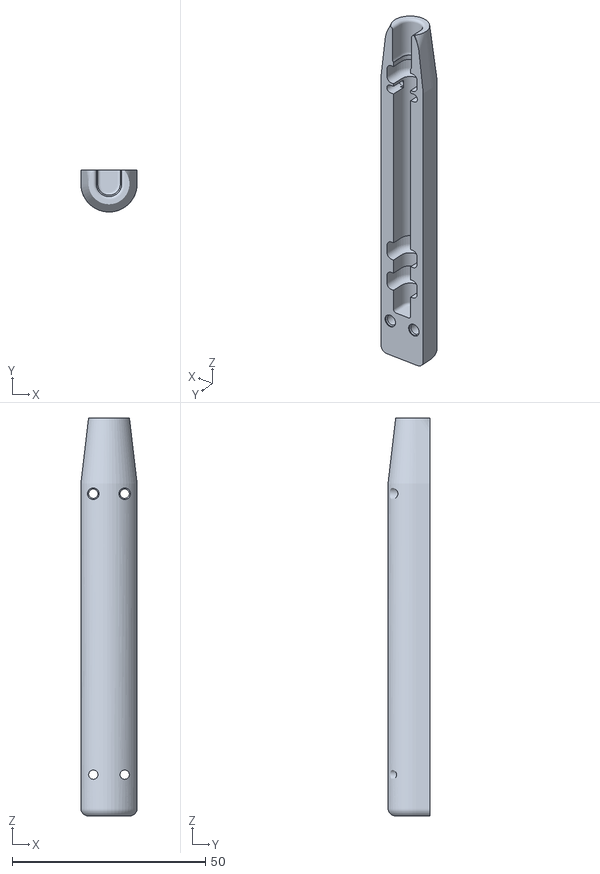
[picture p176: CAD file, 2022-12-01]
Hardware/SW_Project/20210208_SW/1223-下壳-分模+0.3.STL
14.6 x 10.9 x 103.1
