oldgerman/ODGIRON/Hardware/SW_Project/20210208_SW/0322-PCB基板.SLDPRT

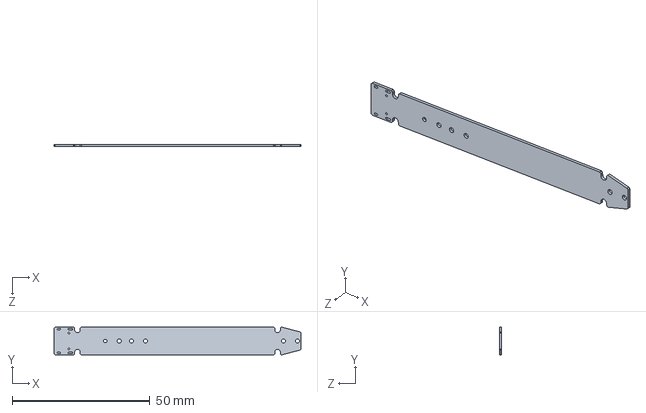
[picture p177: CAD file, 2022-12-01]
Hardware/SW_Project/20210208_SW/0322-PCB基板.SLDPRT
89.8 x 10.2 x 0.85 mm
