oldgerman/ODGIRON/Hardware/SW_Project/20210510_SW/m1.6x3十字圆头螺丝.SLDPRT

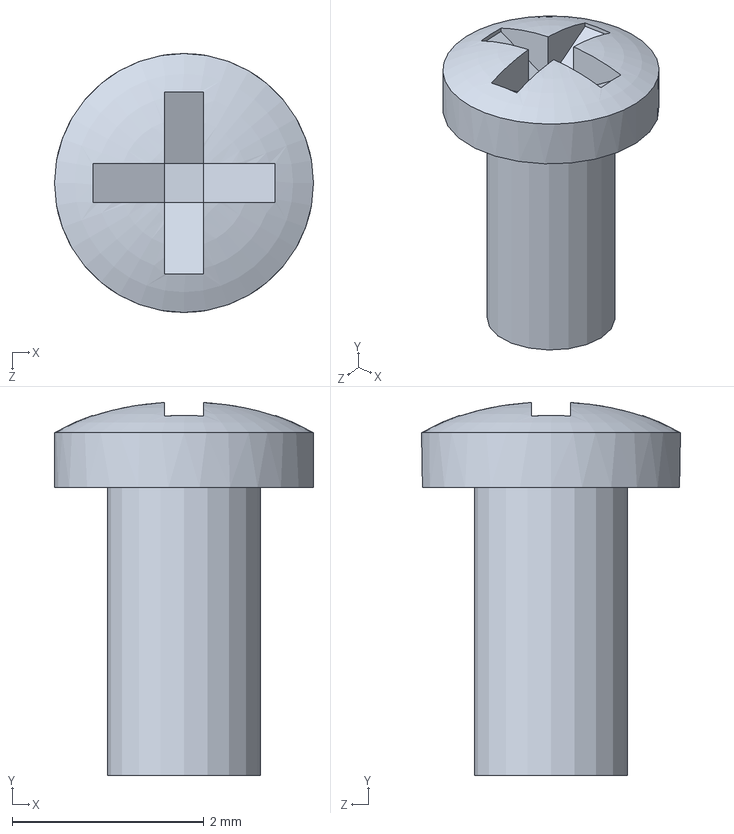
[picture p178: CAD file, 2022-12-01]
Hardware/SW_Project/20210510_SW/m1.6x3十字圆头螺丝.SLDPRT
2.70 x 3.89 x 2.70 mm
