oldgerman/ODGIRON/Hardware/SW_Project/20210208_SW/1223-上壳-分模+0.6.STL

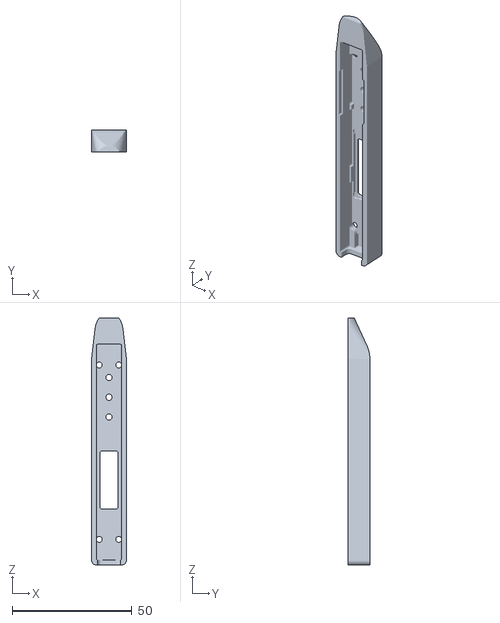
[picture p179: CAD file, 2022-12-01]
Hardware/SW_Project/20210208_SW/1223-上壳-分模+0.6.STL
14.6 x 9.13 x 103.1
