oldgerman/ODGIRON/Hardware/SW_Project/20210510_SW/m1.6x2.5x1.5热熔土字螺母.SLDPRT

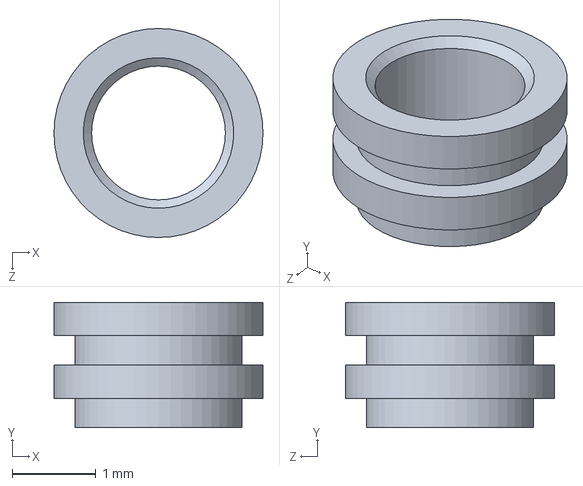
[picture p180: CAD file, 2022-12-01]
Hardware/SW_Project/20210510_SW/m1.6x2.5x1.5热熔土字螺母.SLDPRT
2.50 x 1.50 x 2.50 mm
