oldgerman/ODGIRON/Hardware/SW_Project/20210510_SW/BUZZER_offset_5.2X5.2X2.0MM.SLDPRT

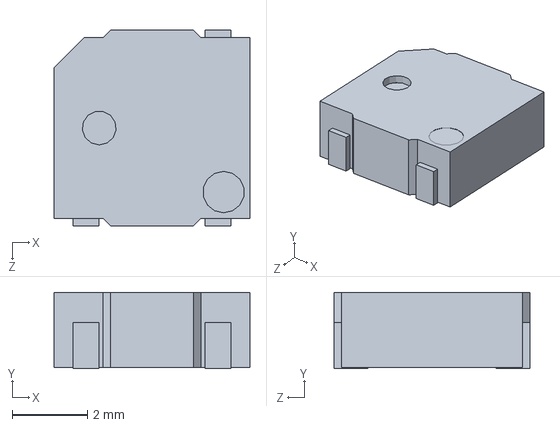
[picture p181: CAD file, 2022-12-01]
Hardware/SW_Project/20210510_SW/BUZZER_offset_5.2X5.2X2.0MM.SLDPRT
5.20 x 2.03 x 5.20 mm
