oldgerman/ODGIRON/Hardware/SW_Project/20210510_SW/ODG_TS100外壳推敲.SLDPRT

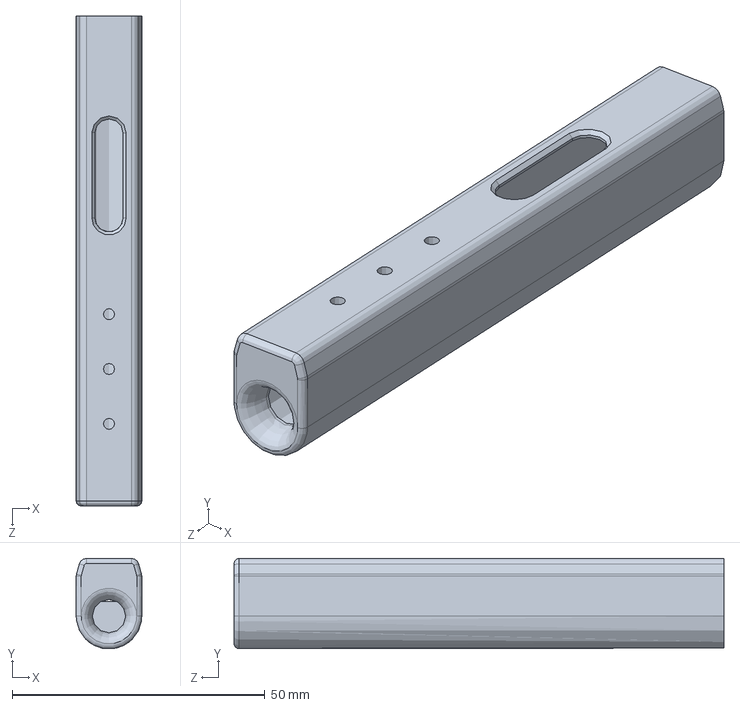
[picture p182: CAD file, 2022-12-01]
Hardware/SW_Project/20210510_SW/ODG_TS100外壳推敲.SLDPRT
13.0 x 17.9 x 97.0 mm
