oldgerman/ODGIRON/Hardware/SW_Project/20210510_SW/1223-拼接.SLDPRT

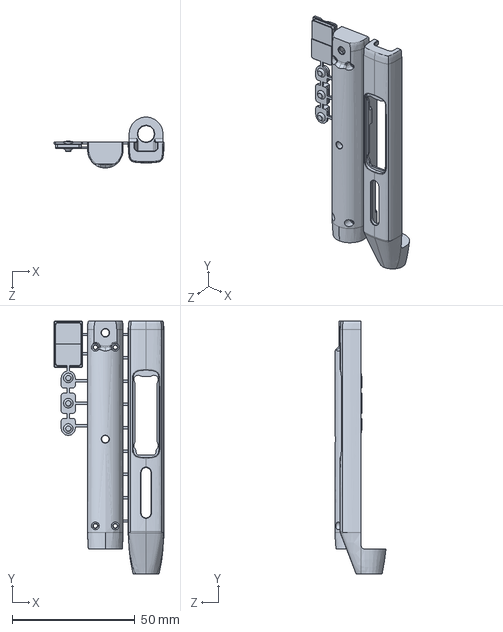
[picture p183: CAD file, 2022-12-01]
Hardware/SW_Project/20210510_SW/1223-拼接.SLDPRT
44.8 x 103.1 x 20.8 mm
