oldgerman/ODGIRON/Hardware/SW_Project/20210510_SW/0326-上壳-分模.SLDPRT

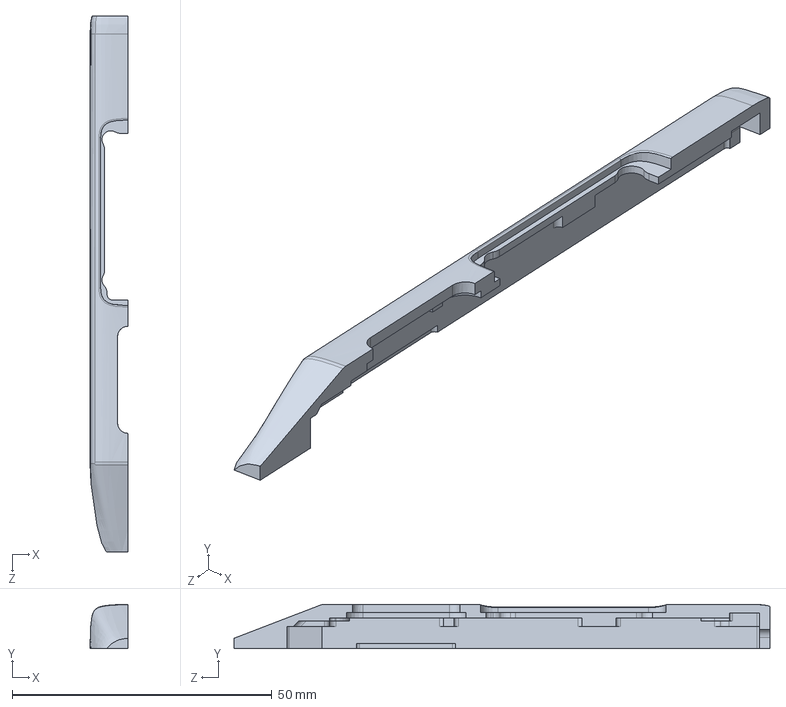
[picture p184: CAD file, 2022-12-01]
Hardware/SW_Project/20210510_SW/0326-上壳-分模.SLDPRT
7.30 x 8.53 x 103.1 mm
