oldgerman/ODGIRON/Hardware/SW_Project/20210510_SW/ODG_TS100外壳-上壳推敲.SLDPRT

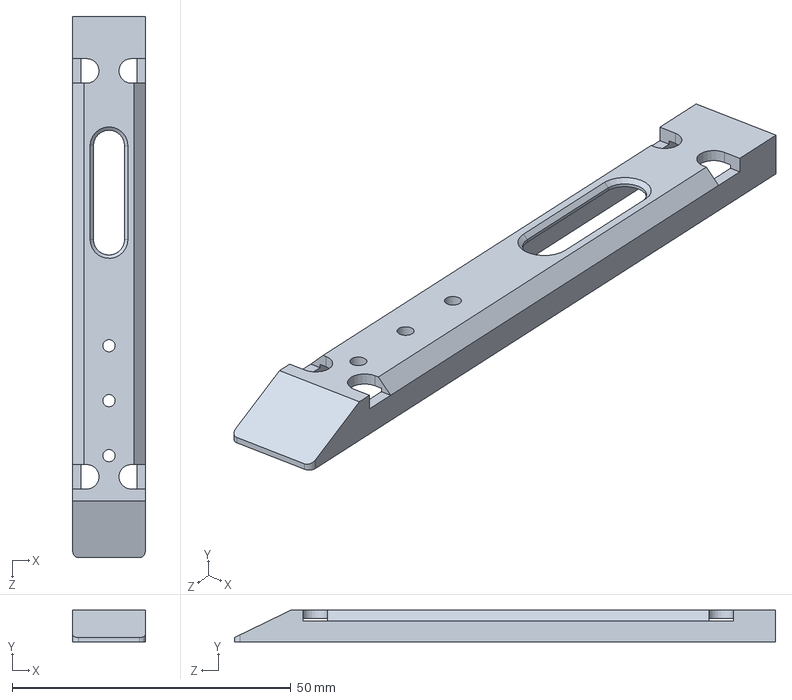
[picture p185: CAD file, 2022-12-01]
Hardware/SW_Project/20210510_SW/ODG_TS100外壳-上壳推敲.SLDPRT
13.0 x 5.73 x 97.0 mm
