oldgerman/ODGIRON/Hardware/SW_Project/20210510_SW/m1.6x14_杯头螺丝.STEP

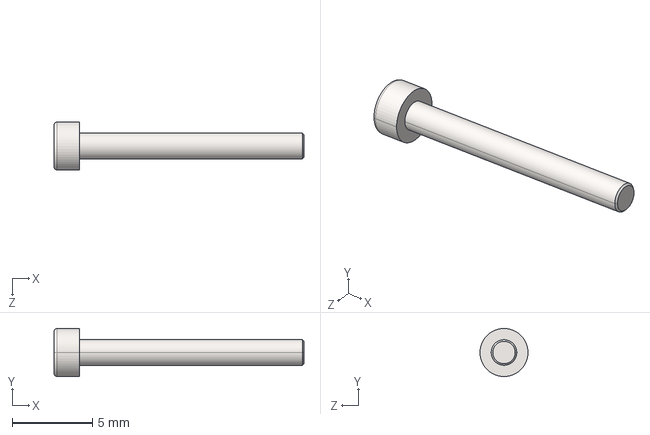
[picture p186: CAD file, 2022-12-01]
Hardware/SW_Project/20210510_SW/m1.6x14_杯头螺丝.STEP
15.6 x 3.00 x 3.00 mm
