oldgerman/ODGIRON/Hardware/SW_Project/20210510_SW/0510-上壳-开关-中间按钮.SLDPRT

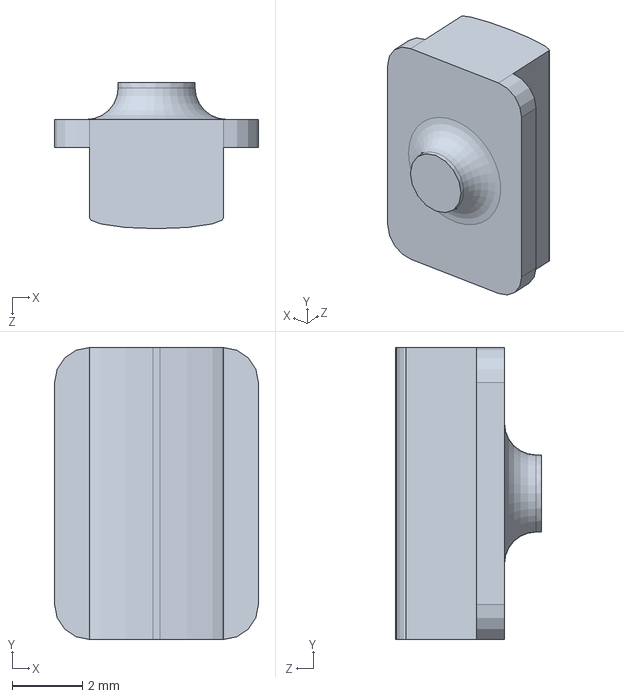
[picture p187: CAD file, 2022-12-01]
Hardware/SW_Project/20210510_SW/0510-上壳-开关-中间按钮.SLDPRT
5.80 x 8.30 x 4.15 mm
