oldgerman/ODGIRON/Hardware/SW_Project/20210510_SW/TB67S289FTG P-VQFN48-0707-0.50-004.SLDPRT

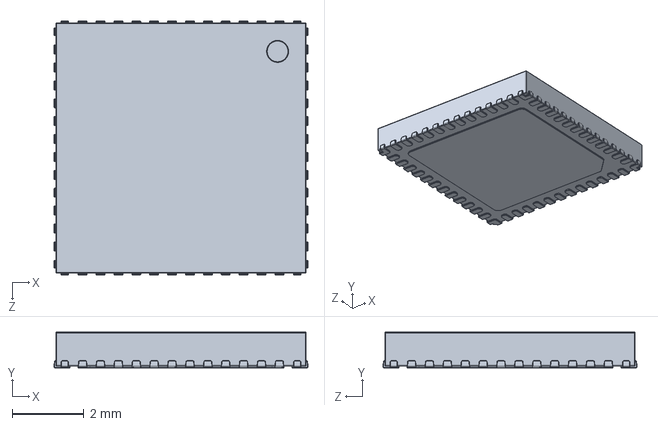
[picture p188: CAD file, 2022-12-01]
Hardware/SW_Project/20210510_SW/TB67S289FTG P-VQFN48-0707-0.50-004.SLDPRT
7.10 x 1.00 x 7.10 mm
