oldgerman/ODGIRON/Hardware/SW_Project/20210510_SW/3.2mm开口冷压端子.SLDPRT

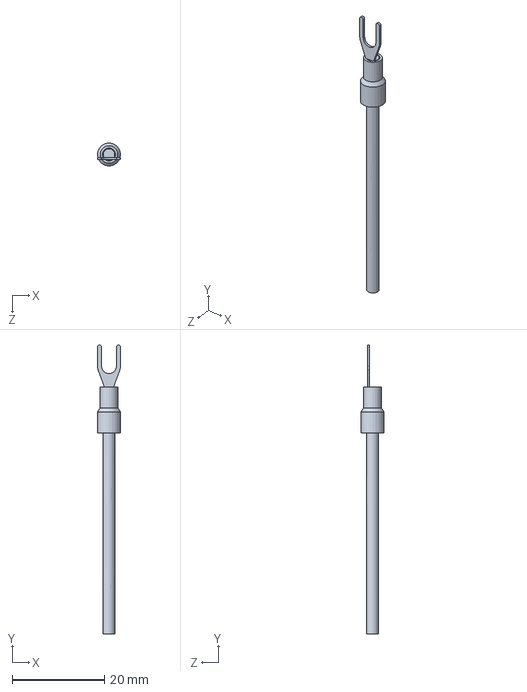
[picture p189: CAD file, 2022-12-01]
Hardware/SW_Project/20210510_SW/3.2mm开口冷压端子.SLDPRT
5.00 x 62.6 x 5.00 mm
