oldgerman/ODGIRON/Hardware/SW_Project/20210510_SW/平台阶定位珠.SLDPRT

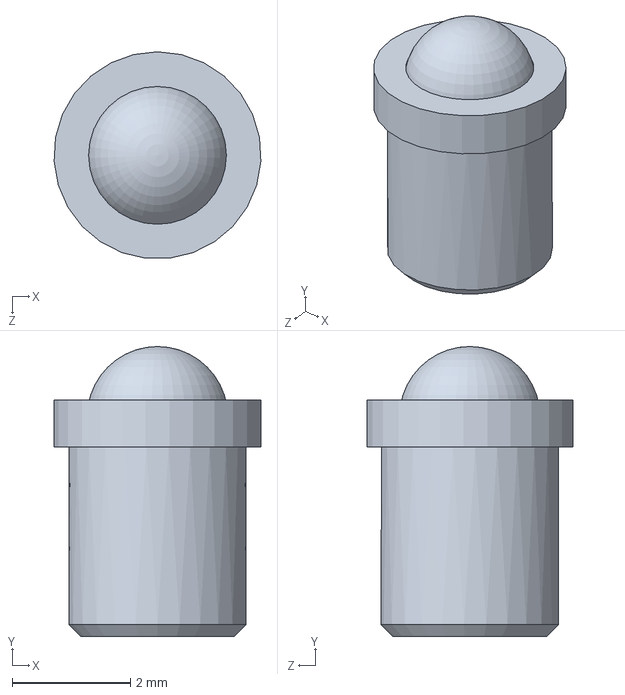
[picture p190: CAD file, 2022-12-01]
Hardware/SW_Project/20210510_SW/平台阶定位珠.SLDPRT
3.49 x 4.90 x 3.49 mm
