oldgerman/ODGIRON/Hardware/SW_Project/20210510_SW/保险丝座.SLDPRT

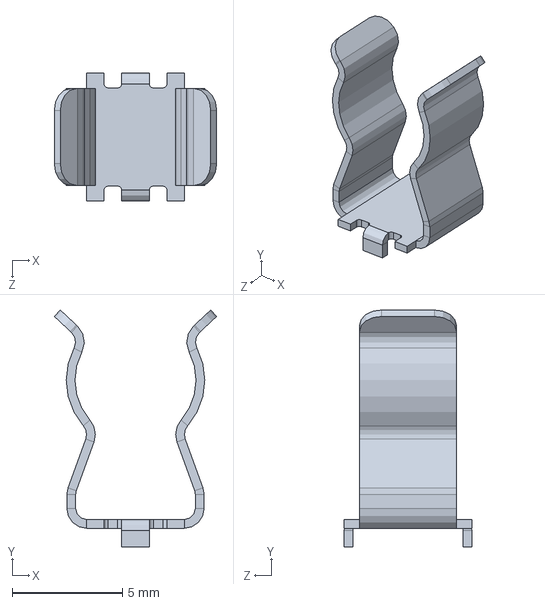
[picture p191: CAD file, 2022-12-01]
Hardware/SW_Project/20210510_SW/保险丝座.SLDPRT
7.38 x 10.8 x 5.82 mm
