oldgerman/ODGIRON/Hardware/SW_Project/20210510_SW/IN-9.52卡套衬套.SLDPRT

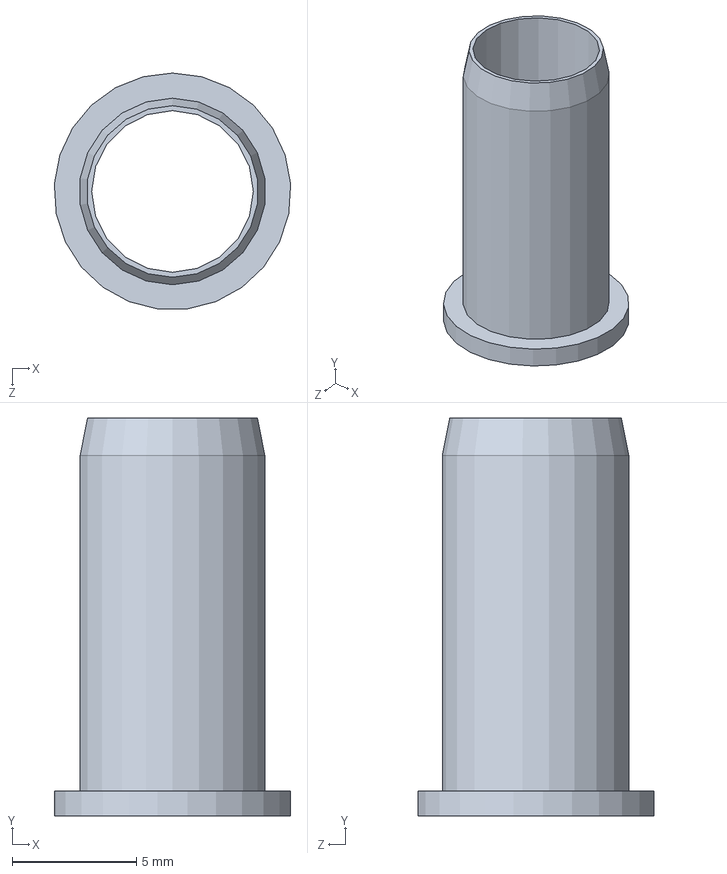
[picture p192: CAD file, 2022-12-01]
Hardware/SW_Project/20210510_SW/IN-9.52卡套衬套.SLDPRT
9.50 x 16.0 x 9.48 mm
