oldgerman/ODGIRON/Hardware/SW_Project/20210510_SW/T12-K Hakko.SLDPRT

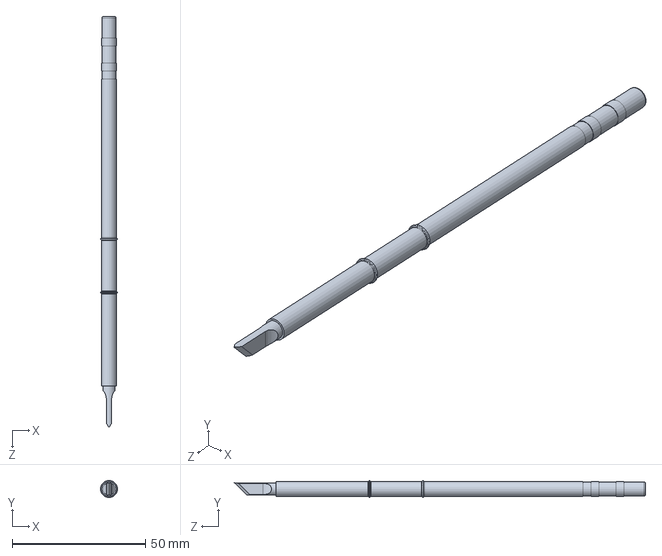
[picture p193: CAD file, 2022-12-01]
Hardware/SW_Project/20210510_SW/T12-K Hakko.SLDPRT
6.39 x 6.39 x 154.1 mm
