oldgerman/ODGIRON/Hardware/SW_Project/20210510_SW/1223-固定片_stm32f103厚封装.SLDPRT

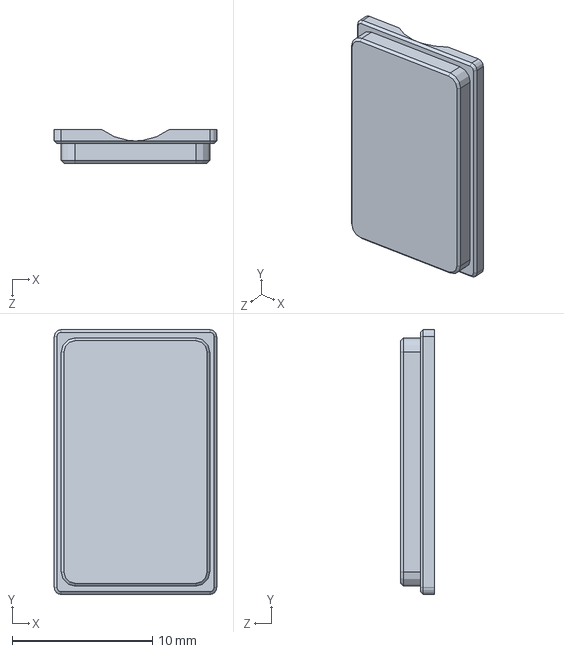
[picture p194: CAD file, 2022-12-01]
Hardware/SW_Project/20210510_SW/1223-固定片_stm32f103厚封装.SLDPRT
11.6 x 18.9 x 2.40 mm
