oldgerman/ODGIRON/Hardware/SW_Project/20210510_SW/0326-上壳-开关.SLDPRT

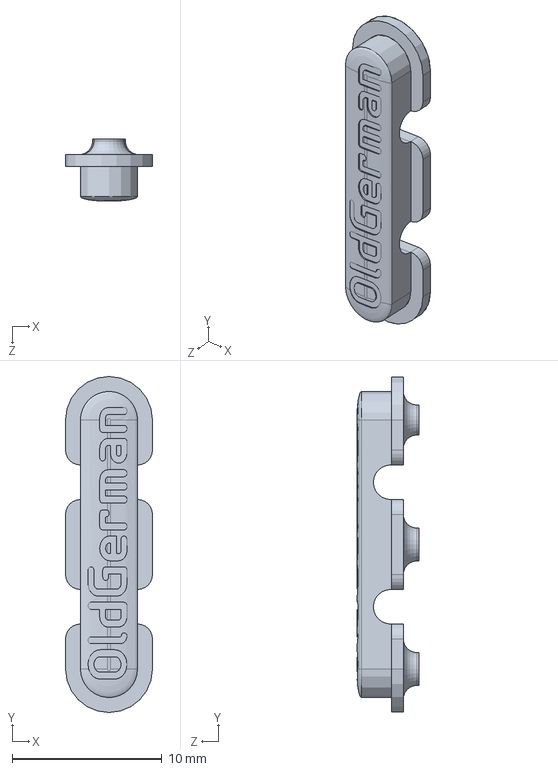
[picture p195: CAD file, 2022-12-01]
Hardware/SW_Project/20210510_SW/0326-上壳-开关.SLDPRT
5.80 x 22.4 x 4.15 mm
