oldgerman/ODGIRON/Hardware/SW_Project/20210510_SW/KY-015.SLDPRT

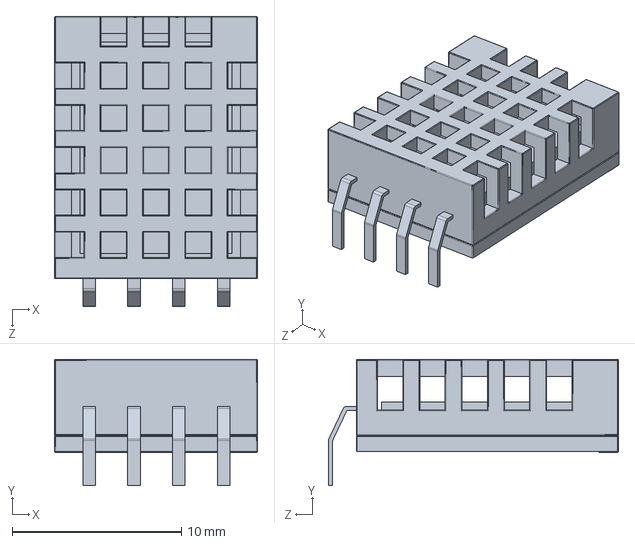
[picture p196: CAD file, 2022-12-01]
Hardware/SW_Project/20210510_SW/KY-015.SLDPRT
12.0 x 7.45 x 17.1 mm
