oldgerman/ODGIRON/Hardware/SW_Project/20210510_SW/One Plus Type C.SLDPRT

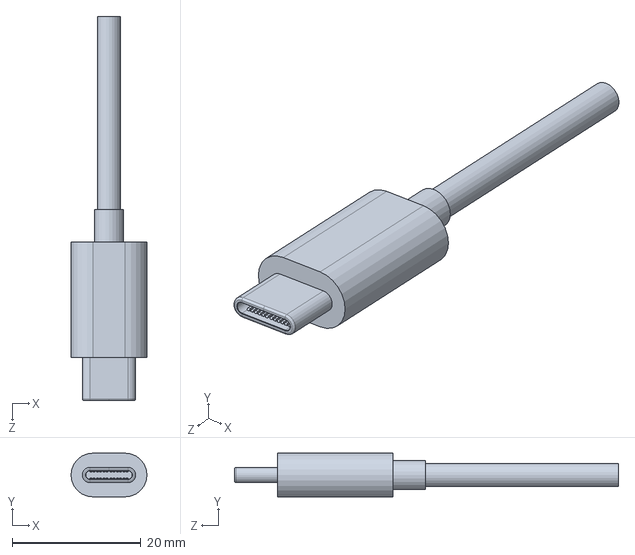
[picture p197: CAD file, 2022-12-01]
Hardware/SW_Project/20210510_SW/One Plus Type C.SLDPRT
11.8 x 6.80 x 59.6 mm
