oldgerman/ODGIRON/Hardware/SW_Project/20210510_SW/平台阶定位珠-行程0.55mm.SLDPRT

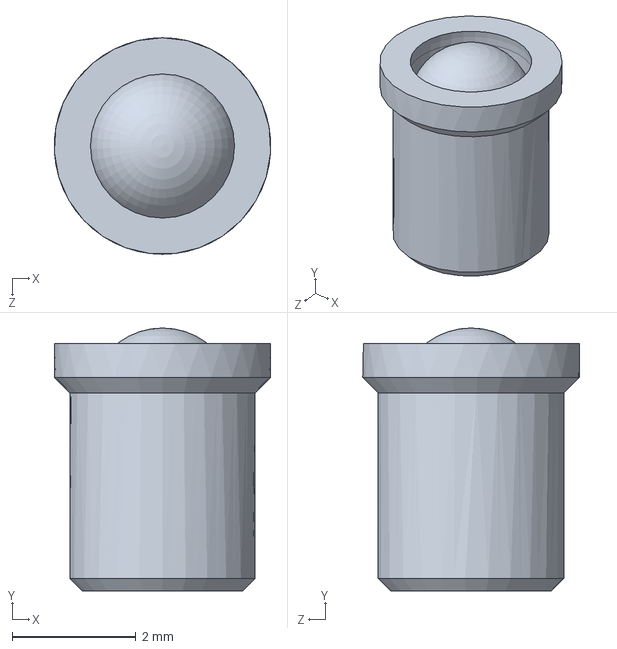
[picture p198: CAD file, 2022-12-01]
Hardware/SW_Project/20210510_SW/平台阶定位珠-行程0.55mm.SLDPRT
3.49 x 4.25 x 3.50 mm
