oldgerman/ODGIRON/Hardware/SW_Project/20210510_SW/0510-上壳-开关-两边按钮.SLDPRT

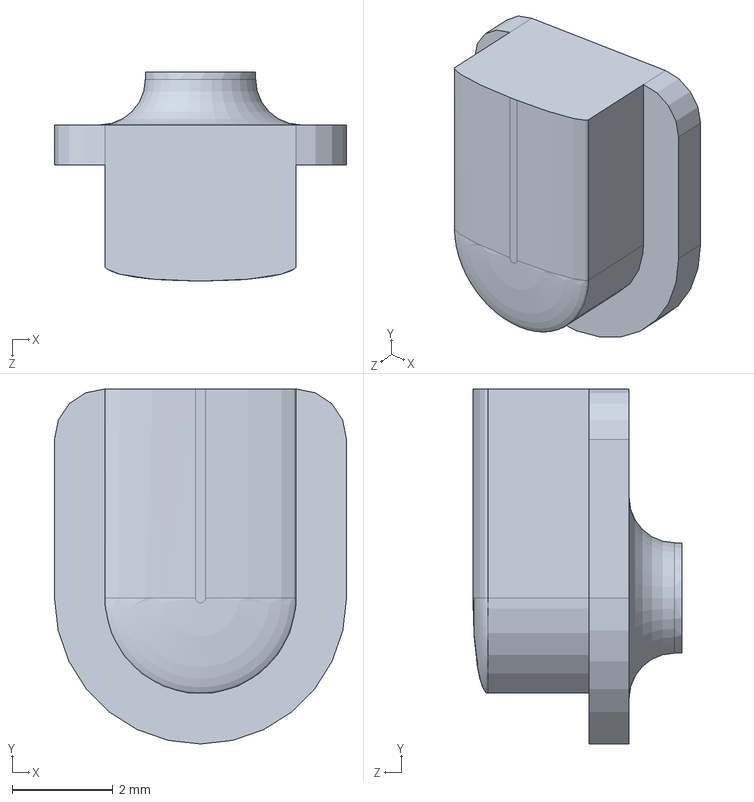
[picture p199: CAD file, 2022-12-01]
Hardware/SW_Project/20210510_SW/0510-上壳-开关-两边按钮.SLDPRT
5.80 x 7.05 x 4.15 mm
