oldgerman/ODGIRON/Hardware/SW_Project/20210510_SW/0.91_oled.SLDPRT

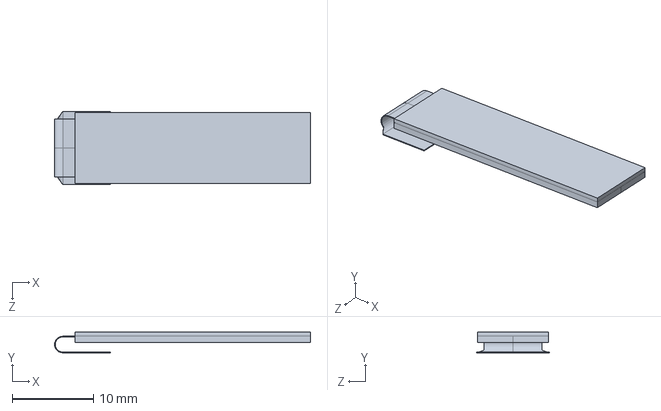
[picture p200: CAD file, 2022-12-01]
Hardware/SW_Project/20210510_SW/0.91_oled.SLDPRT
31.5 x 2.55 x 9.00 mm
