oldgerman/ODGIRON/Hardware/SW_Project/20210510_SW/1223-下壳-分模.SLDPRT

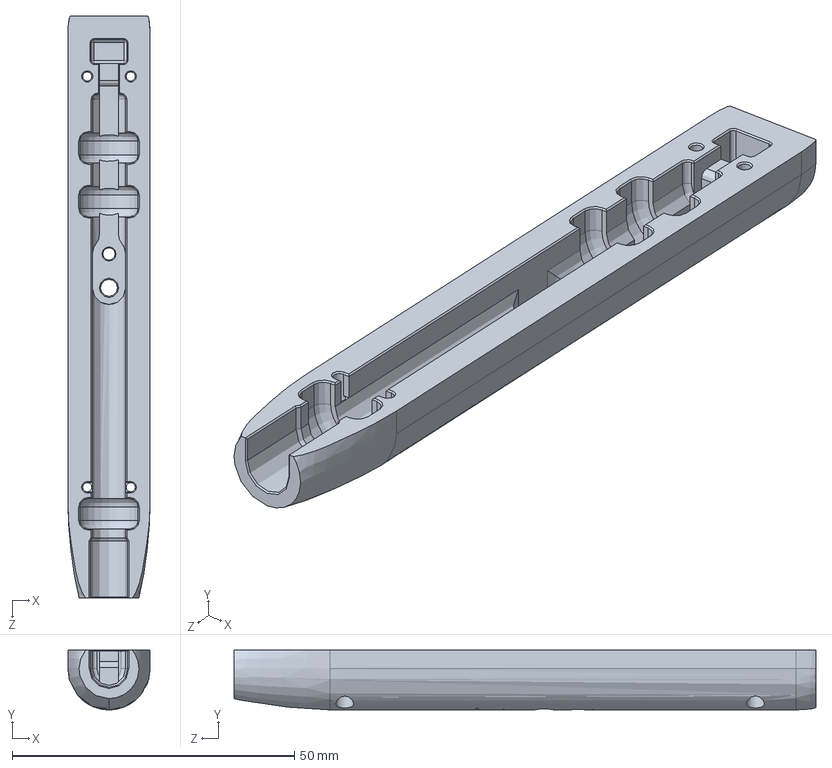
[picture p201: CAD file, 2022-12-01]
Hardware/SW_Project/20210510_SW/1223-下壳-分模.SLDPRT
14.6 x 10.6 x 103.1 mm
