oldgerman/ODGIRON/Hardware/SW_Project/20210510_SW/LGA-16_3x3mm_P0.5mm.SLDPRT

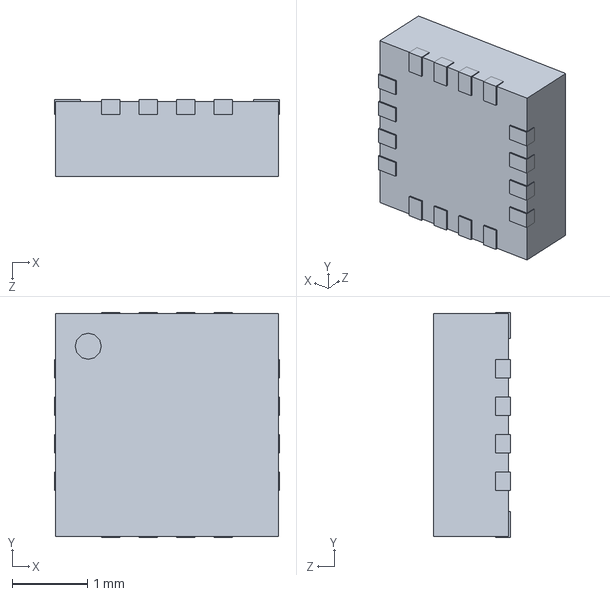
[picture p202: CAD file, 2022-12-01]
Hardware/SW_Project/20210510_SW/LGA-16_3x3mm_P0.5mm.SLDPRT
3.00 x 3.00 x 1.02 mm
