oldgerman/ODGIRON/Hardware/SW_Project/20210510_SW/1223-固定片_UFQFPN48-把其他拼接.SLDPRT

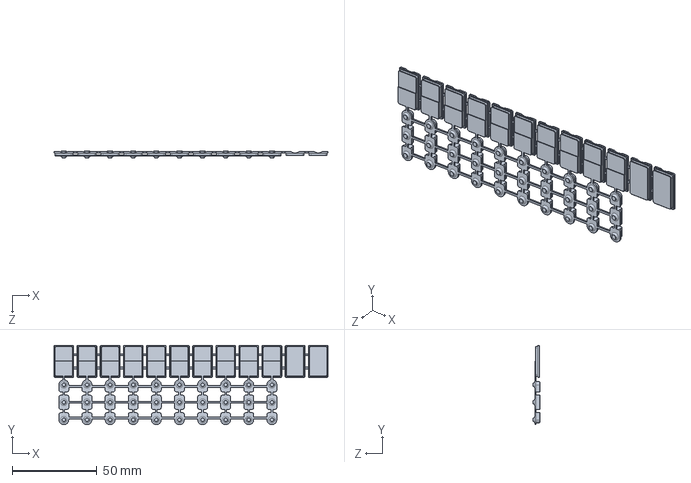
[picture p203: CAD file, 2022-12-01]
Hardware/SW_Project/20210510_SW/1223-固定片_UFQFPN48-把其他拼接.SLDPRT
161.2 x 46.7 x 4.15 mm
