oldgerman/ODGIRON/Hardware/SW_Project/20210510_SW/ts100 Tip Model.SLDPRT

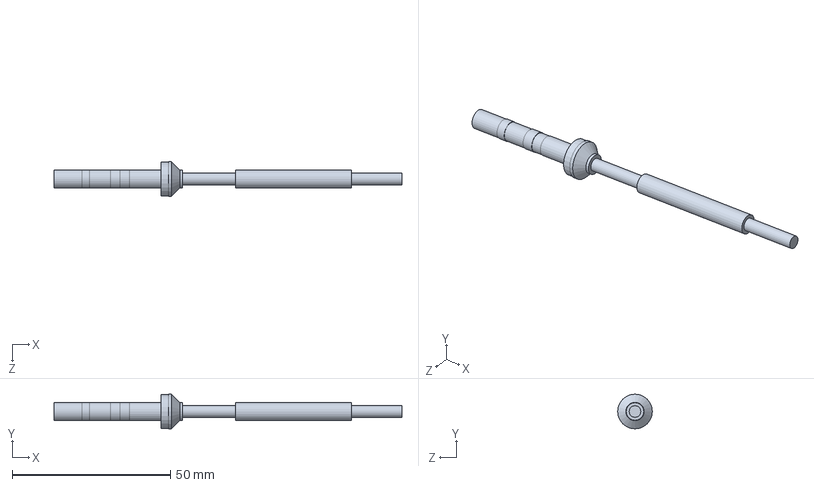
[picture p204: CAD file, 2022-12-01]
Hardware/SW_Project/20210510_SW/ts100 Tip Model.SLDPRT
110.1 x 11.0 x 11.0 mm
