oldgerman/ODGIRON/Hardware/SW_Project/20210510_SW/1223-上壳-荣耀8X听筒网.SLDPRT

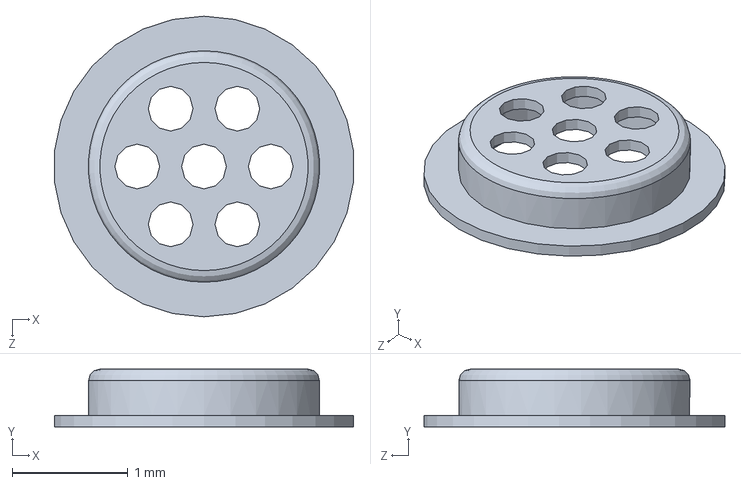
[picture p206: CAD file, 2022-12-01]
Hardware/SW_Project/20210510_SW/1223-上壳-荣耀8X听筒网.SLDPRT
2.59 x 0.5 x 2.60 mm
