oldgerman/ODGIRON/Hardware/SW_Project/20210510_SW/0326-oled面板.SLDPRT

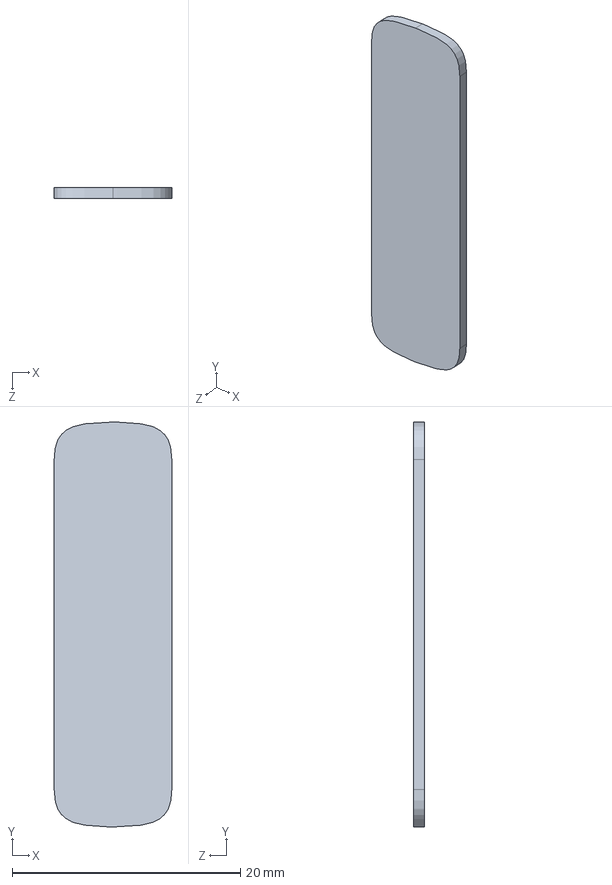
[picture p207: CAD file, 2022-12-01]
Hardware/SW_Project/20210510_SW/0326-oled面板.SLDPRT
10.3 x 35.5 x 1.00 mm
