oldgerman/ODGIRON/Hardware/SW_Project/20210510_SW/ODG_TS100外壳-下壳推敲.SLDPRT

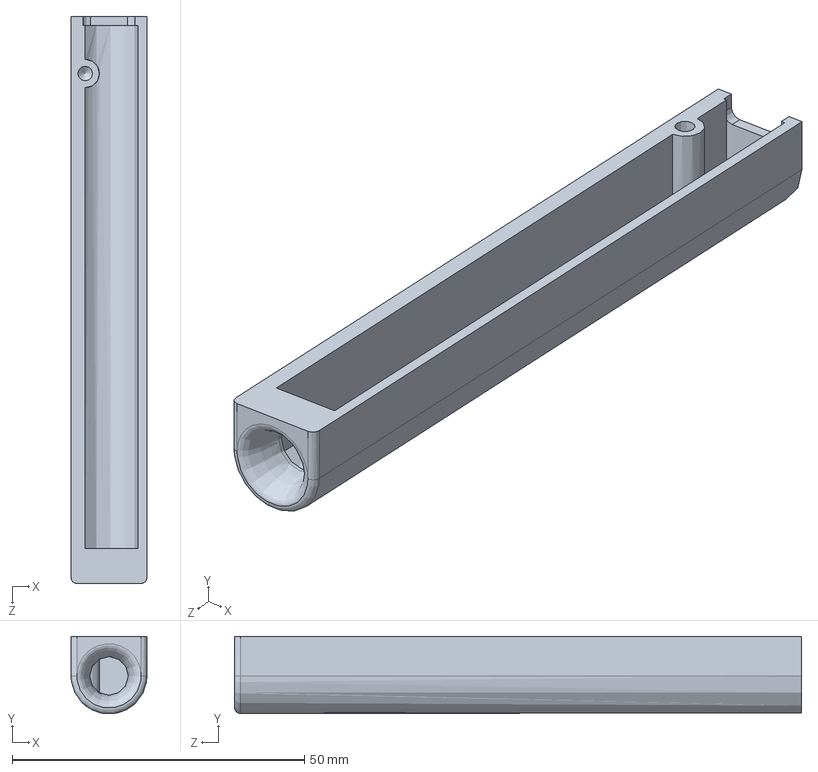
[picture p208: CAD file, 2022-12-01]
Hardware/SW_Project/20210510_SW/ODG_TS100外壳-下壳推敲.SLDPRT
13.0 x 13.2 x 97.0 mm
