oldgerman/ODGIRON/Hardware/SW_Project/20210510_SW/接地钣金.SLDPRT

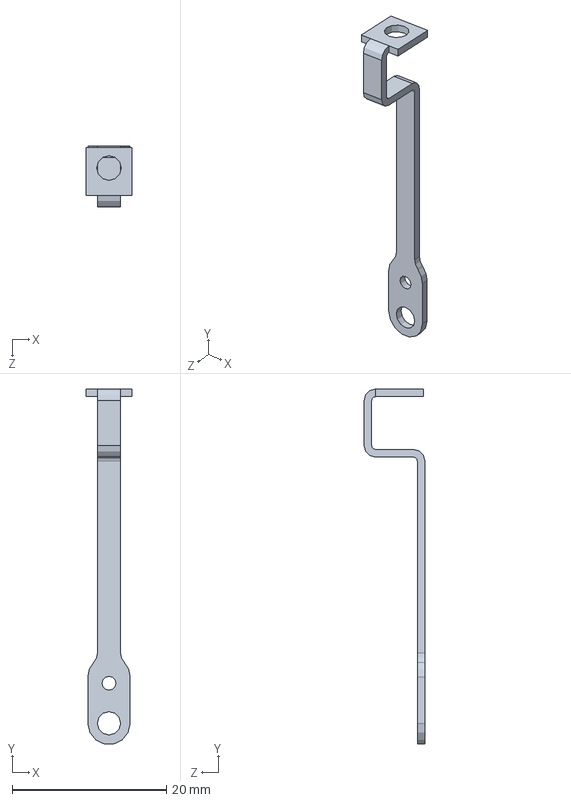
[picture p209: CAD file, 2022-12-01]
Hardware/SW_Project/20210510_SW/接地钣金.SLDPRT
6.00 x 46.0 x 7.90 mm
