oldgerman/ODGIRON/Hardware/SW_Project/20210510_SW/0.86o_led_96x32.SLDPRT

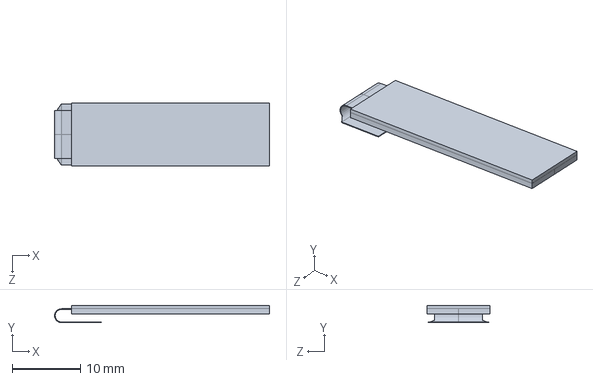
[picture p210: CAD file, 2022-12-01]
Hardware/SW_Project/20210510_SW/0.86o_led_96x32.SLDPRT
31.6 x 2.55 x 9.20 mm
