oldgerman/ODGIRON/Hardware/Datasheets/T12烙铁头结构/QUICKO-STM32-OLED-1-3-Size-T12-DIY-Soldering-Station-With-Russian-Korean-English-Chinese-T12.jpg_q50.jpg

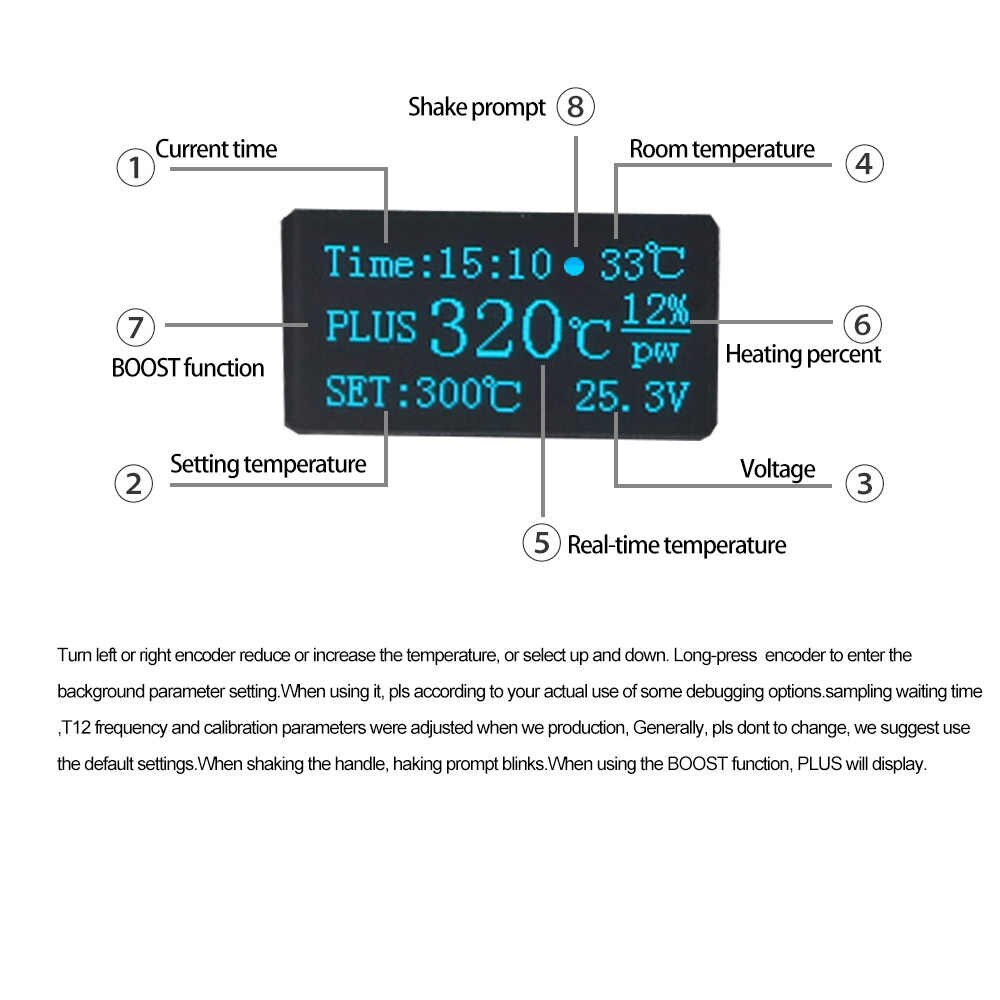
Hardware/Datasheets/T12烙铁头结构/QUICKO-STM32-OLED-1-3-Size-T12-DIY-Soldering-Station-With-Russian-Korean-English-Chinese-T12.jpg_q50.jpg
