oldgerman/ODGIRON/Hardware/Datasheets/T12烙铁头结构/T12-Handle-Soldering-Iron-Tips-SDL295987104-1-d8862.jpg

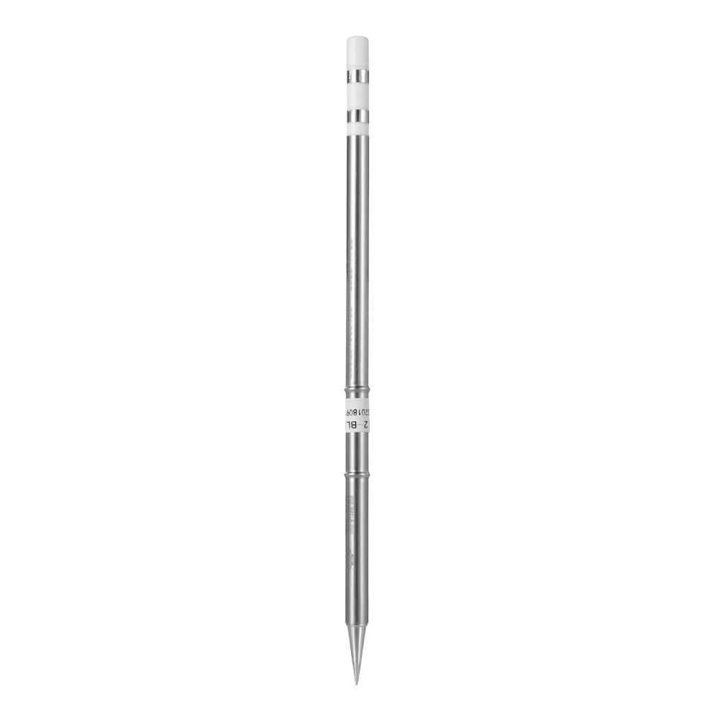
Hardware/Datasheets/T12烙铁头结构/T12-Handle-Soldering-Iron-Tips-SDL295987104-1-d8862.jpg
