oldgerman/ODGIRON/Hardware/Datasheets/T12烙铁头结构/Wiring-Diagrams.png

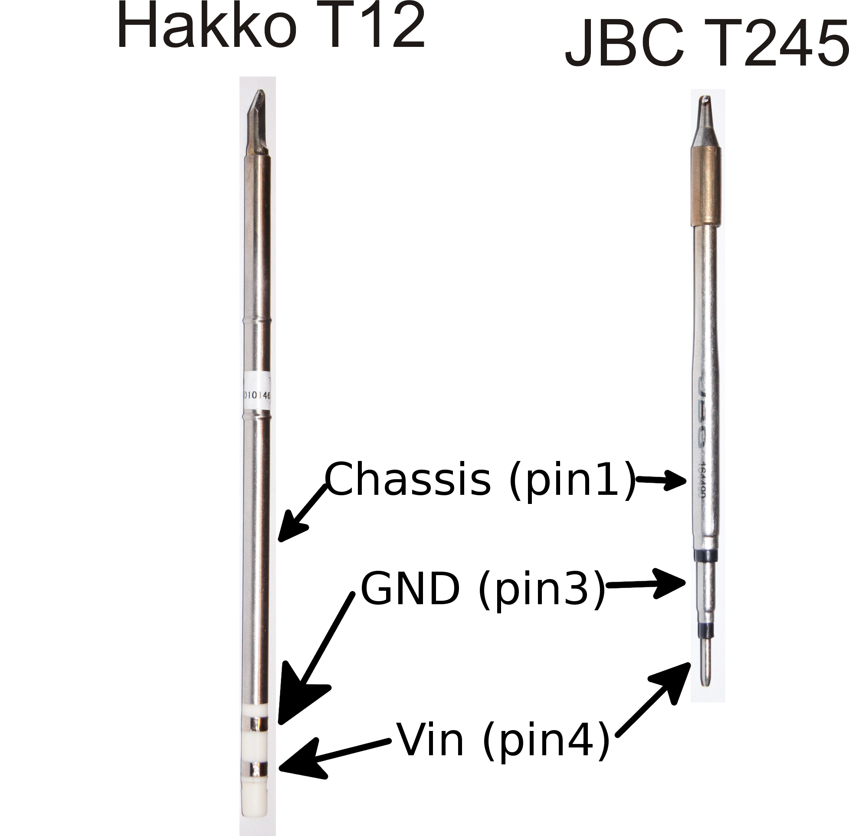
Hardware/Datasheets/T12烙铁头结构/Wiring-Diagrams.png
