oldgerman/ODGIRON/Hardware/PCB_Project/HAKKO_191-212/SWITCH-SCIENCE Soldering iron thermometer shield/38f2a293fd91a71d56a72b41b1d9fce8e9a5170f_2_598x500.png

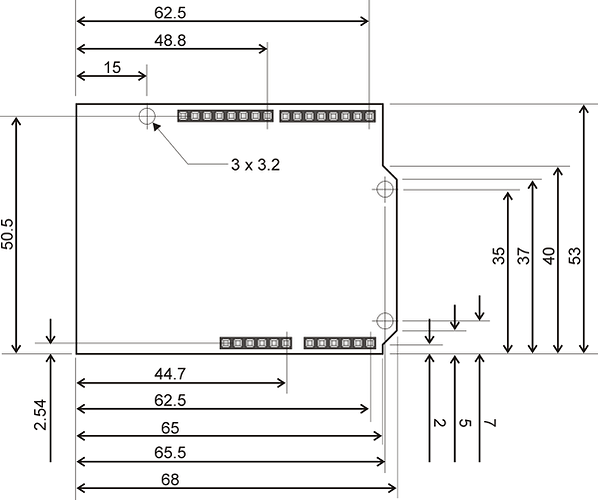
Hardware/PCB_Project/HAKKO_191-212/SWITCH-SCIENCE Soldering iron thermometer shield/38f2a293fd91a71d56a72b41b1d9fce8e9a5170f_2_598x500.png
