oldgerman/ODGIRON/Hardware/PCB_Project/HAKKO_191-212/SWITCH-SCIENCE Soldering iron thermometer shield/uno_dim.gif

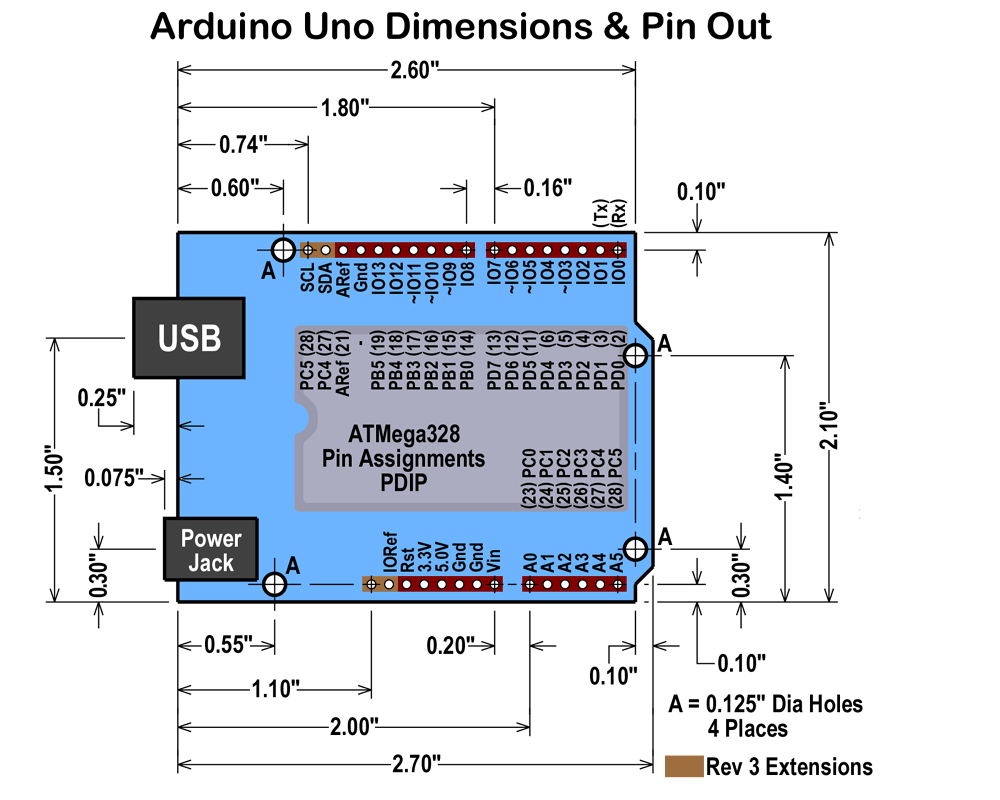
Hardware/PCB_Project/HAKKO_191-212/SWITCH-SCIENCE Soldering iron thermometer shield/uno_dim.gif
