oldgerman/ODGIRON/Hardware/SW_Project/20210510_SW/TS100 Soldering Iron ASSY.JPG

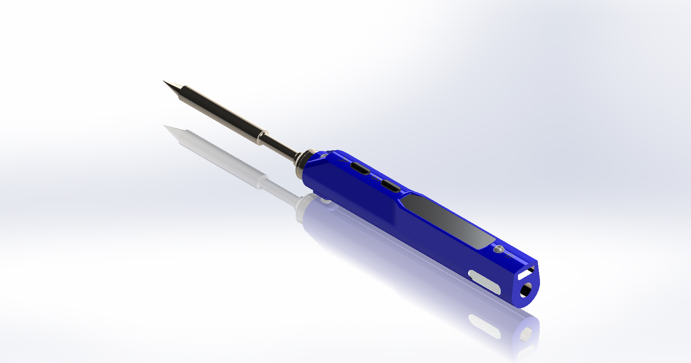
Hardware/SW_Project/20210510_SW/TS100 Soldering Iron ASSY.JPG
