oldgerman/ODGIRON/UID/mini-Symbols-bmp/Unisolder5.2界面参考(6).png

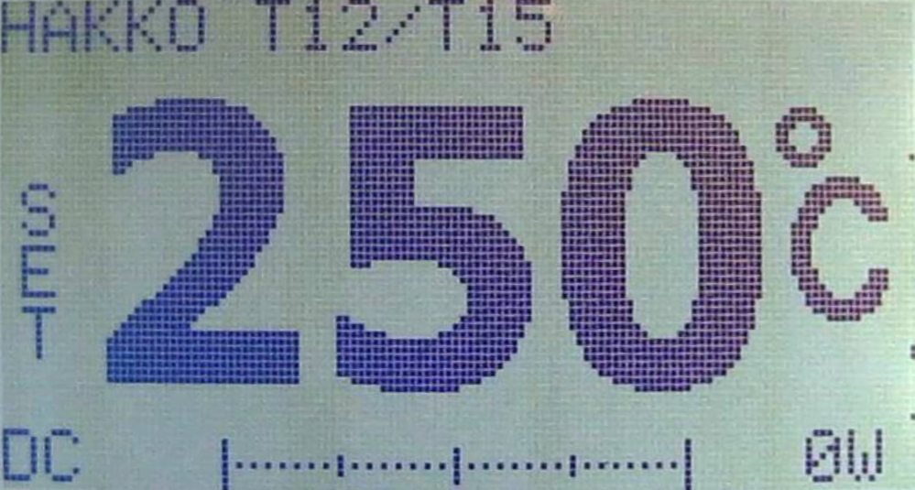
UID/mini-Symbols-bmp/Unisolder5.2界面参考(6).png
