oldgerman/ODGIRON/UID/reference/solder/62096552.jpg

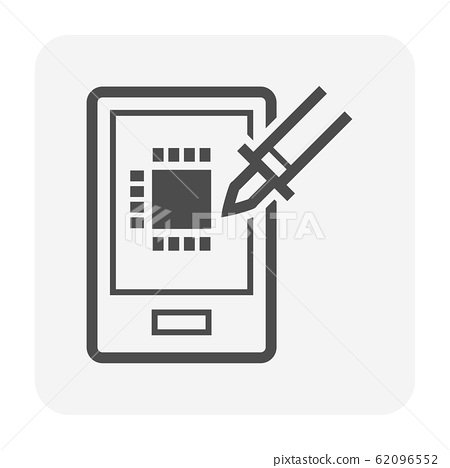
UID/reference/solder/62096552.jpg
