oldgerman/ODGIRON/UID/reference/solder/images (1).png

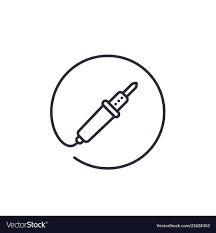
UID/reference/solder/images (1).png
