oldgerman/ODGIRON/UID/reference/solder/images.png

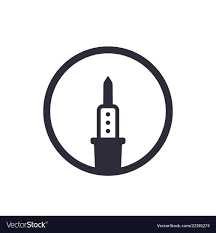
UID/reference/solder/images.png
