oldgerman/ODGIRON/UID/reference/solder/soldering-2976785-2487283.png

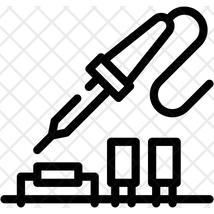
UID/reference/solder/soldering-2976785-2487283.png
