oldgerman/ODGIRON/Hardware/Datasheets/MEMS/MPU6050/Sparkfun-_MPU-6050_v12 (1)/Triple_Axis_Accelerometer_Gyro_Breakout_-_MPU-6050_v12.brd

## EAGLE design Hardware/Datasheets/MEMS/MPU6050/Sparkfun-_MPU-6050_v12 (1)/Triple_Axis_Accelerometer_Gyro_Breakout_-_MPU-6050_v12.brd (2022-12-01)

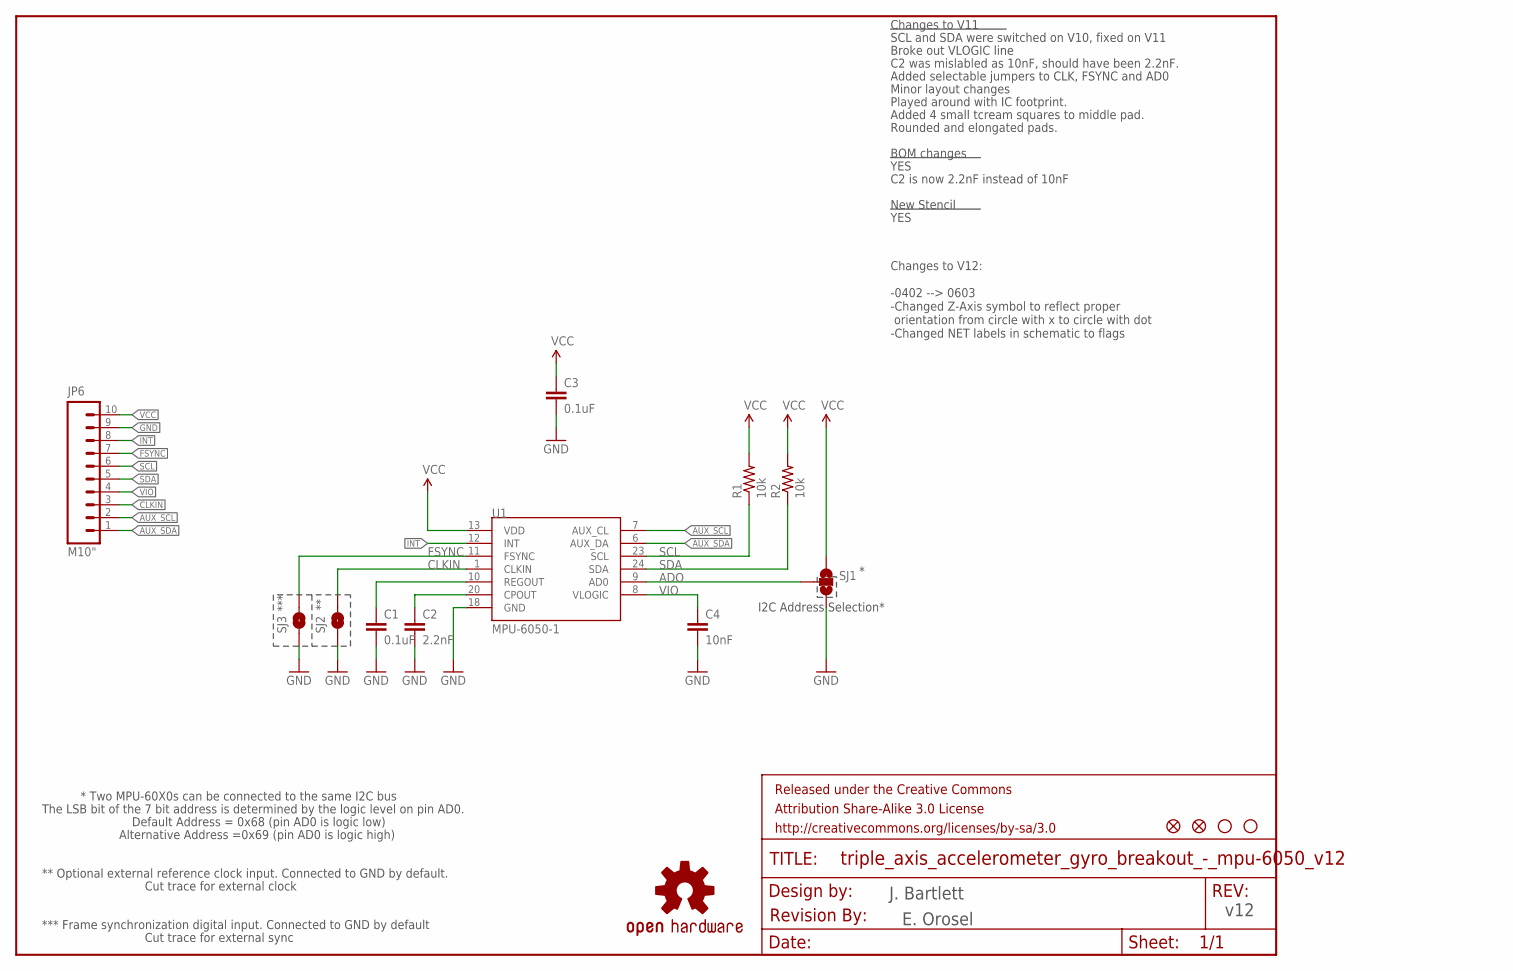
[picture p255: schematic Triple_Axis_Accelerometer_Gyro_Breakout_-_MPU-6050_v12.sch]

Parts:
C1, C3: 0.1uF; 0603-CAP
C2: 2.2nF; 0603-CAP
C4: 10nF; 0603-CAP
FRAME1: FRAME-LETTER; CREATIVE_COMMONS
JP2, JP5: FIDUCIALUFIDUCIAL; MICRO-FIDUCIAL
JP3, JP4: STAND-OFFTIGHT; STAND-OFF-TIGHT
JP6: M10"; 1X10
R1, R2: 10k; 0603-RES
SJ1: SOLDERJUMPER_2WAYPASTE2&3; SJ_3_PASTE2&3
SJ2, SJ3: SOLDERJUMPERTRACE; SJ_2S-TRACE
U1: MPU-6050-1; QFN-24-4MM2
U$1: OSHW-LOGOS; OSHW-LOGO-S
U$5: REVISION

Connections:
ADO: SJ1.2, U1.9 (AD0)
AUX_SCL: JP6.2, U1.7 (AUX_CL)
AUX_SDA: JP6.1, U1.6 (AUX_DA)
CLKIN: JP6.3, SJ2.2, U1.1 (CLKIN)
FSYNC: JP6.7, SJ3.2, U1.11 (FSYNC)
GND: C1.2, C2.2, C3.2, C4.2, JP6.9, SJ1.3, SJ2.1, SJ3.1, U1.18 (GND)
INT: JP6.8, U1.12 (INT)
unnamed: C2.1, U1.20 (CPOUT)
unnamed: C1.1, U1.10 (REGOUT)
SCL: JP6.6, R1.1, U1.23 (SCL)
SDA: JP6.5, R2.1, U1.24 (SDA)
VCC: C3.1, JP6.10, R1.2, R2.2, SJ1.1, U1.13 (VDD)
VIO: C4.1, JP6.4, U1.8 (VLOGIC)

Notes on the sheet:
J. Bartlett
I2C Address Selection*
*** Frame synchronization digital input. Connected to GND by default
***
Cut trace for external sync
* Two MPU-60X0s can be connected to the same I2C bus
Default Address = 0x68 (pin AD0 is logic low)
Alternative Address =0x69 (pin AD0 is logic high)
The LSB bit of the 7 bit address is determined by the logic level on pin AD0.
** Optional external reference clock input. Connected to GND by default.
Cut trace for external clock
Changes to V11
SCL and SDA were switched on V10, fixed on V11
C2 was mislabled as 10nF, should have been 2.2nF.
Broke out VLOGIC line
BOM changes
New Stencil
YES
C2 is now 2.2nF instead of 10nF
Minor layout changes
Added selectable jumpers to CLK, FSYNC and AD0
Played around with IC footprint.
Changes to V12: -0402 --> 0603 -Changed Z-Axis symbol to reflect proper orientation from circle with x to circle with dot -Changed NET labels in schematic to flags
E. Orosel
v12
Added 4 small tcream squares to middle pad.
Rounded and elongated pads.

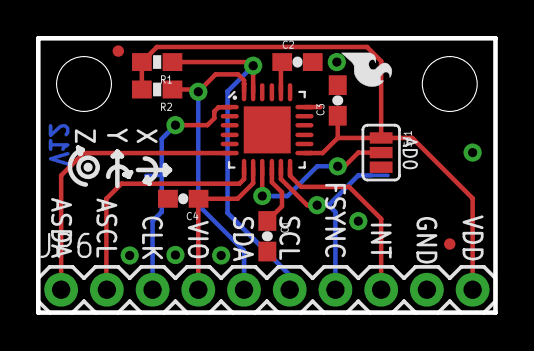
[picture p256: board Triple_Axis_Accelerometer_Gyro_Breakout_-_MPU-6050_v12.brd from above]

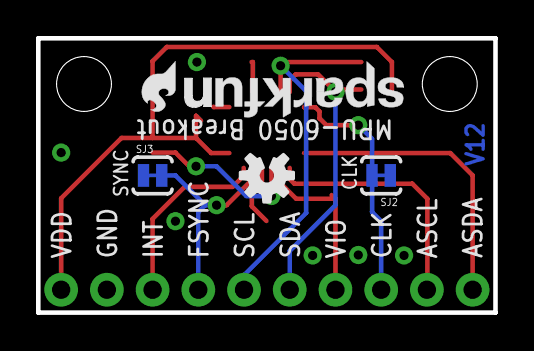
[picture p257: board Triple_Axis_Accelerometer_Gyro_Breakout_-_MPU-6050_v12.brd from below]

Board: 2 copper layers, 25.4 x 15.2 mm, 21 parts (5 on the bottom side), 13 nets.

Other parts of the board:
U$2, U$3: SFE-LOGO-FLAME
U$4: SFE-NEW-WEB
