oldgerman/ODGIRON/Hardware/PCB_Project/ODGIRON-v1.0-F4x1-0412/Stencil/钢网拼版/ODGIRON_steel_0412 - 副本.brd

## EAGLE design Hardware/PCB_Project/ODGIRON-v1.0-F4x1-0412/Stencil/钢网拼版/ODGIRON_steel_0412 - 副本.brd (2021-08-09, an earlier design)

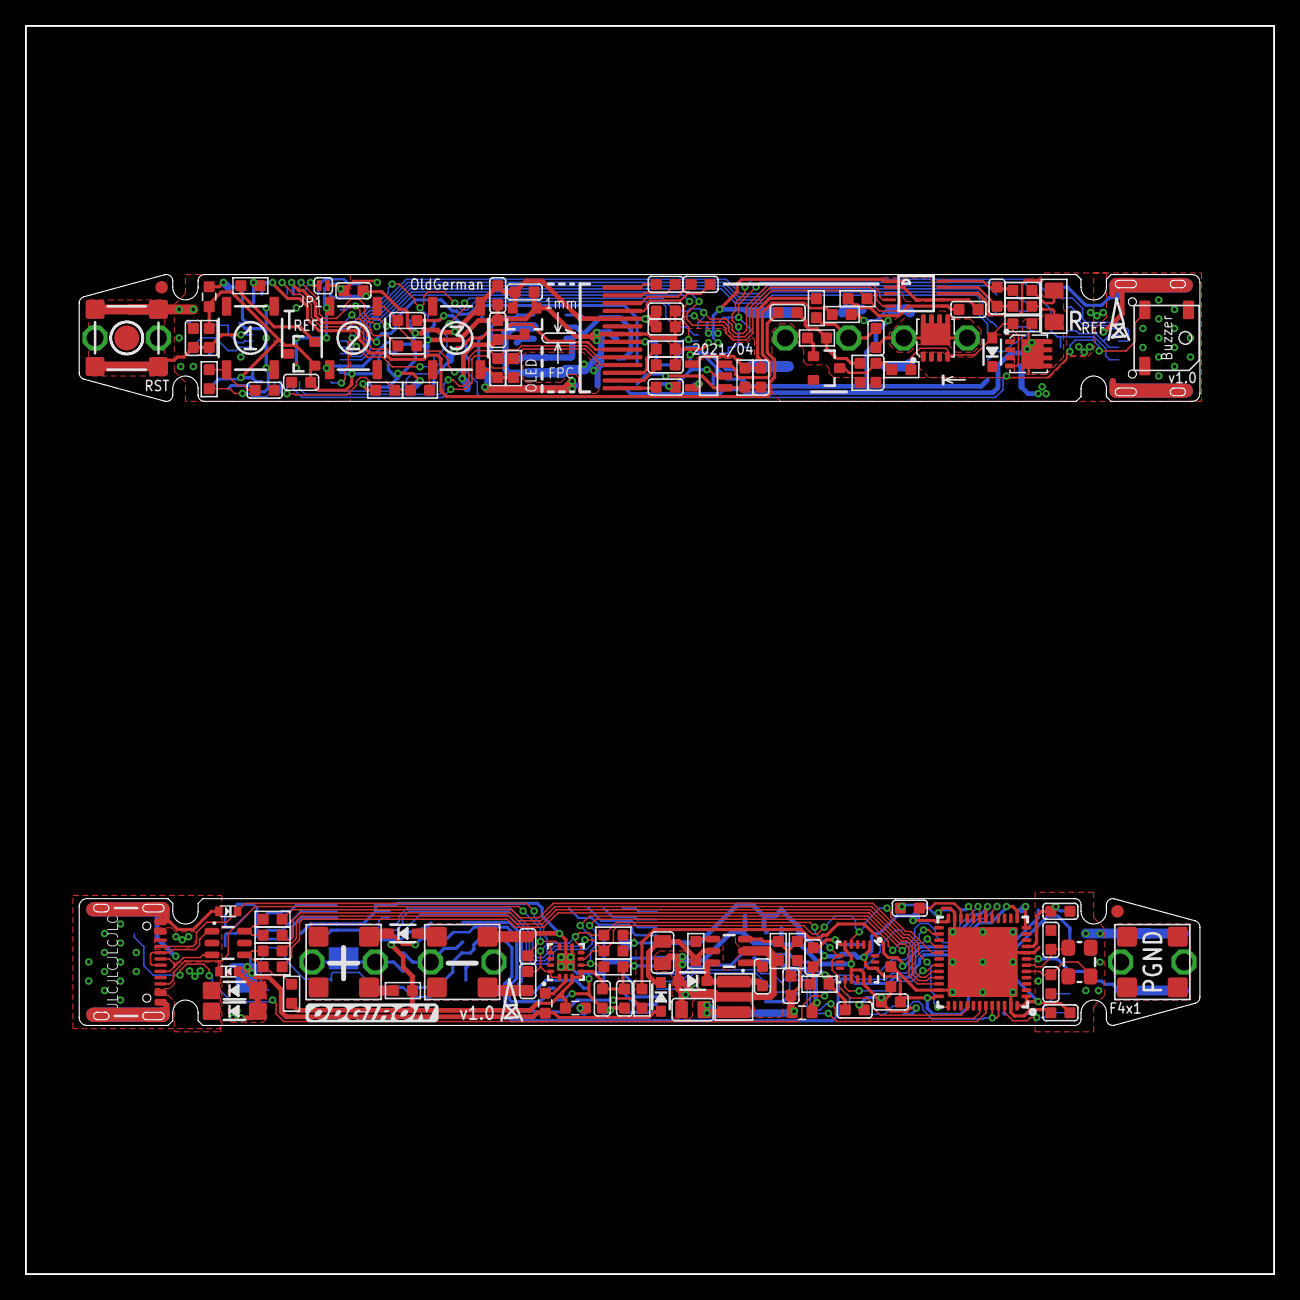
[picture p258: board ODGIRON_steel_0412 - 副本.brd from above]

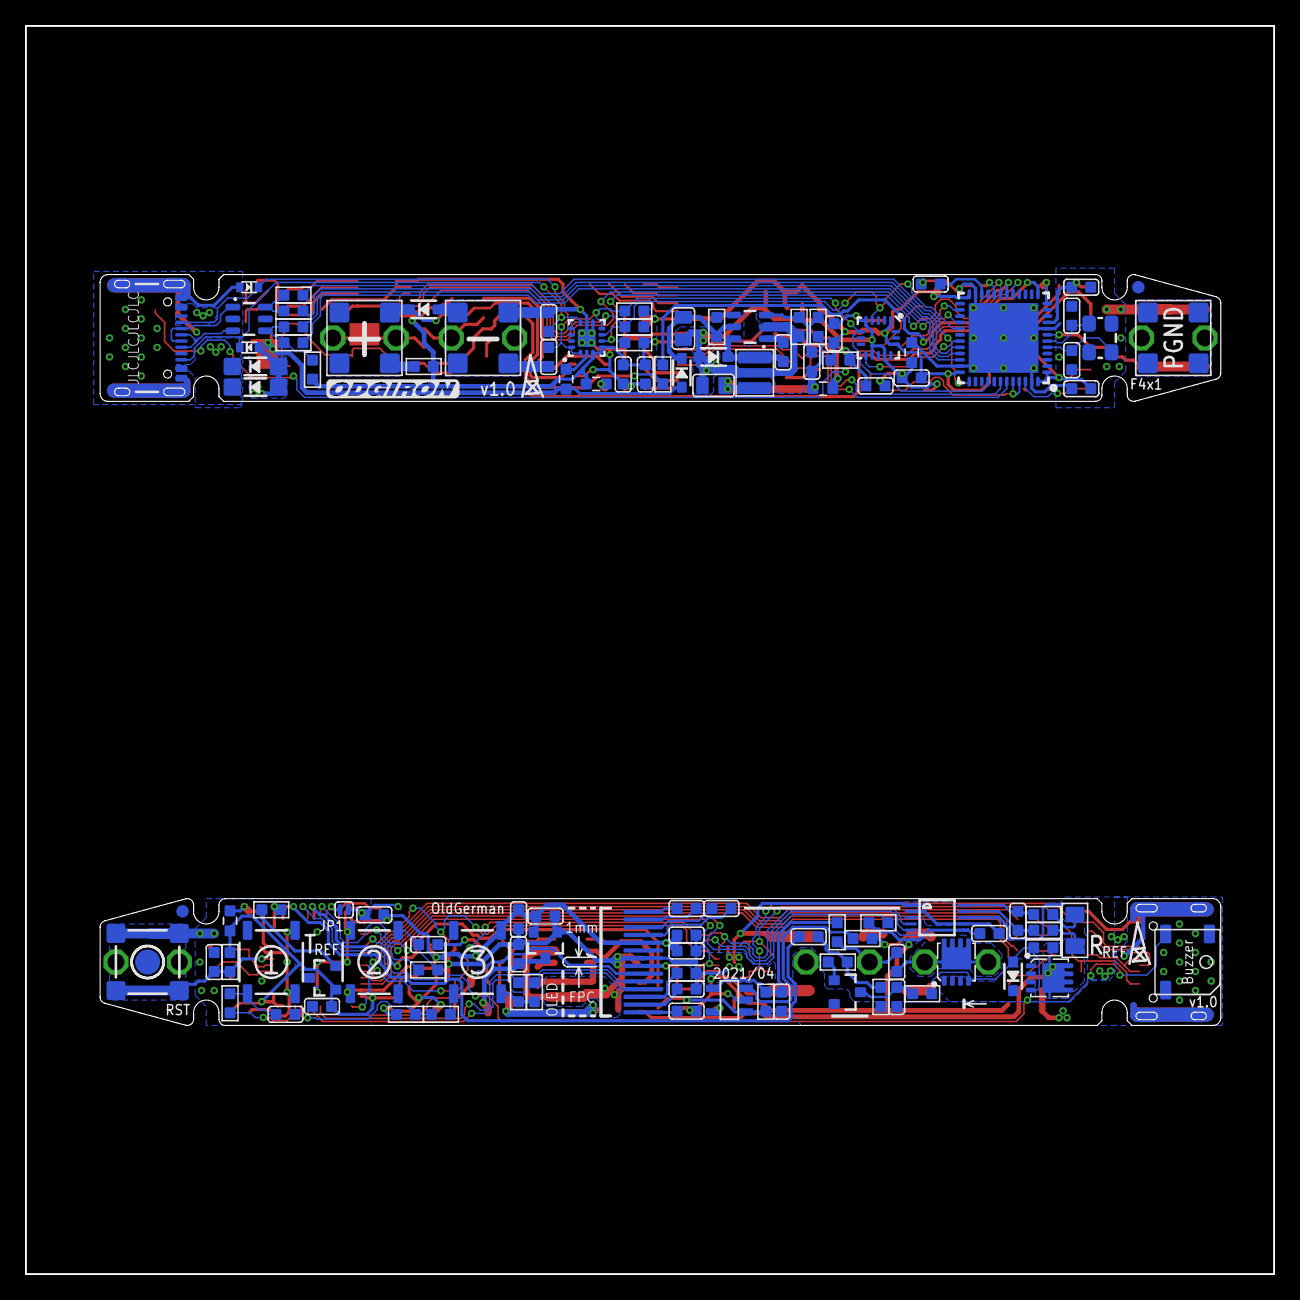
[picture p259: board ODGIRON_steel_0412 - 副本.brd from below]

Board: 2 copper layers, 100.0 x 100.0 mm, 245 parts (122 on the bottom side), 134 nets.

Parts:
AMP1, AMP2: SGM8551XN5G/TR; SOT23-5
BUZ1, BUZ2: BUZZER_5020
C1, C2, C3, C4, C5, C6, C10, C11, C12, C13, C14, C16, C29, C38, C40, C41, C42, C43, C52, C53, C54, C58, C59, C61, C68, C70: 0.1uF/50V; C0603
C7, C23, C49, C69: 4.7uF/16V; C0603
C8, C9, C28, C36: 10pF/50V; C0603
C15, C21, C22, C24, C31, C39, C44, C47, C48, C50, C64, C66: 1uF/16V; C0603
C17, C27, C55, C60: 10nF/50V; C0603
C18, C19, C45, C46: 470pF/50V; C0603
C20, C25, C26, C37, C62, C63, C65, C67: 10uF/10V; C0603
C30, C57: 10uF/25V; C0805
C32, C71: 2.2uF/16V; C0603
C33, C51: 4.7uF/50V; C0805
C34, C35, C56, C72: 100pF/50V; C0603
CP1, CP2: FUSE_CLIPS_01
D1, D4, D7, D9, D15, D16: B5819WS; SOD-323
D2, D5, D11, D12: SMF24A; SOD-123
D3, D10: MMSZ5242BS-7-F; SOD-323
D6, D8, D13, D14: ESD5B5.0ST1; SOD-523
DA1, DA2: INA226; MSOP10
FB1, FB2, FB3, FB4, FB5, FB6, FB7, FB8, FB9, FB10: 1K; F0603
FID1, FID2, FID3, FID4: FIDUCIAL; FIDUCIAL_1MM
J1, J3: USB-C-16P
JP1, JP2: SMT-JUMPER_2_NO_SILK
L1, L2: 33uH CBC3225T330KR; SMD,3.2X2.5X2.5MM
LCD1, LCD2: 0.87inch SSD1306; 0.87INCH_128X32_OLED_SSD1306
LOGO1: OSHW-LOGONO_SILK; DUMMY
PAD1, PAD2, PAD3, PAD4, PAD5, PAD6, PAD7, PAD8, PAD9, PAD10, PAD11, PAD12, PAD13, PAD14, PAD15, PAD16, PAD17, PAD18, PAD19, PAD20, PAD21, PAD22, PAD23, PAD24: PADTP16SQ; TP16SQ
Q1, Q2, Q3, Q5: AON7403; DFN8P-0.65-3X3X0.8MM
Q4, Q6: S8050; SOT23-3
R1, R13, R49, R68: 32.4K; R0603
R2, R50: 124K; R0603
R3, R10, R16, R18, R19, R22, R25, R32, R33, R34, R35, R40, R46, R47, R53, R62: 4.7K; R0603
R4, R15: 1.5K; R0603
R5, R6, R27, R28, R30, R31, R51, R52: 22R; R0603
R7, R12, R23, R26, R41, R45, R56, R60, R64, R67: 1K; R0603
R8, R20, R29, R42, R48, R57: 100K; R0603
R9, R11, R14, R21, R38, R63, R65, R66: 10K; R0603
R17, R39: 560K; R0603
R24, R61: 10mR ±1% ±50ppm/℃; R1206
R36, R37, R54, R55: 10R; R0603
R43, R58: 2.37K ±0.1% ±25ppm/℃; R0603
R44, R59: 750K ±0.1% ±25ppm/℃; R0603
S1, S2, S3, S4, S5, S6, S7, S8: TACTILE_SWITCH_SMD
T1, T2: HAKKO_T12_K-TYPE_WITH_FUSE_CLIPS_X2
TP1, TP2: PGND; TESTPOINT_ROUND_2MM
U1, U13: FUSB302BMPX; QFN14-2.5X2.5MM
U3, U12: STM32F4x1CxU6; QFN48_7X7MM_0.5MM
U4, U14: MP2456GJ; SOT23-6
U5, U15: MCP9700AT-E/TT,or LM50CIM3X; SOT23-3@1
U6, U16: MCP1700T-3302E/TT; SOT23-3
U8, U17: LIS3DH; LGA-16-3X3
VD1, VD2: USBLC6-2SC6; SOT23-6
ZO1, ZO2: 8MHz; 3.2X2.5_KX-7

Connections:
3.9V: C30.1, C35.1, FB1.1, L1.2, R2.1
3.9V1: C57.1, C72.1, FB7.1, L2.2, R50.1
+3V1: C40.2, C41.2, C42.2, C43.1, C44.1, C49.2, C50.2, C53.1, C54.1, C65.2, C66.2, C67.2, DA2.6, FB6.2, FB8.2, LCD2.5, LCD2.8, R15.2, R32.1, R33.1, R34.1, R40.2, R46.2, R47.2, R65.1, R67.2, R68.2, S4.3, S4.4, U12.1, U12.24, U12.36, U12.48, U13.3, U13.4, U15.1, U16.2, U17.1, U17.14
+3V3: C2.1, C4.1, C5.1, C12.2, C13.2, C14.2, C15.1, C20.2, C23.2, C24.2, C37.2, C39.2, DA1.6, FB2.2, FB3.2, LCD1.5, LCD1.8, R3.1, R4.2, R13.2, R16.1, R18.2, R19.2, R22.2, R23.2, R25.1, R38.1, S3.3, S3.4, U1.3, U1.4, U3.1, U3.24, U3.36, U3.48, U5.1, U6.2, U8.1, U8.14
AMP+: AMP1.3, R42.1
AMP+1: AMP2.3, R57.1
AMP-: AMP1.4, C34.2, R43.1, R44.2
AMP-1: AMP2.4, C56.2, R58.1, R59.2
BS: C29.1, U4.1
BS1: C61.1, U14.1
CC1: C18.1, D8.K, J3.A5, U1.1, U1.14
CC2: C19.1, D6.K, J3.B5, U1.10, U1.11
CC3: C46.1, D13.K, J1.B5, U13.10, U13.11
CC4: C45.1, D14.K, J1.A5, U13.1, U13.14
D+: J3.A6, J3.B6, VD1.3
D+1: J1.A6, J1.B6, VD2.3
D-: J3.A7, J3.B7, VD1.1
D-1: J1.A7, J1.B7, VD2.1
DCDC_IN: C33.1, D1.C, R20.2, U4.5
DCDC_IN1: C51.1, D15.C, R48.2, U14.5
EN: R20.1, U4.4
EN1: R48.1, U14.4
GND: AMP1.2, BUZ1.-, C2.2, C3.2, C4.2, C5.2, C6.2, C7.2, C8.1, C9.1, C10.2, C11.1, C12.1, C13.1, C14.1, C15.2, C16.1, C18.2, C19.2, C20.1, C23.1, C24.1, C25.2, C26.2, C27.2, C30.2, C31.1, C32.2, C33.2, C37.1, C39.1, D2.A, D5.A, D6.A, D7.A, D8.A, D9.A, DA1.1, DA1.2, DA1.7, FB4.1, FB4.2, J3.GND, J3.GND2, J3.SHLD1, J3.SHLD2, J3.SHLD3, J3.SHLD4, J3.SHLD5, J3.SHLD6, J3.SHLD7, J3.SHLD8, JP1.1, LCD1.7, PAD5.TP, PAD6.TP, PAD7.TP, PAD8.TP, Q4.2, R1.1, R8.2, R12.1, R17.1, R43.2, S1.1, S1.2, S2.1, S2.2, S5.1, S5.2, T1.1A1, T1.1B1, U1.8, U1.9, U1.THERMAL, U3.8, U3.23, U3.35, U3.47, U3.P$1, U4.2, U5.3, U6.1, U8.5, U8.10, U8.12, VD1.2, ZO1.2, ZO1.4
GND1: AMP2.2, BUZ2.-, C28.1, C36.1, C38.1, C40.1, C41.1, C42.1, C43.2, C44.2, C45.2, C46.2, C49.1, C50.1, C51.2, C53.2, C54.2, C55.2, C57.2, C58.2, C59.1, C62.2, C63.2, C64.1, C65.1, C66.1, C67.1, C68.2, C69.2, C70.2, C71.2, D4.A, D11.A, D12.A, D13.A, D14.A, D16.A, DA2.1, DA2.2, DA2.7, FB9.1, FB9.2, J1.GND, J1.GND2, J1.SHLD1, J1.SHLD2, J1.SHLD3, J1.SHLD4, J1.SHLD5, J1.SHLD6, J1.SHLD7, J1.SHLD8, JP2.1, LCD2.7, PAD17.TP, PAD18.TP, PAD19.TP, PAD20.TP, Q6.2, R29.2, R39.1, R49.1, R58.2, R64.1, S6.1, S6.2, S7.1, S7.2, S8.1, S8.2, T2.1A1, T2.1B1, U12.8, U12.23, U12.35, U12.47, U12.P$1, U13.8, U13.9, U13.THERMAL, U14.2, U15.3, U16.1, U17.5, U17.10, U17.12, VD2.2, ZO2.2, ZO2.4
LDO_IN: C31.2, FB1.2, U6.3
LDO_IN1: C64.2, FB7.2, U16.3
unnamed: R7.2, S3.1, S3.2
unnamed: C11.2, FB2.1, U3.9
unnamed: C21.2, LCD1.2
unnamed: C22.2, LCD1.4
unnamed: C25.1, LCD1.13
unnamed: LCD1.12, R17.2
unnamed: C26.1, LCD1.14
unnamed: C35.2, R1.2, R2.2, U4.3
unnamed: C22.1, LCD1.3
unnamed: C21.1, LCD1.1
unnamed: C3.1, R9.2, S1.3, S1.4
unnamed: D3.C, Q2.1, Q2.2, Q2.3, Q3.1, Q3.2, Q3.3
unnamed: D3.A, Q2.4, Q3.4, R10.2, R35.1
unnamed: C16.2, Q4.3, R35.2
unnamed: Q4.1, R11.1
unnamed: C17.1, R11.2, R12.2
unnamed: C6.1, R14.2, S2.3, S2.4
unnamed: R4.1, R5.1, R27.1, VD1.4
unnamed: C1.1, DA1.10, R36.1
unnamed: C1.2, DA1.9, R37.1
unnamed: R41.2, U5.2
unnamed: R6.1, R28.1, VD1.6
unnamed: FB5.1, U1.2
unnamed: AMP1.5, FB3.1
unnamed: JP1.2, U3.20
unnamed: R26.2, S4.1, S4.2
unnamed: C38.2, FB6.1, U12.9
unnamed: C47.2, LCD2.2
unnamed: C48.2, LCD2.4
unnamed: C62.1, LCD2.13
unnamed: LCD2.12, R39.2
unnamed: C63.1, LCD2.14
unnamed: C72.2, R49.2, R50.2, U14.3
unnamed: C52.1, DA2.10, R54.1
unnamed: C52.2, DA2.9, R55.1
unnamed: C48.1, LCD2.3
unnamed: C47.1, LCD2.1
unnamed: C58.1, R21.2, S6.3, S6.4
unnamed: D10.C, Q1.1, Q1.2, Q1.3, Q5.1, Q5.2, Q5.3
unnamed: D10.A, Q1.4, Q5.4, R53.1, R62.2
unnamed: C59.2, Q6.3, R53.2
unnamed: Q6.1, R63.1
unnamed: C60.1, R63.2, R64.2
unnamed: R56.2, U15.2
unnamed: C68.1, R66.2, S7.3, S7.4
unnamed: R15.1, R30.1, R51.1, VD2.4
unnamed: R31.1, R52.1, VD2.6
unnamed: FB10.1, U13.2
unnamed: AMP2.5, FB8.1
unnamed: JP2.2, U12.20
NRST: C10.1, R23.1, S5.3, S5.4, U3.7
NRST1: C70.1, R67.1, S8.3, S8.4, U12.7
OSC_IN: C8.2, U3.5, ZO1.3
OSC_IN1: C36.2, U12.5, ZO2.3
OSC_OUT: C9.2, U3.6, ZO1.1
OSC_OUT1: C28.2, U12.6, ZO2.1
OUT: AMP1.1, C34.1, R44.1, R45.2
OUT1: AMP2.1, C56.1, R59.1, R60.2
PA2/ADC1: R56.1, U12.12
PA2/ADC2: R41.1, U3.12
PA3/T2C1: C60.2, U12.13
PA3/T2C4: C17.2, U3.13
PA7/T1CH1N/T3C1: BUZ2.+, U12.17
PA7/T1CH1N/T3C2: BUZ1.+, U3.17
PA8/SCL1: DA2.5, R33.2, U12.29, U13.6, U17.4
PA8/SCL3: DA1.5, R3.2, U1.6, U3.29, U8.4
PA10/IT_ACCEL_1: U12.31, U17.9
PA10/IT_ACCEL_2: U3.31, U8.9
PA11/USB_DM: R6.2, U3.32
PA11/USB_DM1: R31.2, U12.32
PA12/USB_DP: R5.2, U3.33
PA12/USB_DP1: R30.2, U12.33
PA13/SWDIO: R27.2, U3.34
PA13/SWDIO1: R51.2, U12.34
PA14/SWCLK: R28.2, U3.37
PA14/SWCLK1: R52.2, U12.37
PB0/ADC1: R60.1, U12.18
PB0/ADC8: R45.1, U3.18
PB1/IT_FUSB1: R34.2, U12.19, U13.5
PB1/IT_FUSB302: R16.2, U1.5, U3.19
PB4/SDA1: DA2.4, R32.2, U12.40, U13.7, U17.6
PB4/SDA3: DA1.4, R25.2, U1.7, U3.40, U8.6
PB6/SCL1: LCD1.10, R19.1, U3.42
PB6/SCL2: LCD2.10, R46.1, U12.42
PB7/SDA1: LCD1.11, R18.1, U3.43
PB7/SDA2: LCD2.11, R40.1, U12.43
PB8&BOOT0_S1: R26.1, R29.1, U12.44, U12.45
PB8&BOOT0_S3: R7.1, R8.1, U3.44, U3.45
PB9/S1: R9.1, U3.46
PB9/S2: R21.1, U12.46
PB13/IT_INA1: DA2.3, R65.2, U12.26
PB13/IT_INA226: DA1.3, R38.2, U3.26
PB15/S1: R66.1, U12.28
PB15/S2: R14.1, U3.28
PGND1: CP1.1A, CP1.1B, PAD9.TP, PAD10.TP, PAD11.TP, PAD12.TP, TP1.P$1
PGND2: CP2.1A, CP2.1B, PAD21.TP, PAD22.TP, PAD23.TP, PAD24.TP, TP2.P$1
RES_3.3V: C7.1, LCD1.9, R22.1
RES_3.3V1: C69.1, LCD2.9, R47.1
SW: C29.2, D7.C, L1.1, U4.6
SW1: C61.2, D4.C, L2.1, U14.6
T12+: C27.1, D9.C, PAD1.TP, PAD2.TP, PAD3.TP, PAD4.TP, Q3.5, Q3.6, Q3.7, Q3.8, Q3.9, R13.1, R42.2, T1.1A, T1.1B
T12+1: C55.1, D16.C, PAD13.TP, PAD14.TP, PAD15.TP, PAD16.TP, Q1.5, Q1.6, Q1.7, Q1.8, Q1.9, R57.2, R68.1, T2.1A, T2.1B
VBUS-C: D1.A, FB5.2, Q2.5, Q2.6, Q2.7, Q2.8, Q2.9, R10.1, R24.1, R37.2
VBUS-C1: D15.A, FB10.2, Q5.5, Q5.6, Q5.7, Q5.8, Q5.9, R55.2, R61.1, R62.1
VCAP1: C32.1, U3.22
VCAP2: C71.1, U12.22
VUSB_IN: D2.C, D5.C, DA1.8, J3.VBUS1, J3.VBUS2, R24.2, R36.2
VUSB_IN1: D11.C, D12.C, DA2.8, J1.VBUS1, J1.VBUS2, R54.2, R61.2
