oldgerman/ODGIRON/Software/workspace_ODGIRON/PROJECT_STM32F401/Core/Inc/main.h

#define SCL1_GPIO_Port GPIOB
#define TIM1_PSC_SLOW_PWM 29680
#define BUZZER_CHANNEL TIM_CHANNEL_2
#define SCL3_Pin GPIO_PIN_8
#define SDA1_Pin GPIO_PIN_7
#define SDA3_GPIO_Port GPIOB
#define TREF_TEMP_ADC1_CHANNEL ADC_CHANNEL_2
#define TIM1_PSC_FAST_PWM 14840
#define TEMP_TEMP_ADC1_CHANNEL ADC_CHANNEL_8
#define SDA1_GPIO_Port GPIOB
#define SDA3_Pin GPIO_PIN_4
#define SCL1_Pin GPIO_PIN_6
#define SCL3_GPIO_Port GPIOA
#define TREF_TEMP_Pin GPIO_PIN_2
#define TREF_TEMP_GPIO_Port GPIOA
#define BUZZER_OUT_Pin GPIO_PIN_7
#define BUZZER_OUT_GPIO_Port GPIOA
#define TIP_TEMP_Pin GPIO_PIN_0
#define TIP_TEMP_GPIO_Port GPIOB
#define IT_FUSB302B_Pin GPIO_PIN_1
#define IT_FUSB302B_GPIO_Port GPIOB
#define IT_FUSB302B_EXTI_IRQn EXTI1_IRQn
#define KEY_OK_Pin GPIO_PIN_15
#define KEY_OK_GPIO_Port GPIOB
#define KEY_B_Pin GPIO_PIN_8
#define KEY_B_GPIO_Port GPIOB
#define KEY_A_Pin GPIO_PIN_9
#define KEY_A_GPIO_Port GPIOB
