oldgerman/ODGIRON/Software/workspace_ODGIRON/HARDWARE/Buttons/Buttons.hpp

/*
 * Buttons.h
 *
 *  Created on: 29 May 2020
 *      Author: Ralim
 *      Modify: OldGerman
 */
#ifndef INC_BUTTONS_H_
#define INC_BUTTONS_H_

#include "main.h"

#ifdef __cplusplus

// Returns what buttons are pressed (if any)


// Helpers
void waitForButtonPressOrTimeout(uint32_t timeout);
void waitForButtonPress();

extern "C" {
#endif

//7种状态测试OK
typedef enum{
  BUTTON_NONE      = 0,  /* No buttons pressed / < filter time*/
  //3的倍数，非5的倍数
  BUTTON_F_SHORT   = 3,  /* User has pressed the front button*/
  BUTTON_B_SHORT   = 6,  /* User has pressed the back  button*/
  BUTTON_BOTH      = 9, /* User has pressed both buttons*/
  BUTTON_OK_SHORT  = 12, /* OK键短按 */
  //5的倍数，非3的倍数
  BUTTON_F_LONG    = 5,  /* User is  holding the front button*/
  BUTTON_B_LONG    = 10,  /* User is  holding the back button*/
  BUTTON_BOTH_LONG = 20, /* User is holding both buttons*/
  BUTTON_OK_LONG   = 25,/* OK键长按 */
  //取素数
  BUTTON_IDLE	   = 73,/* 用于不同Page间切换时提供断点*/
  BUTTON_FROZEN    = 79 /*用于切换时的冻结时间*/

  /*
   * Note:
   * Pressed means press + release, we trigger on a full \__/ pulse
   * holding means it has gone low, and been low for longer than filter time
   */
}ButtonState;
extern ButtonState buttons;

//3种变化状态
typedef enum{
  BUTTON_EX_NONE      		= 0,
  BUTTON_EX_DONE      		= 1,
  BUTTON_EX_SHORT_TO_LONG 	= 2
}ButtonExchange;
extern ButtonExchange buttonExchange;

extern bool buttonChanged;
extern bool buttonIsBeep;
extern uint32_t lastButtonTime;
uint8_t getButtonA();
uint8_t getButtonB();
uint8_t getButtonOK();
extern bool waitingToChooseOneFromTwo();
ButtonState readButtonState();
ButtonState getButtonState();
#ifdef __cplusplus
}
#endif
#endif /* INC_BUTTONS_H_ */
