oldgerman/ODGIRON/Software/workspace_ODGIRON/HARDWARE/Src/TipThermoModel.cpp

/*
 * TipThermoModel.cpp
 *
 *  Created on: 7 Oct 2019
 *      Author: ralim
 */


#include "BSP.h"
#include "Settings.h"
#include "Utils.h"
#include "power.hpp"
#include "TipThermoModel.hpp"
#include "configuration.h"

#ifdef TEMP_uV_LOOKUP_HAKKO
const uint16_t uVtoDegC[] = {
    //
    //
    0,     0,   //
    266,   10,  //
    522,   20,  //
    770,   30,  //
    1010,  40,  //
    1244,  50,  //
    1473,  60,  //
    1697,  70,  //
    1917,  80,  //
    2135,  90,  //
    2351,  100, //
    2566,  110, //
    2780,  120, //
    2994,  130, //
    3209,  140, //
    3426,  150, //
    3644,  160, //
    3865,  170, //
    4088,  180, //
    4314,  190, //
    4544,  200, //
    4777,  210, //
    5014,  220, //
    5255,  230, //
    5500,  240, //
    5750,  250, //
    6003,  260, //
    6261,  270, //
    6523,  280, //
    6789,  290, //
    7059,  300, //
    7332,  310, //
    7609,  320, //
    7889,  330, //
    8171,  340, //
    8456,  350, //
    8742,  360, //
    9030,  370, //
    9319,  380, //
    9607,  390, //
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

};
#endif

const int uVtoDegCItems = sizeof(uVtoDegC) / (2 * sizeof(uint16_t));

uint32_t TipThermoModel::convertuVToDegC(uint32_t tipuVDelta) { return Utils::InterpolateLookupTable(uVtoDegC, uVtoDegCItems, tipuVDelta); }


/*
 * The hardware is laid out  as a non-inverting op-amp
 * There is a pullup of 39k(TS100) from the +ve input to 3.9V (1M pulup on TS100)
 *
 * The simplest case to model this, is to ignore the pullup resistors influence, and assume that its influence is mostly constant
 * -> Tip resistance *does* change with temp, but this should be much less than the rest of the system.
 *
 * When a thermocouple is equal temperature at both sides (hot and cold junction), then the output should be 0uV
 * Therefore, by measuring the uV when both are equal, the measured reading is the offset value.
 * This is a mix of the pull-up resistor, combined with tip manufacturing differences.
 *
 * All of the thermocouple readings are based on this expired patent
 * - > https://patents.google.com/patent/US6087631A/en
 *
 * This was bought to my attention by <Kuba Sztandera>
 */
volatile uint32_t lastuv = 0;
uint32_t          TipThermoModel::convertTipRawADCTouV(uint16_t rawADC, bool skipCalOffset) {
  // This takes the raw ADC samples, converts these to uV
  // Then divides this down by the gain to convert to the uV on the input to the op-amp (A+B terminals)
  // Then remove the calibration value that is stored as a tip offset
  uint32_t vddRailmVX10 = 33000; // The vreg is +-2%, but we have no higher accuracy available
  // 4096 * 8 readings for full scale
  // Convert the input ADC reading back into mV times 10 format.
  uint32_t rawInputmVX10 = (rawADC * vddRailmVX10) / (4096 * 8);

  uint32_t valueuV = rawInputmVX10 * 100; // shift into uV
  // Now to divide this down by the gain
  valueuV /= OP_AMP_GAIN_STAGE;

  if (systemSettings.CalibrationOffset && skipCalOffset == false) {
    // Remove uV tipOffset
    if (valueuV > systemSettings.CalibrationOffset)
      valueuV -= systemSettings.CalibrationOffset;
    else
      valueuV = 0;
  }
  lastuv = valueuV;
  return valueuV;
}

uint32_t TipThermoModel::convertTipRawADCToDegC(uint16_t rawADC) {
	uint32_t val = convertTipRawADCTouV(rawADC);
	return convertuVToDegC(val);
}
uint32_t TipThermoModel::convertTipRawADCToDegF(uint16_t rawADC) {
	uint32_t val = convertTipRawADCTouV(rawADC);
	return convertuVToDegF(val);
}

uint32_t TipThermoModel::convertuVToDegF(uint32_t tipuVDelta) { return convertCtoF(convertuVToDegC(tipuVDelta)); }

uint32_t TipThermoModel::convertCtoF(uint32_t degC) {
  //(Y °C × 9/5) + 32 =Y°F
  return (32 + ((degC * 9) / 5));
}

uint32_t TipThermoModel::convertFtoC(uint32_t degF) {
  //(Y°F − 32) × 5/9 = Y°C
  if (degF < 32) {
    return 0;
  }
  return ((degF - 32) * 5) / 9;
}
uint32_t TipThermoModel::getTipInC(bool sampleNow) {
  int32_t currentTipTempInC = TipThermoModel::convertTipRawADCToDegC(getTipRawTemp(sampleNow));
  currentTipTempInC += getHandleTemperature(sampleNow) / 10; // Add handle offset

  // Power usage indicates that our tip temp is lower than our thermocouple temp.
  // I found a number that doesn't unbalance the existing PID, causing overshoot.
  // This could be tuned in concert with PID parameters...

  if (currentTipTempInC < 0)
    return 0;
  return currentTipTempInC;
}

uint32_t TipThermoModel::getTipInF(bool sampleNow) {
  uint32_t currentTipTempInF = getTipInC(sampleNow);
  currentTipTempInF          = convertCtoF(currentTipTempInF);
  return currentTipTempInF;
}

uint32_t TipThermoModel::getTipMaxInC() {
  uint32_t maximumTipTemp = TipThermoModel::convertTipRawADCToDegC(0x7FFF - (21 * 3)); // back off approx 5 deg c from ADC max
  maximumTipTemp += getHandleTemperature(false) / 10;                                      // Add handle offset
  return maximumTipTemp - 1;
}
