oldgerman/ODGIRON/Software/workspace_ODGIRON/SOFTWARE/Inc/Translation.h

/*
 * Translation.h
 *
 *  Created on: 31Aug.,2017
 *      Author: Ben V. Brown
 */

#ifndef TRANSLATION_H_
#define TRANSLATION_H_
#include "stdint.h"
#include "unit.h"
//#include "fontTables.h"
extern const uint8_t USER_FONT_12[];
extern const uint8_t USER_FONT_6x8[];

extern const char *SettingsShortNames[29][2];
extern const char *SettingsDescriptions[29];
extern const char *SettingsMenuEntries[4];

extern const char *SettingsCalibrationDone;
extern const char *SettingsCalibrationWarning;
extern const char *SettingsResetWarning;
extern const char *UVLOWarningString;
extern const char *UndervoltageString;
extern const char *InputVoltageString;
extern const char *WarningTipTempString;
extern const char *BadTipString;

extern const char *SleepingSimpleString;
extern const char *SleepingAdvancedString;
extern const char *WarningSimpleString;
extern const char *WarningAdvancedString;
extern const char *SleepingTipAdvancedString;
extern const char *IdleTipString;
extern const char *IdleSetString;
extern const char *TipDisconnectedString;
extern const char *SolderingAdvancedPowerPrompt;
extern const char *OffString;

//-----------------------------------------make_translation.py----------------------------------------------------------
//Symbol ASCII符号组，由Translation文件夹的make_translation.py完成，放在st源码里编译不好吗
extern const char *SymbolPlus;
extern const char *SymbolMinus;
extern const char *SymbolSpace;
extern const char *SymbolDot;
extern const char *SymbolDegC;
#ifdef ENABLED_FAHRENHEIT_SUPPORT
extern const char *SymbolDegF;
#endif
extern const char *SymbolMinutes;
extern const char *SymbolSeconds;
extern const char *SymbolWatts;
extern const char *SymbolVolts;
extern const char *SymbolDC;
extern const char *SymbolCellCount;
extern const char *SymbolVersionNumber;

//DebugMenu ASCII符号组，由Translation文件夹的make_translation.py完成，放在st源码里编译不好吗
extern const char *DebugMenu[];
#endif /* TRANSLATION_H_ */

//-------------------------------------------------么有的符号-----------------------------------------------------------
//这些字符串从translation_???_HK.json构建, 我从translation_en.json构建，注意translation_HK.json里有中文字符的
extern const char *ResetOKMessage;					//
extern const char *YourGainMessage;				//
extern const char *SettingsResetMessage;
extern const char *NoAccelerometerMessage;
extern const char *NoPowerDeliveryMessage;
extern const char *LockingKeysString;
extern const char *UnlockingKeysString;
extern const char *WarningKeysLockedString;
extern const char *SelfCheckIsOK;

extern const char *SettingTrueChar;
extern const char *SettingFalseChar;
extern const char *SettingRightChar;
extern const char *SettingLeftChar;
extern const char *SettingAutoChar;


//以下老版本的有。。。
//焊接睡眠
extern const char *SettingStartSolderingChar;
extern const char *SettingStartSleepChar;
extern const char *SettingStartSleepOffChar;
extern const char *SettingStartNoneChar;
//灵敏度
extern const char *SettingSensitivityOff;
extern const char *SettingSensitivityLow;
extern const char *SettingSensitivityMedium;
extern const char *SettingSensitivityHigh;

extern const char *SettingLockDisableChar;
extern const char *SettingLockBoostChar;
extern const char *SettingLockFullChar;
extern const char *SettingFastChar;
extern const char *SettingSlowChar;


//extern const char *TipModelStrings[];
