oldgerman/ODGIRON/Software/workspace_ODGIRON/SOFTWARE/share/dtostrf.h

/*
  dtostrf - Emulation for dtostrf function from avr-libc
  Copyright (c) 2013 Arduino.  All rights reserved.
  Written by Cristian Maglie <c.maglie@bug.st>

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
  You should have received a copy of the GNU Lesser General Public
  License along with this library; if not, write to the Free Software
  Foundation, Inc., 51 Franklin St, Fifth Floor, Boston, MA  02110-1301  USA
*/

#ifndef __DTOSTRF_H
#define	__DTOSTRF_H
#include "stdio.h"
#ifdef __cplusplus
extern "C" {
#endif

void dtostrf(double val, int len, int prec, char* buf, uint8_t buf_len);

#ifdef __cplusplus
}
#endif

#endif
