oldgerman/ODGIRON/Software/workspace_ODGIRON/BSP/Inc/IRQ.h

/*
 * Irqs.h
 *
 *  Created on: 30 May 2020
 *      Author: Ralim
 */

#ifndef BSP_MINIWARE_IRQ_H_
#define BSP_MINIWARE_IRQ_H_

#include <Threads.hpp>
#include "BSP.h"
#include "I2C_Wrapper.h"
#include "Setup.h"
#include "main.h"
#ifdef STM32F1
#include "stm32f1xx_hal.h"
#elif defined(STM32F4)
#include "stm32f4xx_hal.h"
#endif

#ifdef __cplusplus
extern "C" {
#endif
extern bool ADC_Injected_Callback_Mark;	//ADC HAL_ADCEx_InjectedConvCpltCallback标记
//以下对HAL的__weak回调函数重写
void HAL_ADCEx_InjectedConvCpltCallback(ADC_HandleTypeDef *hadc);
void HAL_ADC_ConvCpltCallback(ADC_HandleTypeDef *hadc);
void HAL_ADC_ConvHalfCpltCallback(ADC_HandleTypeDef *hadc);
void HAL_I2C_ErrorCallback(I2C_HandleTypeDef *hi2c);
void HAL_I2C_AbortCpltCallback(I2C_HandleTypeDef *hi2c);
void HAL_I2C_MasterTxCpltCallback(I2C_HandleTypeDef *hi2c);
void HAL_I2C_MasterRxCpltCallback(I2C_HandleTypeDef *hi2c);
void HAL_I2C_MemTxCpltCallback(I2C_HandleTypeDef *hi2c);
void HAL_I2C_MemRxCpltCallback(I2C_HandleTypeDef *hi2c);
void HAL_GPIO_EXTI_Callback(uint16_t);

#ifdef __cplusplus
}
#endif
#endif /* BSP_MINIWARE_IRQ_H_ */
